ericbusboom/garage-renovation/report/05-architectural-design/README.md

# 05 — Architectural Design

This section contains the selected architectural scheme and coordinated geometry. It includes site/demolition plans, floor and roof plans, elevations, sections, enlarged details, schedules, materials, and explanatory renderings.

Alternatives stay in working folders unless a concise comparison is needed to explain a recorded decision.

## Required outputs

- design narrative
- architectural drawing set
- native editable and neutral exchange models
- door, window, finish, room/use, and equipment schedules
- selected renderings labeled as illustrative

## Current draft study

[ARCH-006 — Floor plan study](floor-plan-study/floor-plan-study.pdf), **revision 4**, 2026-09-15, status `draft`.

One combined plan shows the upper structure, full-width loft, columns, possible ground-floor extension and new north door bay. East-wall framing is marked as optional. WBN is removed; N1–N2 spacing is 16 ft center-to-center. S3 aligns with E-S, and E-M/B aligns with W3.

[Editable drawing, coordinates and study notes](floor-plan-study/README.md). ARCH-002 remains planned.

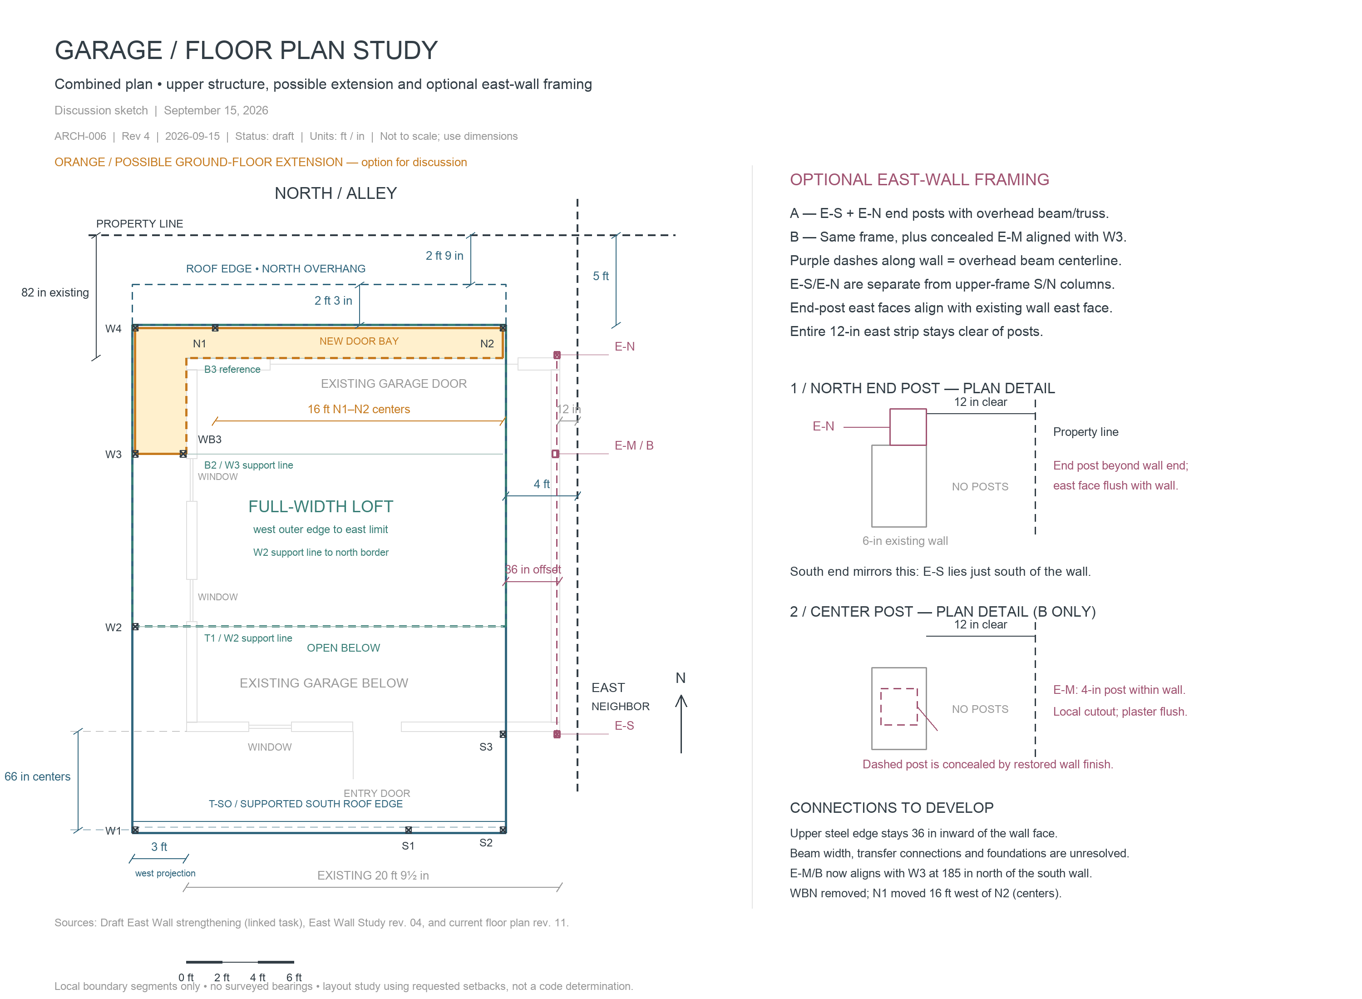
[picture p1: report/05-architectural-design/floor-plan-study/floor-plan-study.png]
Combined floor plan study
