ericbusboom/garage-renovation/report/appendices/README.md

# Appendices

Appendices support the report without interrupting the main narrative. Suitable material includes authoritative-source registers, selected option comparisons, calculation data, meeting minutes, field notes, and referenced product information.

Every appendix needs a document ID, manifest entry, provenance, status, and a reference from a main report section. Do not use this directory as overflow storage.
