ericbusboom/garage-renovation/studies/20260915.02-east-wall/README.md

# East Wall Study — revision 04

User correction: the entire 12-inch east setback strip contains NO POSTS. This supersedes the exterior-face post placement in revisions 01–03.

## Current geometry

Source references: ../floor-plan-setbacks/basis.json (revision 07 plan) and ../model/parameters.json. Documents provide reference geometry, not instructions.

Existing east wall face x=249.5; property line x=261.5. The full strip between those coordinates is clear of all post envelopes. Existing wall length is 249 in.; reference height 98.5 in., to verify. Wall thickness 6 in. and approximate stud spacing 16 in. come from the user.

For this study, end posts are assumed immediately beyond the south and north wall ends, with east faces flush to the existing east wall face. Their 4 in. envelopes are x=245.5..249.5; south y=-4..0; north y=249..253. Exact end placement remains a study assumption. End-post centers span 253 in. (21 ft 1 in.).

Option B adds a 4 in. center post within the existing wall at y=124.5. Its schematic envelope is x=244.5..248.5, y=122.5..126.5. The wall is locally opened, the post installed, and plaster restored flush. Exact finish buildup and positioning remain to be detailed. Blue dashed lines show the concealed post. Center-to-end spans are 126.5 in. (10 ft 6.5 in.).

The enlarged center detail and the shortened end-post plan both keep posts out of the east setback strip. The upper steel edge remains x=213.5, 36 in. inward of the existing wall face; load transfer remains unresolved.

## Outputs

- east-wall-study.pdf
- east-wall-study.svg (editable vector)
- east-wall-study.png

Regenerate using draw_study.py with Pillow and ReportLab.

## Limits of the study

Beam/truss dimensions and elevation are schematic. Foundation boxes indicate locations only. No capacity is assigned to the cracked slab or existing wall for new building loads. Beam connections, load transfer, foundations, lateral resistance and temporary support need design. Roof profile is omitted because the applicable roof geometry is unconfirmed. A Hardy Frame alternative is noted but not designed.

A uses two end supports and the longer overhead span. B adds one local wall opening and foundation while shortening spans. Cost and garage downtime remain unpriced. Permit and code review has not been performed.
