ericbusboom/garage-renovation/studies/20260927.01-patio-awning/setback-research.md

# Patio awning near the property line — San Diego code research

2026-09-29. Working research note, not a permit determination. Parcel facts from LAND-006 (report/03-land-use-and-permitting/setback-extension-research.md): 1370 Wilbur Ave, RS-1-7, Coastal Overlay N-APP-2 (non-appealable), lot ≈ 49 × 122 ft.

## Answer in brief

With posts on the west fence line the awning is inside the required side yard, and the City's rule for this kind of structure is **5 ft from any property line**. The distances that matter:

| Distance from the property line | What the code says |
|---|---|
| 0 to under 2 ft | CRC Table R302.1(1): roof projections **not allowed**. SDMC: no residential projection or patio rule allows it. |
| 2 ft to under 2 ft 6 in | CRC allows a projection with 1-hr underside, heavy timber or FRT wood; SDMC still bars it (every projection rule stops at 2′-6″). |
| 2 ft 6 in to under 5 ft | SDMC allows only building-attached projections: eaves (a)(1), and openly supported projections/trellises (a)(2) that are ≥ 50 % open in plan, up to 6 ft or half the yard deep. A solid fabric sheet on posts is neither. CRC: 1-hr underside or heavy timber/FRT for projections under 5 ft. |
| 5 ft and more | SDMC §131.0461(a)(8): patio structures may sit in the side or rear yard. |
| Outside the required yard (side 4 ft, or 8 % of width ≈ 3.9 ft; rear 13 ft, alley credit may leave 5 ft) | No encroachment rule needed. Permit-exempt if ≤ 300 sf, ≤ 12 ft high and not in any yard (§129.0203(a)(12)). |

So a fabric roof on the P2–P3–P4 fence posts does not fit any by-right rule. The posts stop being "fence" once they carry the awning: SDMC defines a fence as a barrier that "supports no load other than its own weight."

## Sources read

- **SDMC §131.0461(a)** (Ch 13 Art 1 Div 4, 9-2026 edition), permitted projections and encroachments in RS zones:
  - (1) eaves: ≤ 6 ft or 50 % of yard into it, **not closer than 2′-6″** to the line, 6′-8″ clearance.
  - (2) openly supported projections incl. trellises: ≤ eave height, **≥ 50 % open in plan**, ≤ 6 ft or 50 % of yard, **not closer than 2′-6″**, 6′-8″ clear. (Diagram 131-04T shows them projecting from a building wall.)
  - (8) **patio structures** in side or rear yard: **not closer than 5 ft to any property line**, open on at least three sides except columns ≤ 18 × 18 in, columns ≥ 8 ft on centre, roof no higher than the house eave or second-floor sill.
  - (12) non-habitable accessory buildings (the garage route in LAND-006): no stated minimum, ≤ 15 ft high, ≤ 30 ft long in a setback, ≤ 525 sf GFA.
- **SDMC §113.0103 definitions:** "Awning" is supported entirely from a building's exterior wall, so a post-supported sheet is not an awning under the Code. "Fence" supports no load but its own weight. "Structure" includes a post or shelter.
- **SDMC §129.0203(a)(12):** patio covers are exempt from a building permit if ≤ 300 sf projected roof, not in any yard, ≤ 12 ft high, and not in the appealable Coastal area or a Planned Development. (a)(2): fences ≤ 7 ft need no permit. (a)(10): wall-hung window awnings ≤ 54 in projection.
- **IB 206 Patio Covers** (rev. 3-2026): one-story, ≤ 12 ft, open on two or more sides; fire separation per CRC "based on the distance … from a real or assumed lot line"; Class A roof covering assembly; lists the Coastal Zone as needing a permit, which is stricter than the SDMC text.
- **SDMC §142.0310(d):** fences in side and rear yards up to 9 ft; anything above 6 ft must be open fence.
- **SDMC §126.0704(a):** improvements to existing structures are exempt from a Coastal Development Permit unless on a beach or bluff, adding ≥ 10 % floor area, intensifying use, etc. A patio cover here should be exempt; confirm at intake.
- **CRC 2025 Table R302.1(1):** projections under 2 ft fire separation distance are not allowed; 2 to under 5 ft need 1-hr underside, heavy timber or fire-retardant-treated wood.

## What it means for this design

- Fabric plan area is about 162 sf (under the 300 sf exemption size), but the exemption is lost because the awning is in a yard.
- **Posts P2, P3 and P4 are on the line.** To comply by right, the awning's edge and any posts carrying it would have to stay 5 ft off the west line, and 5 ft off the rear line if P1–P2 is near it. About 64 sf of the current 162 sf lies within 5 ft of the west line.
- The pillar end (T1, T2) is part of the garage, which already sits in the east setback under (a)(12). Whether the City would treat a fabric roof attached to it as part of that accessory building is an open question. It would have to count toward the 30 ft and 525 sf limits and stay one story; an open-sided cover is not obviously a "building."
- Water: about 40 % of the roof sheds off the P2–P3 edge on the fence. Nothing found in the zoning code on this, but dumping roof water onto a neighbour is a civil-nuisance risk; a gutter along that edge is advisable in any scheme.
- Fabric: IB 206 asks for a Class A roof covering; fabric may need a listed flame-resistant (e.g. NFPA 701) material, which plan check would decide.

## Open questions for DSD (a free 15-min counter or phone consult)

1. Is a fabric shade sail on permanent posts a "patio structure" under §131.0461(a)(8)?
2. Can it attach to the garage (in the east setback under (a)(12)) and be treated as part of that accessory structure?
3. Where is the rear lot line relative to P1–P2, and does alley credit set the rear yard at 5 ft?
4. Is a Class A covering required for fabric, or will a flame-resistant listed fabric do?

## Fabric-specific search (2026-09-29, second pass)

Question: does a fabric awning or shade sail fall under different rules than a built patio cover?

**Short answer: no fabric exemption was found. The fabric gets no closer to the line, and it adds two material requirements: a Class A roof rating and flame-resistant fabric.**

### San Diego Municipal Code

- Every division of SDMC Chapters 11–14 was downloaded and searched for fabric, canvas, shade sail, shade cloth, membrane, tent and canopy. The only hits are campground tents (§141.06xx) and the adoption of CBC Appendix Q tents for emergency housing. The Land Development Code has **no rule for shade sails or fabric structures**, so the City classifies one under its existing terms.
- "Structure" includes any "post … or shelter" composed of parts joined together (§113.0103). A sail on posts is a structure. "Awning" requires support entirely from a building wall, so a post-supported sail is not an awning under the SDMC.
- §149.0107 adopts **CRC Appendix BF, Patio Covers**. BF102.1 defines a patio cover as "a structure with open or glazed walls that is used for recreational, outdoor living purposes associated with a dwelling unit." It sets no roof material, so a fabric roof fits the definition. BF101.2 says patio covers may not be used as "carports, garages, storage rooms or habitable rooms." A work patio sheltering storage cabinets could be classed instead as an accessory structure under the main CRC; the yard rules apply either way.

### Building and fire codes on fabric

- **CBC §3102 membrane structures** (tensile membrane, membrane-covered cable, etc.) erected **180 days or longer**: designed to ASCE 55. The membrane must be noncombustible or flame resistant per CCR Title 19 Div 1 Ch 8, i.e. State Fire Marshal-listed fabric. A sail tensioned between posts and a mast by cables is a tensile membrane structure. The CRC has no membrane chapter, so a plan checker would likely apply this through engineered design.
- **CFC §3101.1 Exception 4:** "Tensioned membrane roof materials supported by rigid frames or installed on a mast and cable system" that conform to a building-code type of construction are not tents. They are regulated as buildings/structures, not by the fire code's tent chapter.
- **CBC §3105 awnings and canopies:** fabric coverings must pass NFPA 701 or equivalent. Exception: the fire-propagation and flame-spread tests do not apply to awnings on detached one- and two-family dwellings. The sentence requiring fabrics to be flame resistant per Title 19 is not excepted.
- **Roof rating:** San Diego amendment **CRC R902.1.4: "All newly constructed roofs shall be covered with a fire-retardant roof covering that is at least Class 'A'."** IB 206 repeats this for patio covers ("Roofing materials must be a Class A-listed roof covering assembly"). Base CRC R902.1 also requires a rated covering where the roof edge is less than 3 ft from a lot line. Class A is by ASTM E108 / UL 790. PTFE-coated fiberglass architectural membrane is sold as Class A; most shade-sail fabrics (HDPE knit, many PVC-coated polyesters) carry flame-resistance (NFPA 701 / SFM) listings, not a roof class. Check the maker's E108 listing before choosing fabric.

### Temporary use

- Under the CFC, fabric up **less than 180 days in 12 months** is a temporary tent/membrane structure. Open-sided tents up to 700 sf need no fire permit, but they need 12 ft of clearance to structures, and §3103.7.2 keeps tents 20 ft from lot lines. Attached to the garage pillar and posted on the fence, it fails both, so the temporary route gives no relief near the line. Permanent posts remain structures for zoning in any case.

### Effect on the distance answer

Unchanged. Zoning does not care what the roof is made of: the 5 ft patio-structure rule (§131.0461(a)(8)) and the CRC projection limits (nothing under 2 ft, protected under 5 ft) apply to a fabric roof as to a solid one. Fabric adds material requirements: a Class A-rated covering (unless DSD accepts that permeable shade cloth is not a "roof") and SFM-listed flame-resistant fabric.

### Added questions for DSD

5. Is a permeable shade-cloth sail a "roof" subject to R902.1.4 Class A, or a shade screen that is not?
6. Would they review a cable-tensioned sail under CRC Appendix BF (patio cover) or as a CBC §3102 tensile membrane structure (ASCE 55, SFM-listed fabric)?

Sources: SDMC Ch 11–14 (docs.sandiego.gov/municode); CRC 2025 Appendix BF (up.codes); CBC 2025 Ch 31 §3102, §3105 (up.codes); CFC 2025 Ch 31 §3101.1, §3103 (up.codes); San Diego CRC amendments R902.1.4 (up.codes San Diego Residential Code); IB 206.
