ericbusboom/garage-renovation/render/20260908.03-garage-site/SITE-NOTES.md

# Photo-informed site render

The proposed garage is retained from the supplied design package. This pass reconstructs its surroundings using IMG_4198–IMG_4201, with clear reference frames extracted from the supplied Live Photo MOV files. The HEIC-to-JPEG conversion yielded black frames on this machine, so those conversions were not used.

Observed details incorporated: blue-gray house with white trim and dark roof, rear French doors and sash windows, charcoal irregular flagstone paths with light joints, gravel garden beds, mature overhead trees, dense shrubs, burgundy strap-leaf plants, cobalt pots, and a timber-slat bench with dark supports.

Site spacing is an estimate. The house rear facade is placed approximately 15.3 m south of the garage's south wall. House dimensions, fence locations, plant positions, path alignment and grade are illustrative reconstructions, not a survey or photogrammetric result. The front-house stone foundation and parked car are not visible from these garden views and have not been modeled.

Two existing solid garage wall meshes were incorrectly tagged as glass in the source package; this scene assigns those wall meshes opaque warm stucco. The north wall mesh surrounding the garage door is also assigned stucco. The glazing panes remain glass. This changes materials, not opening geometry.

Files:
- garage-site.blend — editable scene containing the proposed garage and photo-informed site.
- site-garden.png — garden approach toward the garage.
- site-garage-angle.png — closer southwest garden view focused on the garage.

The house is existing context only; no house renovation is proposed. The earlier house-facing render was withdrawn from the wiki at the user’s request.
- build_site.py — repeatable Blender 5 scene-building script; loads garage.blend.

Rendering host: ros@buzzkill, /home/ros/garage-render. Cycles CPU rendering; all plants, paths, and materials are procedural meshes/shaders with no external asset dependencies.
