ericbusboom/garage-renovation/studies/20260919.01-cabinet-frame/support-basis-update.md

# Updated support basis

User clarification: all specified structural columns bear on concrete pilings, reportedly about 18 inches diameter and 36 inches deep. All specified beams are intended to be structural. Include all those columns as support nodes; do not omit a support merely because it is outside the garage footprint. West extensions are structural members and shown solid.

The weak garage slab does not serve as the assumed foundation for these specified piled columns. Cabinet frame uprights are a separate question: the clarification does not unambiguously establish pilings beneath those interior uprights.

Piling dimensions remain approximate. Soil, reinforcement, embedment, column connections, member properties and loads are still needed to verify capacity. Support does not imply moment fixity: base/beam rotational restraint is not established.

The previous single-span calculation was an illustrative demand relation, not the complete frame analysis. Analyze the whole specified frame using every support, continuity as supported by actual connections, and compatible load paths. Do not silently classify any specified beam as nonstructural. Discuss any proposed removal or reduced structural role with the user.

This update supersedes any prior implication that specified exterior columns rely on the weak garage slab. Cabinet-location and cabinet-construction assumptions remain pending clarification.
