ericbusboom/garage-renovation/studies/20260908.01-structural-design/all-truss-elevations.pdf

3 5 | 3 5 | 3 5 | 3 5 | 3 5 | 3 5

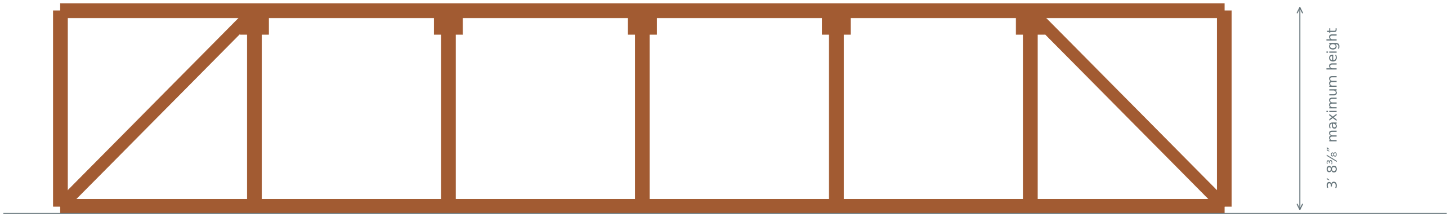
[picture p30: figure]
3 8 maximum height

20 6½ overall framing-line length

# T-S · TRUSS ELEVATION

West east · dimensions along the framing line · member layout projected directly from the current 3D model

## COMMON BOTTOM = 8 2½ ABOVE GROUND · COLUMN-SUPPORTED

Six equal panel bays; dimensions are centerline spacing, not clear openings.
Model layout: verticals throughout; diagonals in the two end bays; central storage bays open.
At station 0 (south wall).
End-braced rectangles require engineered moment joints / Vierendeel action; web layout is illustrative.

Concept geometry, not fabrication drawings. Member sizes, joints, bracing and bearing details require design. The shallow hip roof cap sits above the rear ceiling datum; its internal framing has not been laid out.

3 1 | 3 1 | 3 1 | 3 1 | 3 1 | 3 1

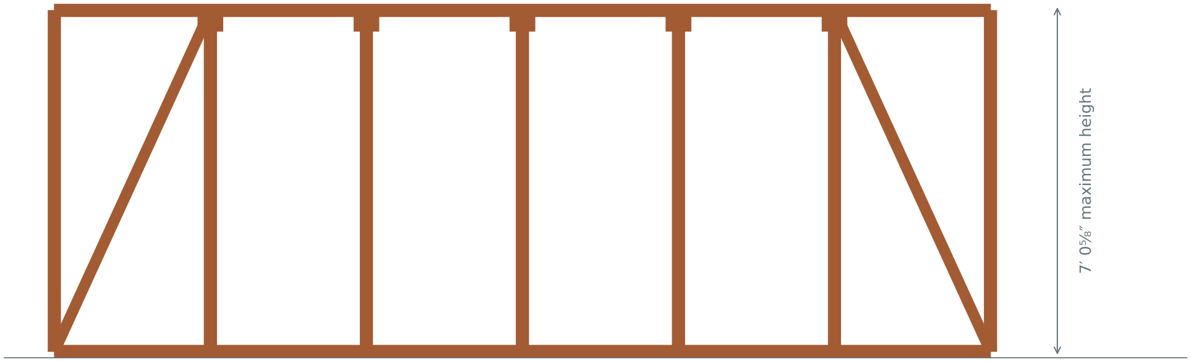
[picture p31: figure]
7 0 maximum height

18 8¼ overall framing-line length

# T1 · TRUSS ELEVATION

West east · dimensions along the framing line · member layout projected directly from the current 3D model

## COMMON BOTTOM = 8 2½ ABOVE GROUND · COLUMN-SUPPORTED

Six equal panel bays; dimensions are centerline spacing, not clear openings.
Model layout: verticals throughout; diagonals in the two end bays; central storage bays open.
At station 69¾ north of south wall.
End-braced rectangles require engineered moment joints / Vierendeel action; web layout is illustrative.

Concept geometry, not fabrication drawings. Member sizes, joints, bracing and bearing details require design.

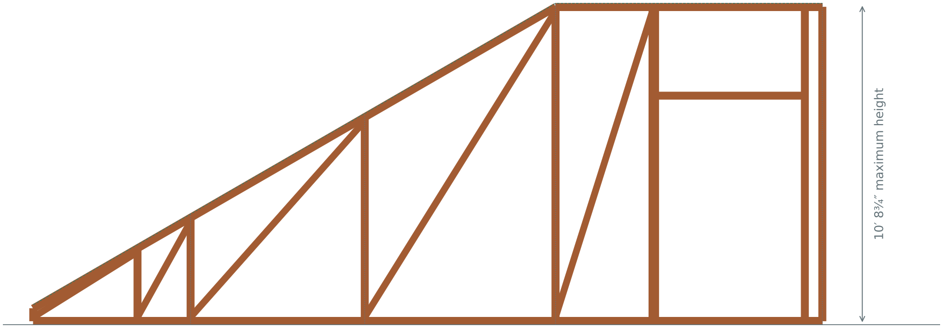
[picture p32: figure]
10 8¾ maximum height

26 4 overall framing-line length

# T-W · TRUSS ELEVATION

South north · station zero = south exterior garage wall · member layout projected directly from the current 3D model

## COMMON BOTTOM = 8 2½ ABOVE GROUND · COLUMN-SUPPORTED

UPRIGHT STATIONS FROM SOUTH WALL (in): -63, -21.25, 0, 69.75, 146.15, 185, 186, 246, 253
PANEL SPACINGS (in): 41.75, 21.25, 69.75, 76.4, 38.85, 1, 60, 7
DEPTHS: south tip 8 ; south wall 3 8 | ; at T1 7 0 | ; plateau 10 8¾ .
West door header is included. Closely spaced uprights at 185 / 186 in are retained from the model; opening framing needs coordination.

Concept geometry, not fabrication drawings. Member sizes, joints, bracing and bearing details require design.

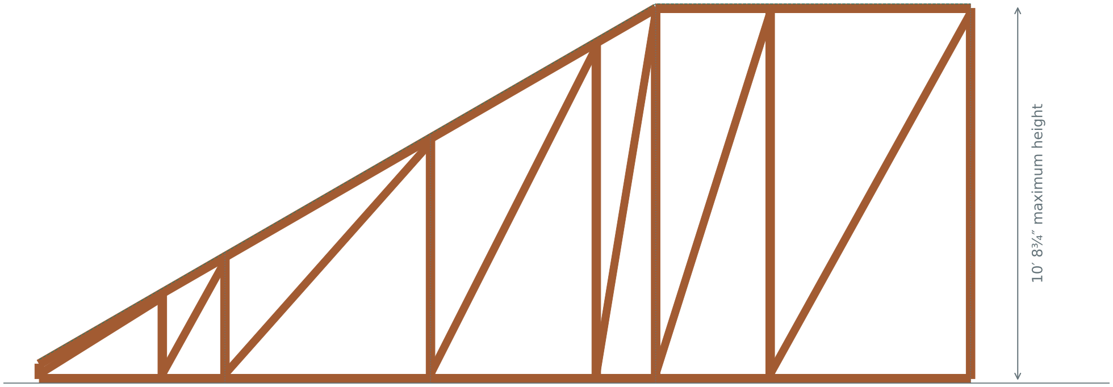
[picture p33: figure]
10 8¾ maximum height

26 4 overall framing-line length

# T-E · TRUSS ELEVATION

South north · station zero = south exterior garage wall · member layout projected directly from the current 3D model

## COMMON BOTTOM = 8 2½ ABOVE GROUND · COLUMN-SUPPORTED

UPRIGHT STATIONS FROM SOUTH WALL (in): -63, -21.25, 0, 69.75, 126, 146.15, 185, 253 PANEL SPACINGS (in): 41.75, 21.25, 69.75, 56.25, 20.15, 38.85, 68
DEPTHS: south tip 8 ; south wall 3 8 | ; at T1 7 0 | ; plateau 10 8¾ .
Support axis: N2 / S2 / optional S3.

Concept geometry, not fabrication drawings. Member sizes, joints, bracing and bearing details require design.

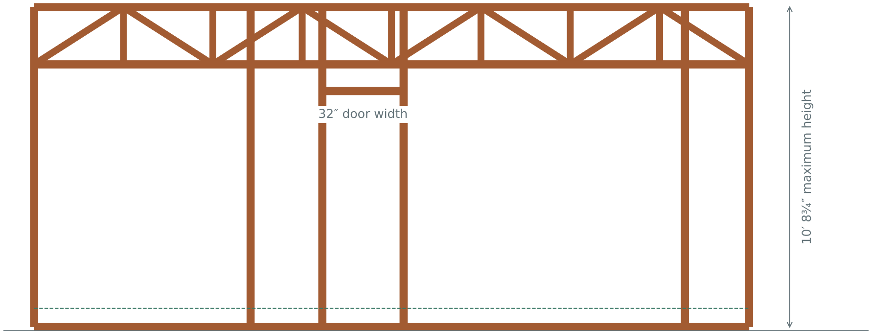
[picture p34: figure]
32 door width; 10 8¾ maximum height

23 5½ overall framing-line length

# T-N · TRUSS ELEVATION

West east · dimensions along the framing line · member layout projected directly from the current 3D model

## COMMON BOTTOM = 8 2½ ABOVE GROUND · COLUMN-SUPPORTED

UPRIGHT STATIONS X (in): -32, 53.25, 81.5, 113.5, 224.25, 249.5.
HEADER: nominal 24 deep; eight equal bays of 35 3/16 in. Door: 32 wide × 84 high above loft floor.
DOOR center X = 97½ ; opening edges X = 81½ / 113½ . Floor is 8¾ above common truss bottom.
North wall windows and side webs require coordination. Overall truss includes west walkway width; it is not loft-floor width.

Concept geometry, not fabrication drawings. Member sizes, joints, bracing and bearing details require design.
