ericbusboom/garage-renovation/studies/20260908.01-structural-design/dimensioned-trusses-and-west-section.pdf

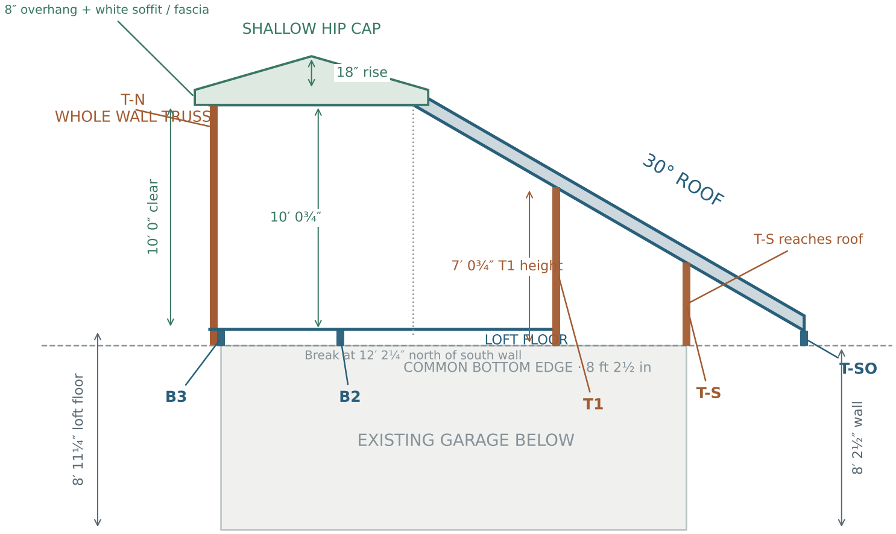
[picture p35: figure]
EXISTING GARAGE BELOW; LOFT FLOOR; 30° ROOF; SHALLOW HIP CAP; 18 rise; 8 overhang + white soffit / fascia; T-N WHOLE WALL TRUSS; COMMON BOTTOM EDGE · 8 ft 2½ in; T-S reaches roof; 7 0¾ T1 height; 10 0 clear; 8 2½ wall; 8 11¼ loft floor; Break at 12 2¼ north of south wall

68 | 115¼ | 69¾ | 63
9 0¾ cap base run | 17 5¼ sloping run

# WEST SECTION · ROOF AND FRAMING CLEARANCES

Looking east · north at left · vertical dimensions to ROOF UNDERSIDE · conceptual member elevations

Datum: loft floor = 8 11¼ above ground. Roof underside starts at T-SO top = 8 10½ ; it rises to 10 0 above loft floor.
ALL beam and truss bottoms = wall top, 8 2½ . Columns carry the loads; existing walls are not assigned new gravity load.
Trial beam depths: T-SO / B2 / B3 = 8 in. T-S and T1 extend from wall-top datum to roof underside. Loft floor is ¾ in above the 8-in beams. Roof band = 8 in, provisional.

Longitudinal T-W / T-E and B-WO are outside this interior cut; their BOTTOM edges share the same wall-top datum. Depths remain to be designed.
Hip cap: 18-in rise above eaves, 8-in overhang and fascia; rear ceiling datum unchanged. North wall edge = 255 in; cap eave = 263 in.

Column-supported bearing | Column-supported bearing

18 8¼ · bearing-center span

7 0¾
wall top to roof
37 | 37 | 37 | 37 | 37 | 37

# T1 · DIMENSIONED TRUSS CONCEPT

View from south looking north · west at left · T1 terminates at T-E · bottom edge at common wall-top datum · column-supported framing

Height is set by the roof underside. Six equal panel bays are a drawing assumption. Panel dimensions are centerline spacing, not clear cabinet openings. Rectangular central bays require designed moment connections / Vierendeel action; end diagonals alone are not a complete truss design.

T1 bottom edge = 8 ft 2½ in; top edge = 15 3¼ above ground, at the roof underside. No gap above T1. Loads go to column-supported framing. Member widths, welds, bearing seats, lateral bracing and cabinet loads remain to be designed.

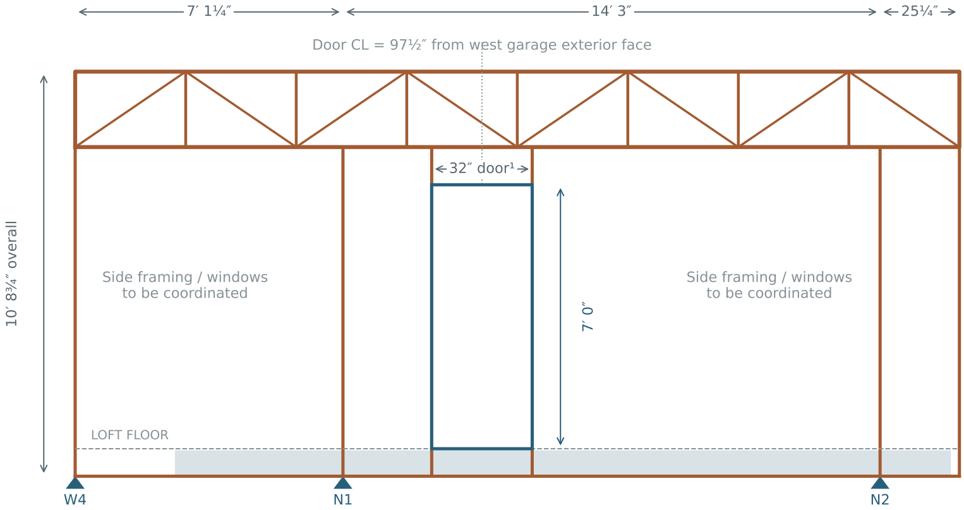
[picture p36: figure]
LOFT DOOR; 32 door¹; 10 8¾ overall

Side framing / windows to be coordinated LOFT FLOOR | Side framing / windows to be coordinated

B3 · 8-in trial beam · same bottom datum as T-N

23 5½ · overall T-N framing line

10 0 floor to roof underside

24
header

Door CL = 97½ from west garage exterior face

# T-N · NORTH WALL / DOOR TRUSS CONCEPT

### View from inside looking north · west at left · loft floor is the zero datum

Seven-foot door retained under a trial 24-in trussed header. Header underside is 8 ft above floor: 12 in above nominal door top. ¹32-in door width retained from earlier drawing; actual rough opening and connection allowances are not yet specified.

T-N overall height = 10 ft 8¾ in, from common wall-top datum to roof underside; loft floor is 8¾ in above that datum.
Column-supported structure. Door threshold is at loft floor. Side-frame webs, windows, connections and beam depths remain conceptual.
