ericbusboom/garage-renovation/studies/20260908.01-structural-design/section-and-plan.pdf

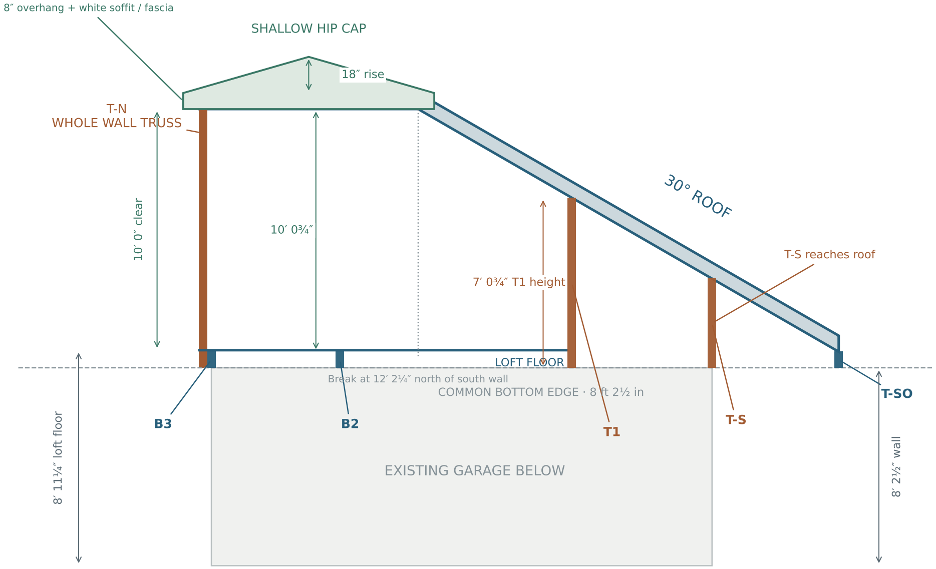
[picture p37: figure]
EXISTING GARAGE BELOW; LOFT FLOOR; 30° ROOF; SHALLOW HIP CAP; 18 rise; 8 overhang + white soffit / fascia; T-N WHOLE WALL TRUSS; COMMON BOTTOM EDGE · 8 ft 2½ in; T-S reaches roof; 7 0¾ T1 height; 10 0 clear; 8 2½ wall; 8 11¼ loft floor; Break at 12 2¼ north of south wall

68 | 115¼ | 69¾ | 63
9 0¾ cap base run | 17 5¼ sloping run

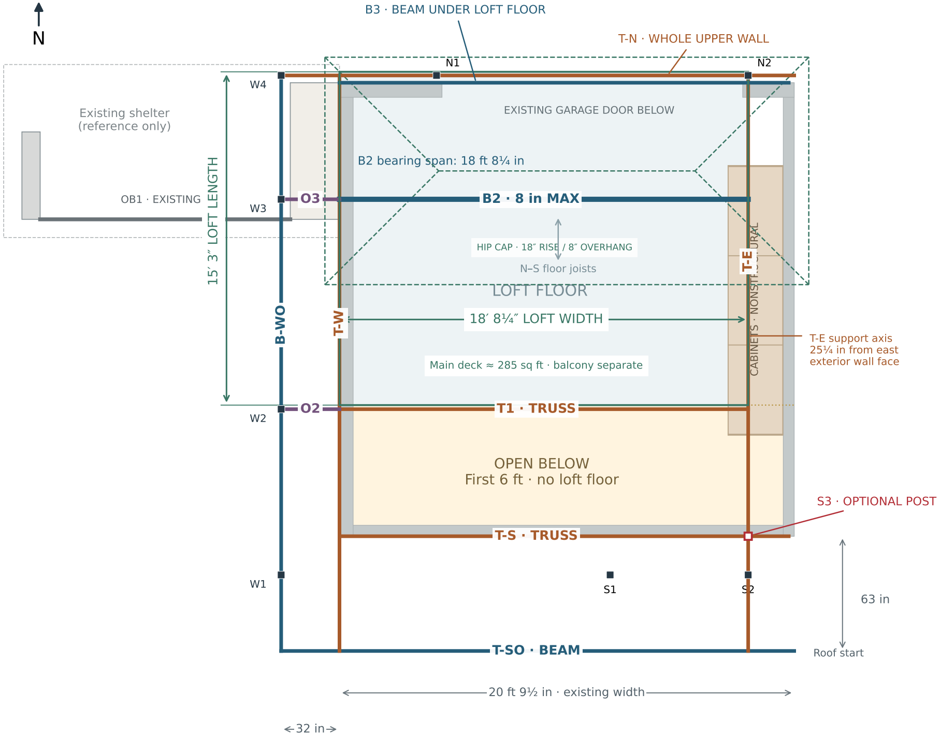
[picture p38: figure]
EXISTING GARAGE DOOR BELOW; CABINETS · NONSTRUCTURAL; OB1 · EXISTING; Existing shelter (reference only); S3 · OPTIONAL POST; OPEN BELOW First 6 ft · no loft floor; LOFT FLOOR; 18 8¼ LOFT WIDTH; 15 3 LOFT LENGTH; Main deck; 285 sq ft · balcony separate; 20 ft 9½ in · existing width; Roof start; T-E support axis 25¼ in from east exterior wall face; B2 bearing span: 18 ft 8¼ in; T-SO · BEAM; T-S · TRUSS; T1 · TRUSS; B2 · 8 in MAX; B3 · BEAM UNDER LOFT FLOOR; T-N · WHOLE UPPER WALL

| HIP CAP · 18 RISE / 8 OVERHANG N S floor joists

## MEMBER REGISTER

T-S | Wall-top datum truss · reaches roof
T-E | East truss · aligned S2 / S3 / N2
T-W | West wall truss
B3 | North wall BEAM · under loft floor
T-SO | Southernmost BEAM · common datum
T1 | Truss · wall-top datum to roof
B2 | Main loft beam · 8 in max depth
T-N | North wall truss · includes loft door
B-WO | West outer longitudinal beam
O2 / O3 | Transfers from west wall to outer posts
OB1 | Existing shelter front beam

## DRAWING BASIS

S2 moved east 12¾ in to align with N2. Gray = existing walls; brown fill = cabinets. Hollow red S3 = optional 4-inch post. Solid orange = truss; B-S removed.
Truss depth is vertical, not plan width.
All bottoms = wall top; columns carry loads.

# GARAGE · SECTION + FRAMING PLAN

## Matching member names · all beam and truss bottoms at 8 2½ · columns carry the loads

01 WEST SECTION | LOOKING EAST
02 TOP-DOWN FRAMING PLAN | NORTH UP
Orange = truss | Blue = beam | Green dashed = hip cap outline / hips. T-SO is a BEAM.

T1 replaces B1 and reaches the roof. T-N is the whole north upper-wall truss. B3 is the north beam below the loft floor. B-S is removed.

Roof: 30° from T-SO, then 18-in hip cap with 8-in overhang / fascia. Rear ceiling remains 10 ft above trial loft floor.
T-W / T-E / B-WO are outside the interior section cut and appear in plan. South support-row / T-SO connections remain unresolved; sizes are conceptual.

3 5 | 3 5 | 3 5 | 3 5 | 3 5 | 3 5

3 8 maximum height

20 6½ overall framing-line length

# T-S · TRUSS ELEVATION

West east · dimensions along the framing line · member layout projected directly from the current 3D model

## COMMON BOTTOM = 8 2½ ABOVE GROUND · COLUMN-SUPPORTED

Six equal panel bays; dimensions are centerline spacing, not clear openings.
Model layout: verticals throughout; diagonals in the two end bays; central storage bays open.
At station 0 (south wall).
End-braced rectangles require engineered moment joints / Vierendeel action; web layout is illustrative.

Concept geometry, not fabrication drawings. Member sizes, joints, bracing and bearing details require design. The shallow hip roof cap sits above the rear ceiling datum; its internal framing has not been laid out.

3 1 | 3 1 | 3 1 | 3 1 | 3 1 | 3 1

7 0 maximum height

18 8¼ overall framing-line length

# T1 · TRUSS ELEVATION

West east · dimensions along the framing line · member layout projected directly from the current 3D model

## COMMON BOTTOM = 8 2½ ABOVE GROUND · COLUMN-SUPPORTED

Six equal panel bays; dimensions are centerline spacing, not clear openings.
Model layout: verticals throughout; diagonals in the two end bays; central storage bays open.
At station 69¾ north of south wall.
End-braced rectangles require engineered moment joints / Vierendeel action; web layout is illustrative.

Concept geometry, not fabrication drawings. Member sizes, joints, bracing and bearing details require design.

10 8¾ maximum height

26 4 overall framing-line length

# T-W · TRUSS ELEVATION

South north · station zero = south exterior garage wall · member layout projected directly from the current 3D model

## COMMON BOTTOM = 8 2½ ABOVE GROUND · COLUMN-SUPPORTED

UPRIGHT STATIONS FROM SOUTH WALL (in): -63, -21.25, 0, 69.75, 146.15, 185, 186, 246, 253
PANEL SPACINGS (in): 41.75, 21.25, 69.75, 76.4, 38.85, 1, 60, 7
DEPTHS: south tip 8 ; south wall 3 8 | ; at T1 7 0 | ; plateau 10 8¾ .
West door header is included. Closely spaced uprights at 185 / 186 in are retained from the model; opening framing needs coordination.

Concept geometry, not fabrication drawings. Member sizes, joints, bracing and bearing details require design.

10 8¾ maximum height

26 4 overall framing-line length

# T-E · TRUSS ELEVATION

South north · station zero = south exterior garage wall · member layout projected directly from the current 3D model

## COMMON BOTTOM = 8 2½ ABOVE GROUND · COLUMN-SUPPORTED

UPRIGHT STATIONS FROM SOUTH WALL (in): -63, -21.25, 0, 69.75, 126, 146.15, 185, 253 PANEL SPACINGS (in): 41.75, 21.25, 69.75, 56.25, 20.15, 38.85, 68
DEPTHS: south tip 8 ; south wall 3 8 | ; at T1 7 0 | ; plateau 10 8¾ .
Support axis: N2 / S2 / optional S3.

Concept geometry, not fabrication drawings. Member sizes, joints, bracing and bearing details require design.

32 door width; 10 8¾ maximum height

23 5½ overall framing-line length

# T-N · TRUSS ELEVATION

West east · dimensions along the framing line · member layout projected directly from the current 3D model

## COMMON BOTTOM = 8 2½ ABOVE GROUND · COLUMN-SUPPORTED

UPRIGHT STATIONS X (in): -32, 53.25, 81.5, 113.5, 224.25, 249.5.
HEADER: nominal 24 deep; eight equal bays of 35 3/16 in. Door: 32 wide × 84 high above loft floor.
DOOR center X = 97½ ; opening edges X = 81½ / 113½ . Floor is 8¾ above common truss bottom.
North wall windows and side webs require coordination. Overall truss includes west walkway width; it is not loft-floor width.

Concept geometry, not fabrication drawings. Member sizes, joints, bracing and bearing details require design.
