ericbusboom/garage-renovation/studies/20260915.02-east-wall/east-wall-study.pdf

# EAST WALL STUDY

04 / Posts clear of the entire 12 in. setback | East elevation: looking west; south at left, north at right

September 15, 2026 • Concept comparison only • No structural capacity or permit compliance established

## A / POSTS AT SOUTH AND NORTH ENDS

Existing wall retained; beam or truss spans between new end supports.

E-S | E-N

### EXISTING EAST WALL RETAINED

6 in. wall; studs approx. 16 in. o.c.
Studs diagrammatic; no east openings in source plan.

20 ft 9 in. existing wall

21 ft 1 in. post c/c - assumed end placement

8 ft
2 1/2 in.
ref.

### NEW FRAME / blue

4 in. post envelope requested; section not selected. End posts beyond south / north ends; east faces flush. Beam/truss depth and elevation are schematic.
No new building load assigned to existing wall.

### FOUNDATION / dashed boxes

New supports require a verified foundation solution. Boxes locate support points only; dimensions unresolved. Existing slab is cracked; footing condition is unknown.

### DISRUPTION / concept tradeoff

Two support locations and no central wall opening.
Longer beam span; cost and lifting access remain unpriced.

## B / END POSTS + INSERTED MID-WALL POST

Center post concealed within the wall; local cutout plastered flush after installation.

E-S | E-M | E-N

EXISTING WALL
6 in.; approx. 16 in. o.c. Studs diagrammatic.

20 ft 9 in. existing wall

10 ft 6 1/2 in. c/c | 10 ft 6 1/2 in. c/c

8 ft
2 1/2 in.
ref.
SOUTH | NORTH

### INTERMEDIATE SUPPORT / E-M

4 in. post WITHIN the existing 6 in. wall; see detail below. Blue dashed = concealed post behind restored plaster. Orange zone = local cutout, then plastered back flush. Beam connection and foundation remain unresolved.

### LOAD PATH / to be engineered

Shorter spans, plus a third foundation and connection. No existing-wall bearing credit is assumed in this sketch. Gravity posts alone do not establish lateral resistance.

### HARDY FRAME / alternate to develop

A proprietary panel needs its own width, anchorage and foundation layout; it is not represented by the 4 in. post.

## END POSTS — SETBACK KEPT CLEAR

Upper steel edge | Property line

36 in.

12 in.

VIEW FROM ABOVE / both wall ends
6 in. wall; length shortened in this detail
Full 12 in. strip to property line: NO POSTS

End posts shown beyond wall ends, east faces flush.

End placement assumed for study; center post shown below.

### COORDINATION BEFORE CODE REVIEW

The plan places the upper steel edge 36 in. inward of this wall. Load transfer to this new support line has not been designed. Confirm wall height, roof geometry, loads and soil / footings. Entire one-foot setback strip remains clear of all posts.
Setback, fire separation and construction access remain to check. Staging and temporary support must be planned before opening.

## CENTER POST — INSIDE WALL

VIEW FROM ABOVE / E-M only; post concealed within existing wall.

GARAGE INTERIOR / WEST

EXTERIOR / EAST — 1 ft setback strip begins beyond this wall face

6 in.

### CONCEALED CENTER SUPPORT

Cut out a local section of the existing wall.
Set the 4 in. post inside the wall thickness.
Reinstate the wall finish and plaster flush.
Post centering and cutout width shown schematically. Finish buildup, beam connection and footing to be detailed.

Basis: floor-plan-setbacks revision 07 + model/parameters.json. Height from model; wall thickness / spacing from user. Roof profile omitted: unconfirmed.
