ericbusboom/garage-renovation/studies/20260915.04-floor-plan-setbacks/east-wall-floor-plan.pdf

# EAST WALL STUDY / FLOOR PLAN

### EW-P6 Wall strengthening over the revision 11 plan • north up

Discussion sketch | September 15, 2026
ARCH-006 / P2 | Rev 3 | 2026-09-15 | Status: draft | Units: ft / in | Not to scale; use dimensions

ORANGE / POSSIBLE GROUND-FLOOR EXTENSION — option for discussion

## EAST WALL FRAME / TWO OPTIONS

A — E-S + E-N end posts with overhead beam/truss. B — Same frame, plus concealed E-M aligned with W3. Purple dashes along wall = overhead beam centerline. E-S/E-N are separate from upper-frame S/N columns. End-post east faces align with existing wall east face. Entire 12-in east strip stays clear of posts.

### 1 / NORTH END POST — PLAN DETAIL

12 in clear

NO POSTS

12 in clear

NO POSTS

E-N | Property line
| End post beyond wall end; east face flush with wall.

6-in existing wall

South end mirrors this: E-S lies just south of the wall.

### 2 / CENTER POST — PLAN DETAIL (B ONLY)

E-M: 4-in post within wall. Local cutout; plaster flush.

Dashed post is concealed by restored wall finish.

### CONNECTIONS TO DEVELOP

Upper steel edge stays 36 in inward of the wall face.
Beam width, transfer connections and foundations are unresolved. E-M/B now aligns with W3 at 185 in north of the south wall.
WBN removed; N1 moved 16 ft west of N2 (centers).

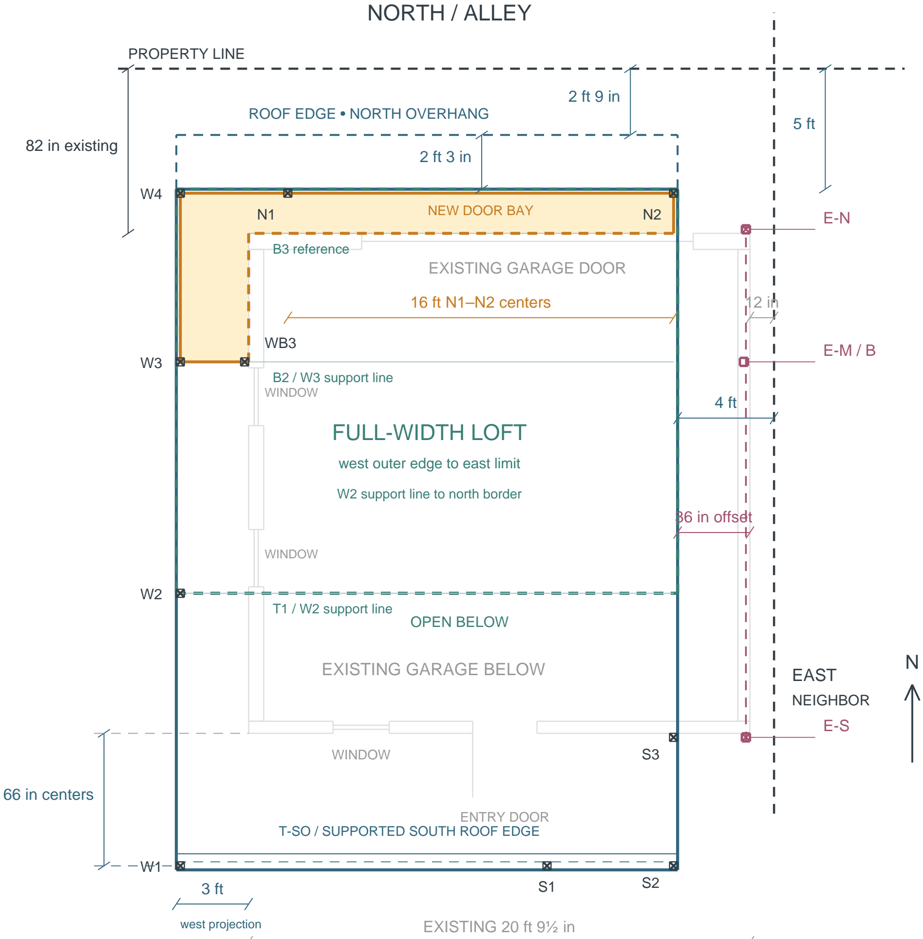
[picture p46: figure]
WINDOW; ENTRY DOOR; EXISTING GARAGE DOOR; EXISTING GARAGE BELOW; NORTH / ALLEY; PROPERTY LINE; EAST; NEIGHBOR; T-SO / SUPPORTED SOUTH ROOF EDGE; ROOF EDGE • NORTH OVERHANG; T1 / W2 support line; B2 / W3 support line; B3 reference; FULL-WIDTH LOFT; west outer edge to east limit; W2 support line to north border; OPEN BELOW; 16 ft N1–N2 centers; NEW DOOR BAY; 82 in existing; 66 in centers; west projection; EXISTING 20 ft 9½ in; 36 in offset

Sources: Draft East Wall strengthening (linked task), East Wall Study rev. 04, and current floor plan rev. 11.

0 ft | 2 ft | 4 ft | 6 ft
Local boundary segments only • no surveyed bearings • layout study using requested setbacks, not a code determination.
