ericbusboom/garage-renovation/studies/20260915.05-stairs/west-elevation-stairs-8ft10.pdf

# STORAGE LOFT / LIFTING STAIR

### West-side elevation · looking east · NORTH ← → SOUTH

ST-02 · Lower loft study · 15 Sep 2026 · Dimensioned study, not a construction drawing

## 01 / STAIR RAISED

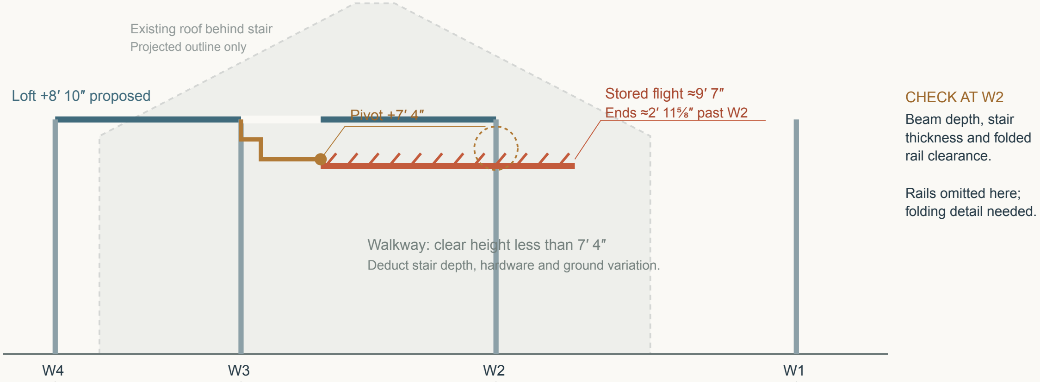
[picture p47: figure]
Existing roof behind stair Projected outline only; Loft +8′ 10″ proposed; Pivot +7′ 4″; Stored flight ≈9′ 7″ Ends ≈2′ 11⅝″ past W2; CHECK AT W2 Beam depth, stair thickness and folded rail clearance.; Rails omitted here; folding detail needed.; Walkway: clear height less than 7′ 4″

W3–W2 9′ 7¼″

Deduct stair depth, hardware and ground variation.

## 02 / STAIR LOWERED

Existing roof behind stair Projected outline only

Loft +8′ 10″ proposed

W4 | W3 | W2 | W1

W3–W2 9′ 7¼″

Pivot +7′ 4″

### 50° study angle

Foot ≈5⅜″ north of W2

FIXED TOP ASSEMBLY
Two 9″ drops;
two 9″ goings +
18″ pivot platform.

Pivot is 36″ south
of the W3 line.

Landing extent to design

ASSUMPTIONS & LIMITS

Loft +106″; pivot +88″; level outside landing at 0″. Heights and 50° pitch are illustrative, not adopted or code-approved. Plan posts retained. Treads and rails schematic, not a stair schedule. Fixed steps, platform and mechanism require design. Loft is only 7½″ above existing wall top. Retained roof / beam / deck fit needs a transverse section; upper roof omitted. Sources: ARCH-006 rev 4 basis.json (plan); model/parameters.json (existing roof). No controlled report drawings changed.
