ericbusboom/garage-renovation/studies/20260915.05-stairs/west-elevation-stairs.pdf

# STORAGE LOFT / LIFTING STAIR

### West-side elevation · looking east · NORTH ← → SOUTH

ST-01 · Draft concept · 15 Sep 2026 · Dimensioned study, not a construction drawing

## 01 / STAIR RAISED

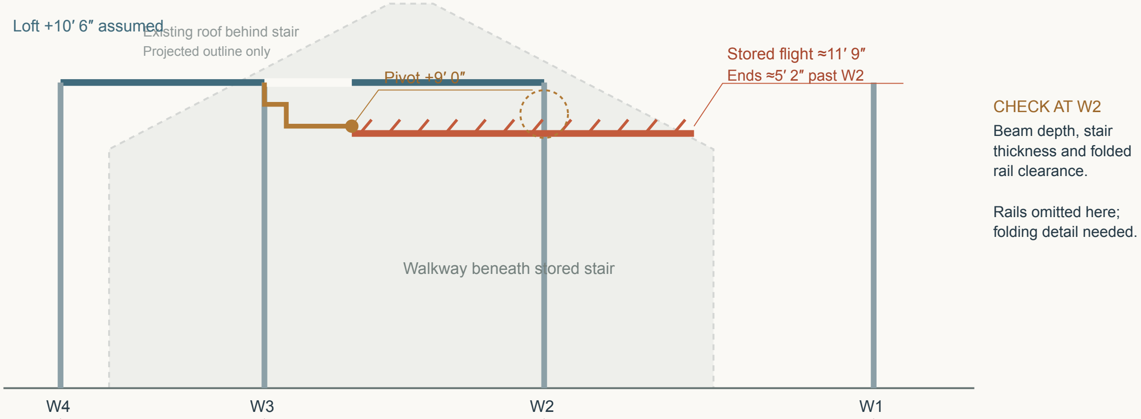
[picture p48: figure]
Existing roof behind stair Projected outline only; Loft +10′ 6″ assumed; Pivot +9′ 0″; Stored flight ≈11′ 9″ Ends ≈5′ 2″ past W2; CHECK AT W2 Beam depth, stair thickness and folded rail clearance.; Rails omitted here; folding detail needed.; Walkway beneath stored stair

W3–W2 9′ 7¼″

## 02 / STAIR LOWERED

Existing roof behind stair Projected outline only

Loft +10′ 6″ assumed

W4 | W3 | W2 | W1

W3–W2 9′ 7¼″

Pivot +9′ 0″

### 50° study angle

Foot ≈11⅜″ past W2

FIXED TOP ASSEMBLY
Two 9″ drops;
two 9″ goings +
18″ pivot platform.

Pivot is 36″ south
of the W3 line.

Landing extent to design

ASSUMPTIONS & LIMITS

Loft +126″; pivot +108″; level outside landing at 0″. Heights and 50° pitch are illustrative, not adopted or code-approved. Plan post locations retained. Fixed assembly, rails, pivot support, beam depths and counterbalance require design. Retained roof is shown behind the stair in projection; this does not establish beam-to-roof clearance. Upper roof omitted. Sources: ARCH-006 rev 4 basis.json (plan); model/parameters.json (existing roof). No controlled report drawings changed.
