ericbusboom/garage-renovation/studies/20260919.01-cabinet-frame/revised-support-review.pdf

### NORTH / GARAGE DOOR

# Structural scheme · cabinet frames + garage-door jamb posts

All specified beams structural · no added gravity load assigned to existing walls · 10 overall beam depth is a target

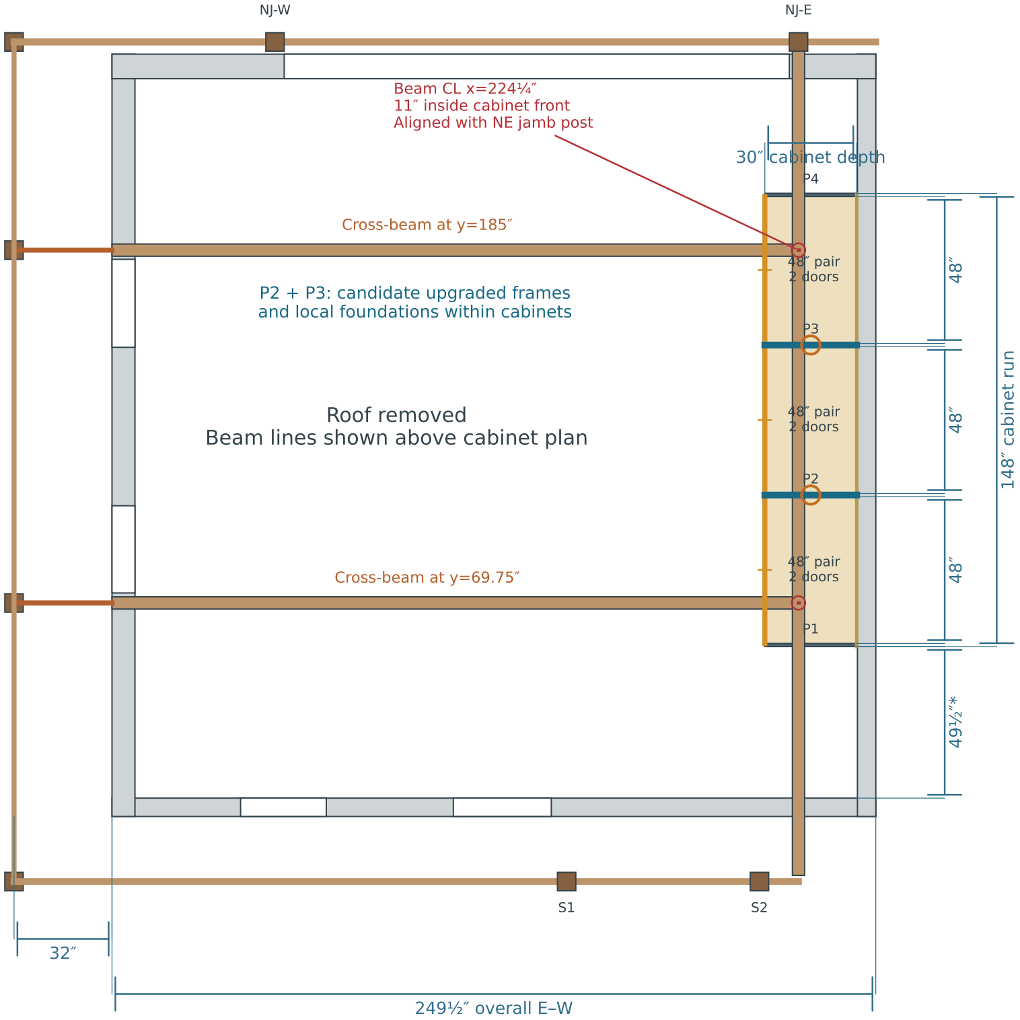
[picture p49: figure]
48 pair 2 doors; Cross-beam at y=69.75; Cross-beam at y=185; 148 cabinet run; cabinet depth; 249½ overall E W; Roof removed Beam lines shown above cabinet plan; Beam CL x=224¼ 11 inside cabinet front Aligned with NE jamb post; P2 + P3: candidate upgraded frames and local foundations within cabinets

Blue: candidate P2/P3 frame upgrades. Orange rings: local foundation work to investigate, not footing size. P1/P4 remain in the support model.

NJ-W and NJ-E sit just outside the existing garage-door opening; they are jamb posts, not the building corners. North header reaches east garage edge.

Cabinet location and south offset retain earlier assumptions. Exterior piling dimensions approximate; cabinet footing locations/capacities need design.

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

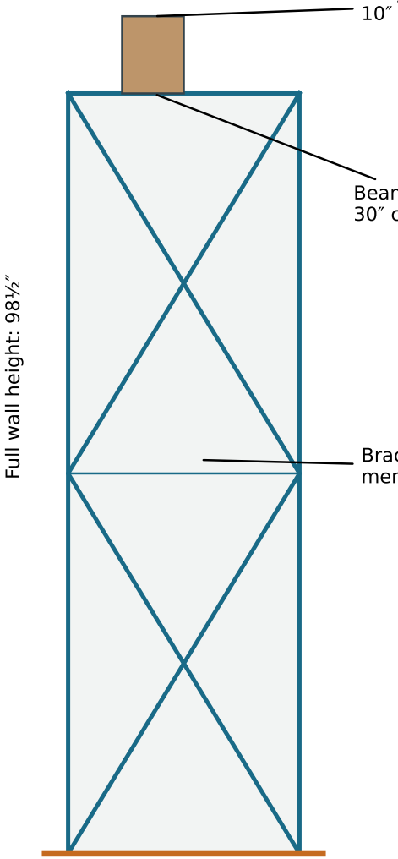
[picture p50: figure]
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
