ericbusboom/garage-renovation/studies/20260921.01-joist-hangers/closed-ceiling-electrical-option.pdf

## CLOSED JOIST CEILING · NO RAISED SERVICE FLOOR

### ordinary hangers + hidden wiring in the 2×8 cavities + east lean-to distribution spine

JH-002
21 SEPTEMBER 2026
BEST VALUE | direct ceiling under joists; keep the W-beams exposed; feed every bay separately from the hidden east chase | NOT FOR CONSTRUCTION

A DIRECT CEILING BELOW THE 2×8s
No raised floor. The joist cavity becomes the service space; the W-beam remains expressed below it.

12″ W-beam

7¼″ joist

≈ 4¾″ beam reveal
5⁄8″ drywall | wood panel / T&G

bored hole near joist centerline

A thin furring layer clears hanger seats, gives the finish a continuous fastening plane, and reduces drywall cracking at hardware.

B EAST LEAN-TO AS THE ELECTRICAL SPINE

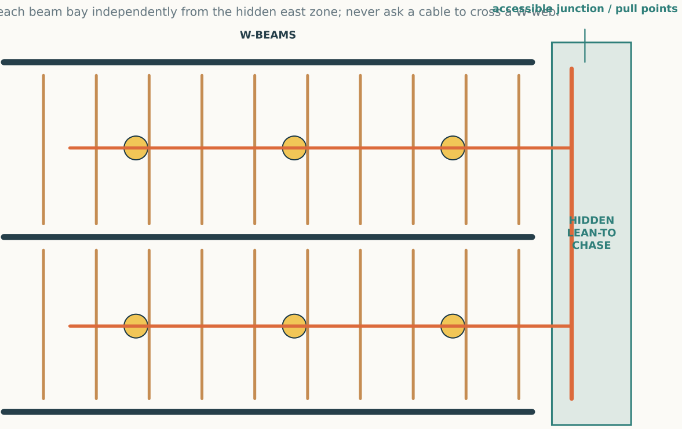
[picture p51: figure]
HIDDEN LEAN-TO CHASE; W-BEAMS; accessible junction / pull points

Feed each beam bay independently from the hidden east zone; never ask a cable to cross a W-web.

lights and cable remain inside one bay

C 2×8 BORING ZONE — SIMPLE, BUT DISCIPLINED

≤ 2⅜″

2″ no-hole zone

2″ no-hole zone

For a 7¼″ sawn joist: hole diameter ≤ one-third depth (2.42″), ≥ 2″ from top, bottom, other holes and any notch.

D WHAT THE ROOM WILL FEEL LIKE

DRYWALL
quietest + brightest

best fire/acoustic finish

VENEER PLYWOOD
warm modern grid

expressed ⅛″ reveals

T&G WOOD
richest / most crafted

more joints and movement

Final hanger/nailer, hole locations, ceiling fire rating, fixture listings, conductor support and junction-box access require project-specific design and inspection.
