ericbusboom/garage-renovation/studies/20260921.01-joist-hangers/joist-hanger-options.pdf

# EXPOSED LOFT FLOOR · JOIST / W-BEAM CONNECTION STUDY

Garage study · W12×16 concept · 2×8 joists at 16″ o.c. · preliminary architectural details

JH-001

21 SEPTEMBER 2026

DESIGN INTENT | quiet painted wood cells, dark steel lines, flush top plane, wiring and low-profile lights hidden above | NOT FOR CONSTRUCTION

## A FLUSH TUCKED JOIST — CLEANEST CUSTOM DETAIL

Joists stop at the web; paired joists align on opposite sides. The steel seat carries them. ≈ 5⁄16″ deep × 1⅞″ long

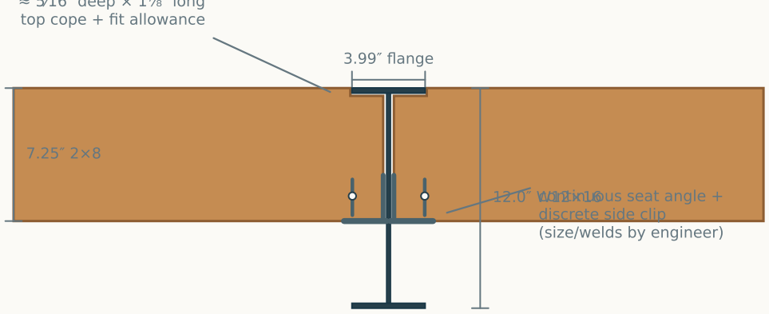
[picture p52: figure]
3.99″ flange; continuous seat angle + discrete side clip (size/welds by engineer); top cope + fit allowance

VISUAL RESULT: wood and steel share one crisp top plane; almost all hardware disappears in the W pocket.

Do not assume the cope provides bearing. Confirm end shear, seat, welds, web local strength, uplift and lateral restraint.

## B HIDDEN SERVICE FLOOR — LIGHTS + WIRING ABOVE THE CEILING

Your layered idea works best when the upper panel is the structural deck and the lower panel is the visible ceiling.

EMT | J

finish floor

23⁄32″ T&G structural deck

2×3 sleepers on edge
2½″ service cavity

½″ A-grade plywood
visible ceiling plane

low-profile light

Dedicated conduit lanes cross over the W-beam top flange in the same cavity. Keep junction boxes accessible through a removable light or perimeter access panel.

If floor height must stay minimal: flat 2×4 sleepers give only 1½″. Use EMT / engineered steel protection; ordinary cable cannot sit safely in the screw zone.

## C SHALLOW ARCH — MAKE THE SHAPE HONEST

The graceful version starts deeper; it does not carve capacity out of a 2×8 at midspan.

flat floor / ceiling panel above

GOOD CONCEPT

engineered 2×10 / LVL / glulam profile; smooth CNC curve; minimum depth preserved at center

DON'T: field-cut the tension edge of the already-sized 2×8. The maximum cut lands near maximum bending.

At the 125 psf storage reading the current 2×8 study is already at DCR 0.96—there is effectively no reserve for an arch cut.

## CONNECTION FAMILY — FROM QUIETEST TO MOST EXPRESSIVE

1

TUCKED + SEAT ANGLE
best fit for this frame

2

TOP-FLANGE HANGER
simplest listed hardware

3

CONCEALED KNIFE PLATE
premium; thicker timber

4

EXPOSED CLIP
celebrate the rhythm

Connection sizes, welds, fasteners, fire protection, diaphragm and electrical routing require project-specific engineering and permitting.
