ericbusboom/garage-renovation/report/03-land-use-and-permitting/README.md

# 03 — Land Use and Permitting

This section establishes the legal building envelope and approval path. Verify the parcel, base zone, community plan, overlays, coastal status, setbacks, height, structure separation, floor area, lot coverage, parking, legal use, fire separation, and permit history from current official records.

The standard alley calculation suggests five feet on-site, subject to surveyed boundaries, overlays and the applicable approval route. The preliminary upper interior-side setback is four feet; the proposed roof over the retained lower garage strip requires a written interpretation.

## Current chapter report

- [LAND-005 — Setbacks, retained garage, and proposed storage roof](setbacks-and-roof-findings.md), revision 0, 2026-09-15, status `draft`. Includes research sources, conditional pitch calculations and questions for City review.
- [LAND-006 — Extending the garage along the existing 1-ft side setback](setback-extension-research.md), revision 0, 2026-09-20, status `draft`. Two code routes (SDMC 131.0461(a)(12) by right; 127.0106(b) Neighborhood Development Permit), both single-story only within the setback; permit and plan lookup tools; precedent search.
- Owner intent: upstairs storage; existing walls remain exterior; new posts stand over open walkways. Legal occupancy and permit classification remain open.

## Required outputs

- parcel/zoning/overlay report
- setback, height, FAR, lot-coverage, and fire-separation analysis
- coastal-development-permit determination
- permit and agency matrix
- permit-history/legal-status record
- written agency interpretations and meeting notes
