ericbusboom/garage-renovation/render/20260908.02-backyard-existing/README.md

# Backyard — Blender rendering package

This package builds the **existing** backyard from corrected site revision 8, using six materials extracted from the owner's photographs. It is separate from `blender-render/garage-site.blend`, which used the proposed garage.

## Main outputs

- `backyard-existing.blend` — native Blender scene with packed textures, named collections and four cameras.
- `01-backyard-overview.png` — whole-yard view.
- `02-patio-toward-garage.png` — view toward the garage from the patio.
- `03-conversation-area.png` — fire pit and seating.
- `04-house-and-gardens.png` — house-facing context.
- `Backyard-Existing-Conditions.pdf` — formal illustrated record of the model basis and limitations.
- `BACKYARD-EXISTING-CONDITIONS.md` — editable written record.
- `textures/` — original surface crops, repeating color atlases, approximate bump/roughness maps, and crop manifest.
- `site-scene.json` — frozen geometry input from site revision 8.
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
