ericbusboom/garage-renovation/data/images/rivera-north-main-2554.jpg

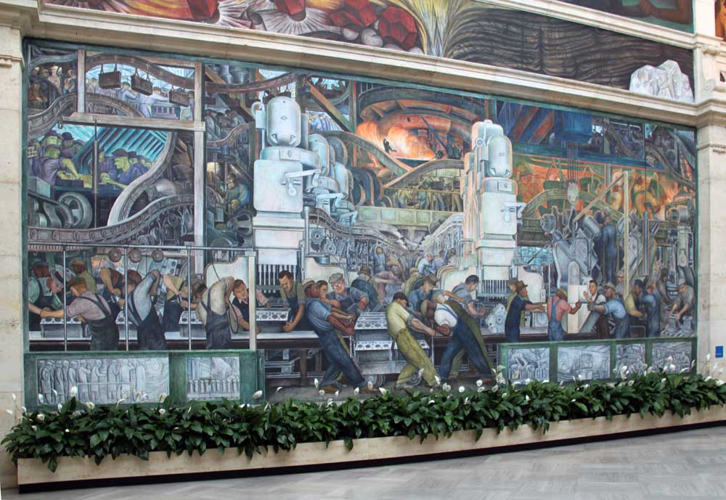
data/images/rivera-north-main-2554.jpg
