ericbusboom/garage-renovation/data/images/rivera-north-main-scene.jpg

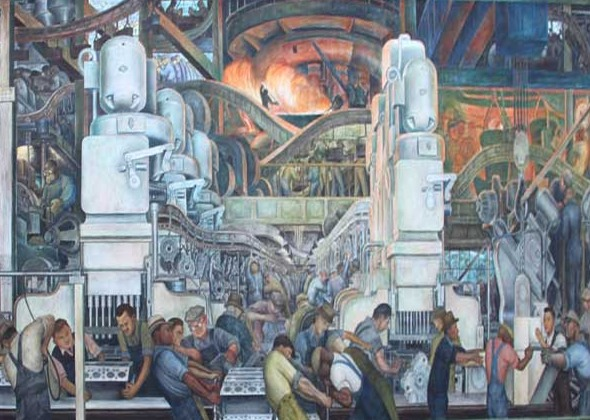
data/images/rivera-north-main-scene.jpg
