ericbusboom/garage-renovation/public/01-exposed-steel-southwest.png

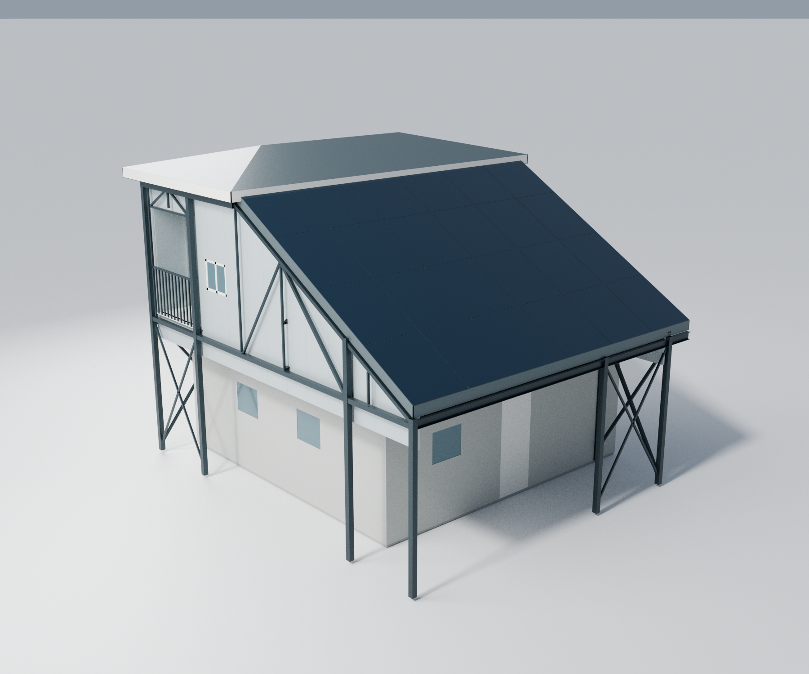
public/01-exposed-steel-southwest.png
