ericbusboom/garage-renovation/public/01-proposed-backyard-overview.png

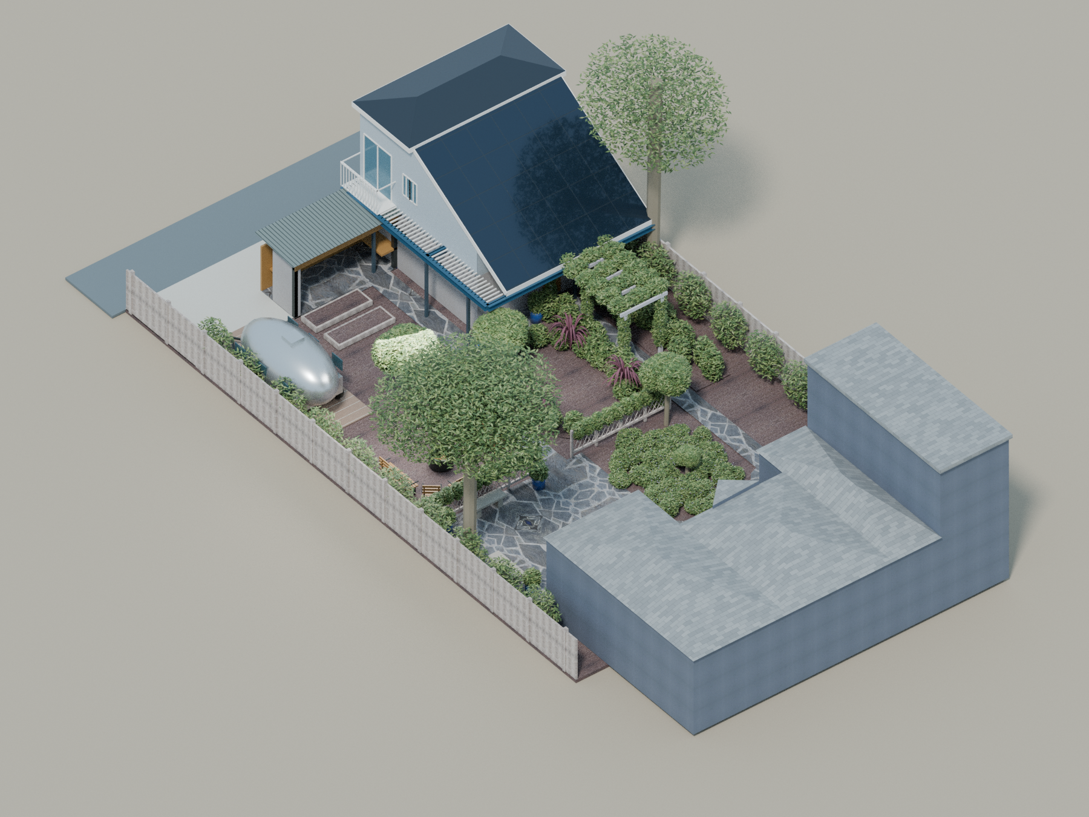
public/01-proposed-backyard-overview.png
