ericbusboom/garage-renovation/public/02-exposed-steel-northwest.png

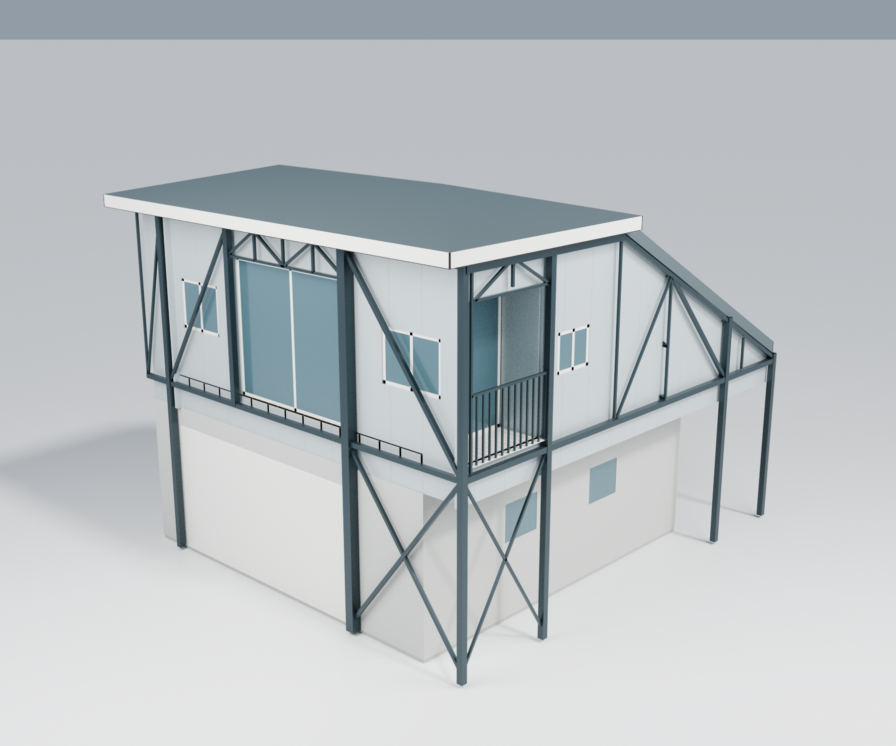
public/02-exposed-steel-northwest.png
