ericbusboom/garage-renovation/public/02-proposed-patio-to-garage.png

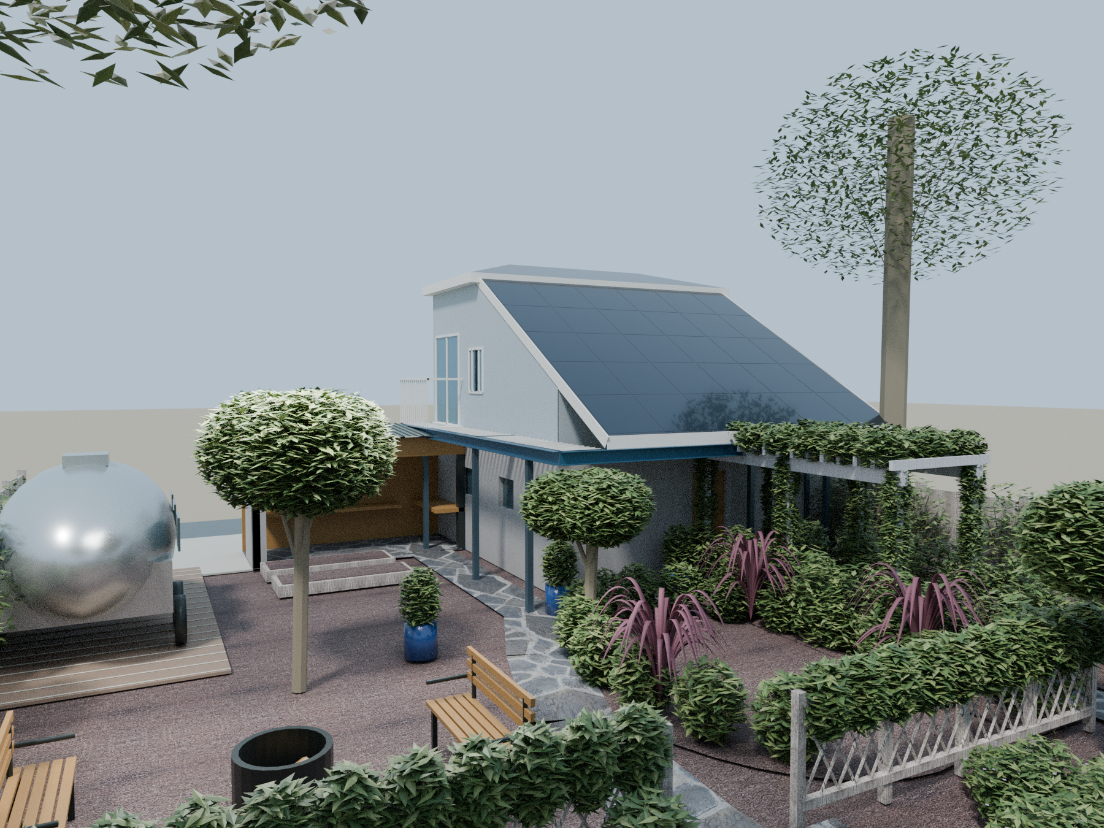
public/02-proposed-patio-to-garage.png
