ericbusboom/garage-renovation/public/03-proposed-garage-context.png

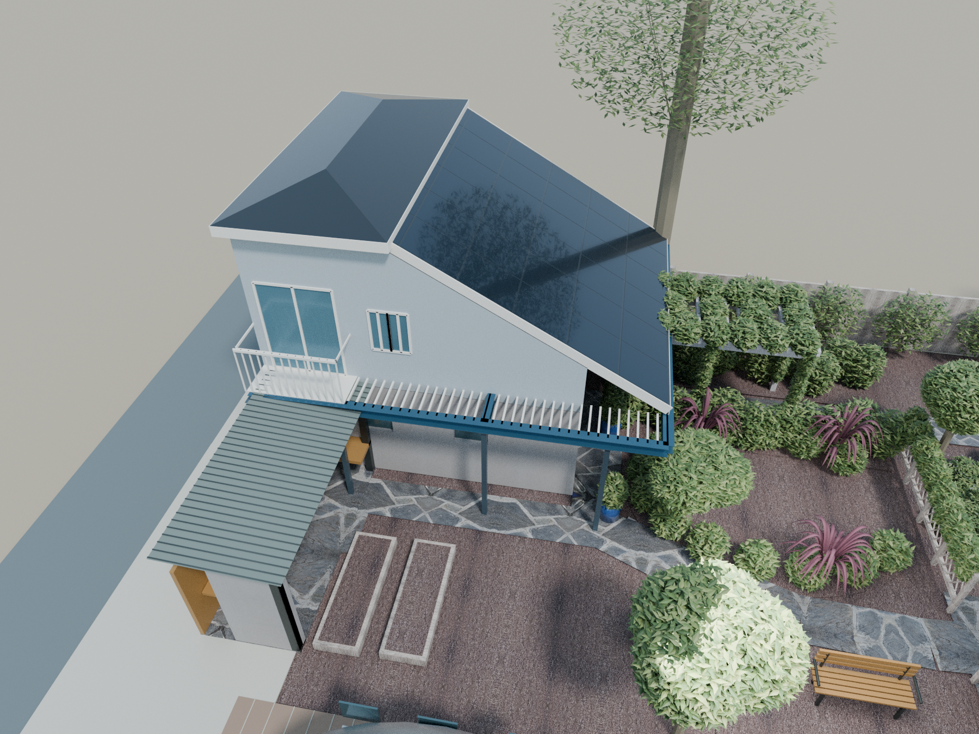
public/03-proposed-garage-context.png
