ericbusboom/garage-renovation/public/reaction-plan.png

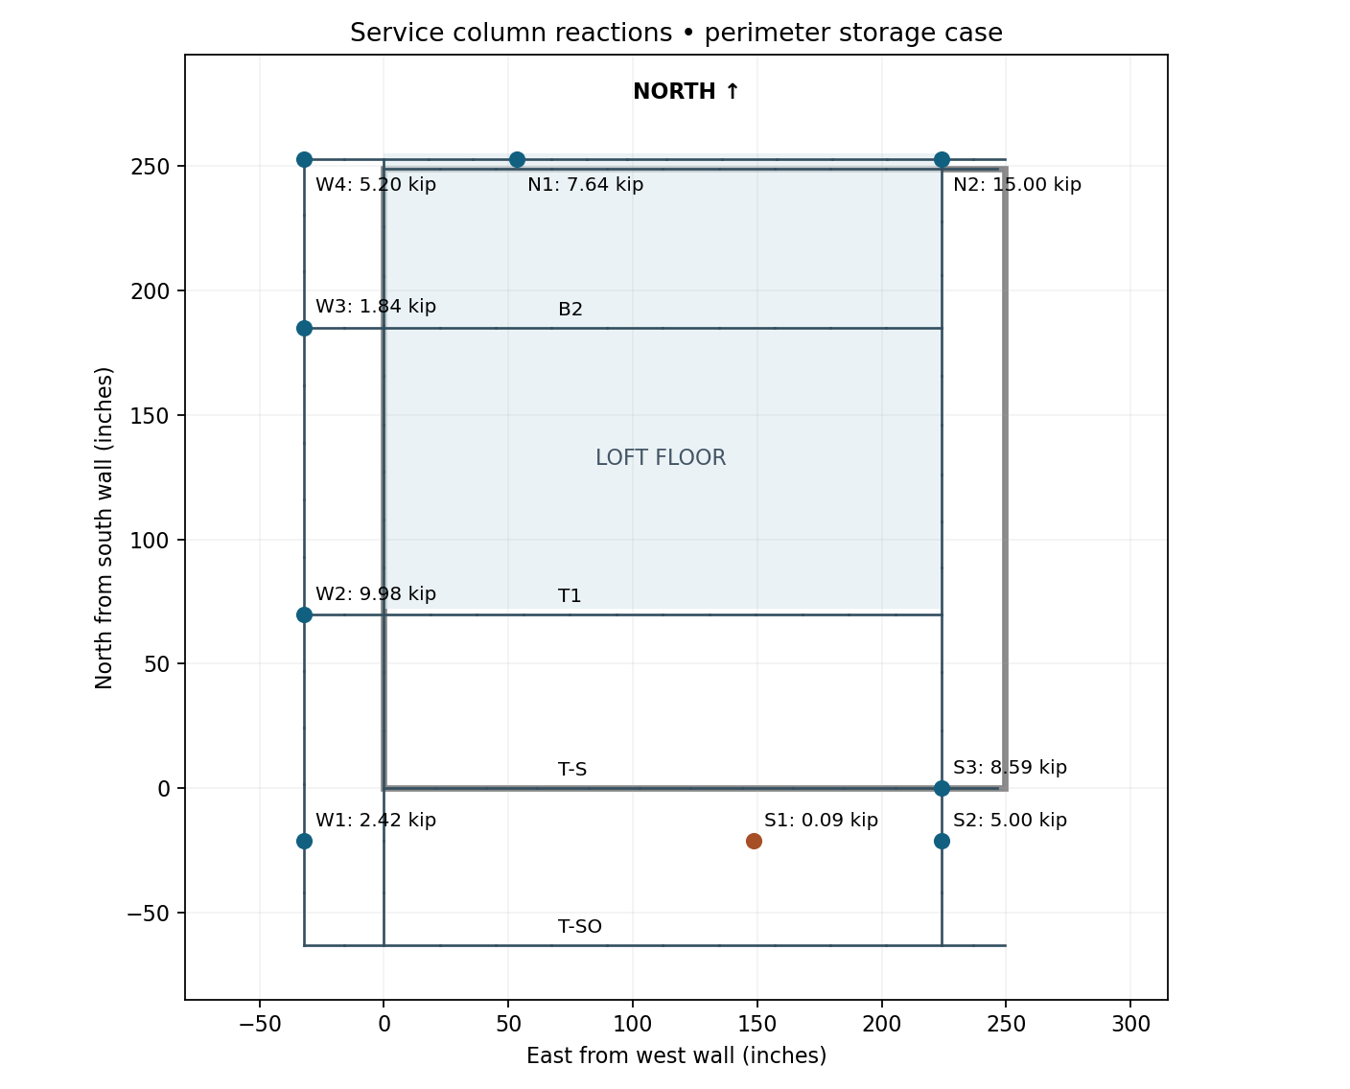
public/reaction-plan.png
