ericbusboom/garage-renovation/public/section-and-plan.png

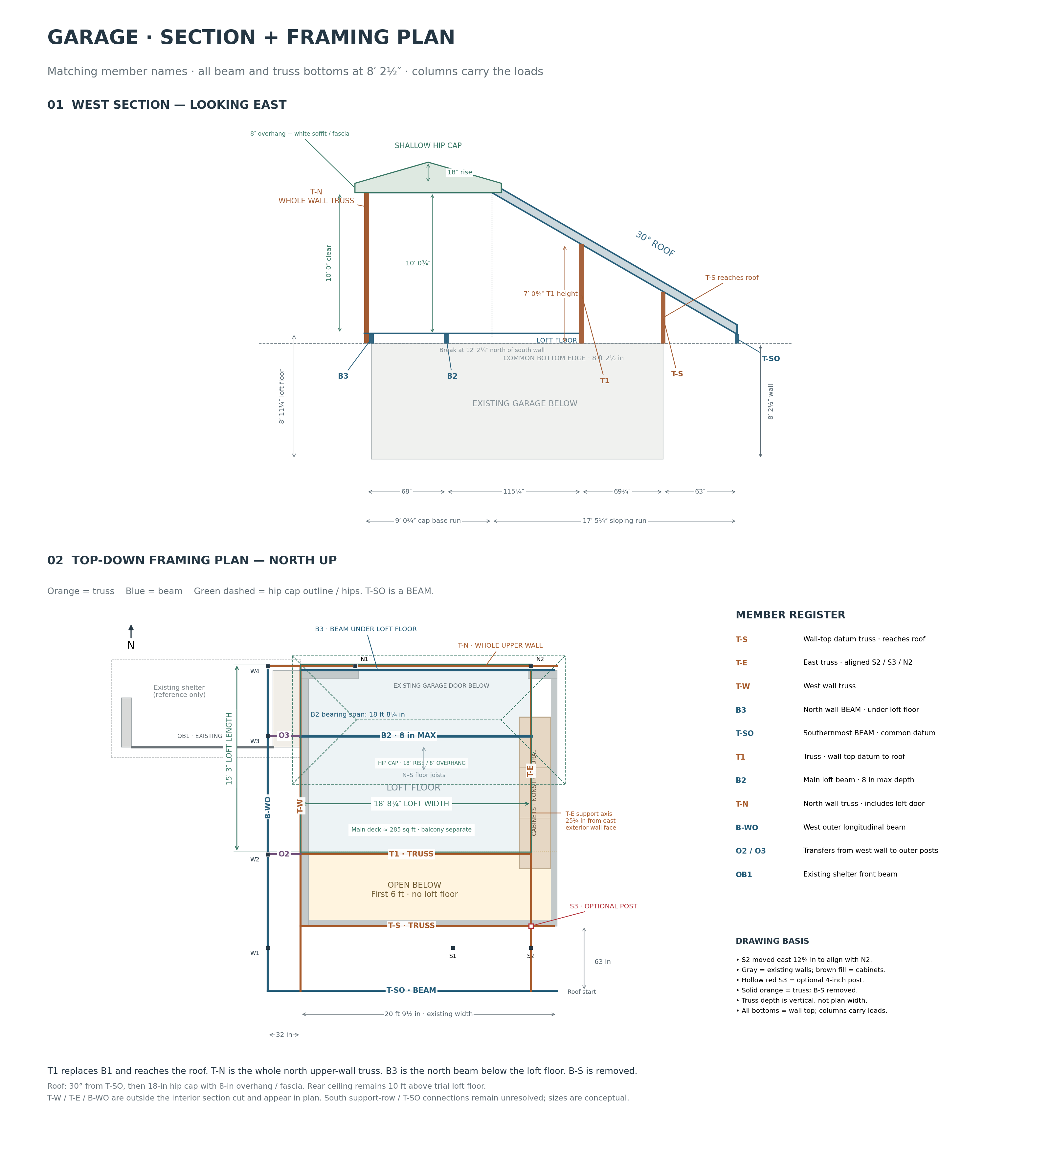
public/section-and-plan.png
