ericbusboom/garage-renovation/public/T1-truss-elevation.png

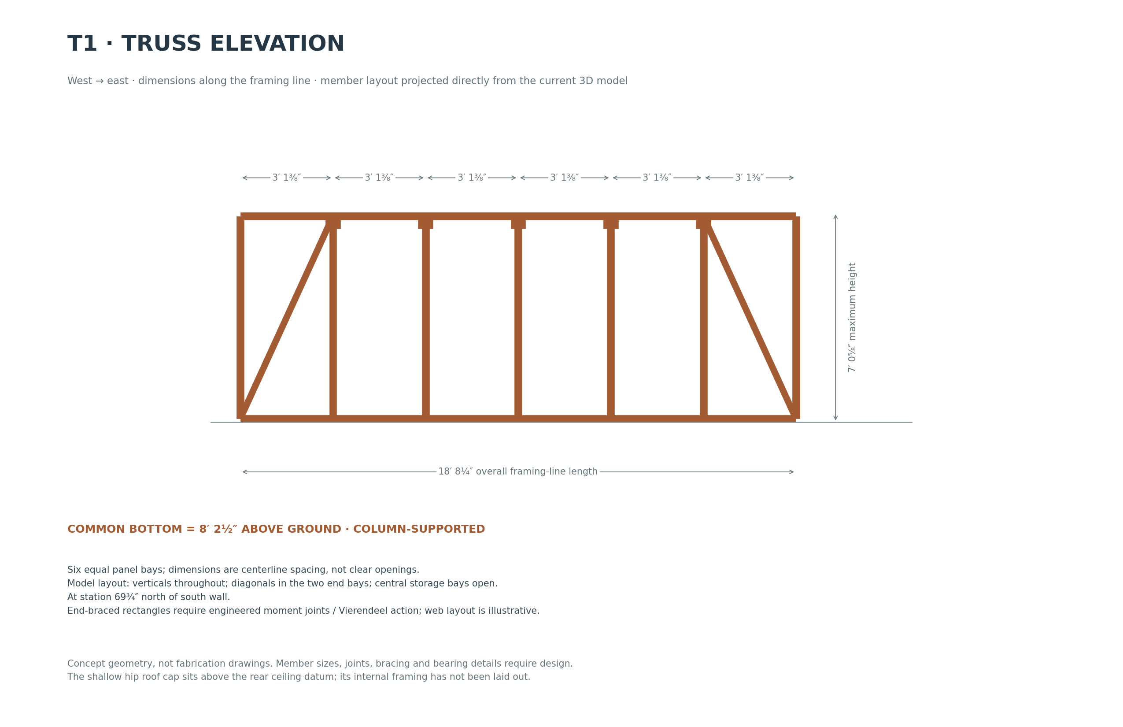
public/T1-truss-elevation.png
