ericbusboom/garage-renovation/public/T-E-truss-elevation.png

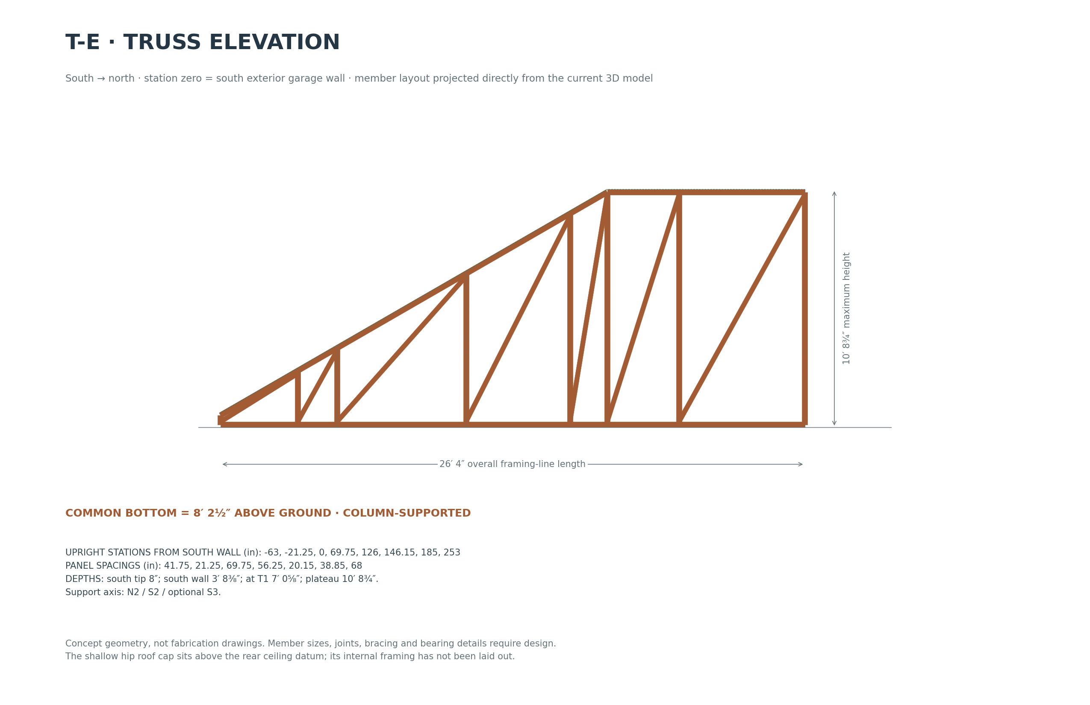
public/T-E-truss-elevation.png
