ericbusboom/garage-renovation/public/T-N-truss-elevation.png

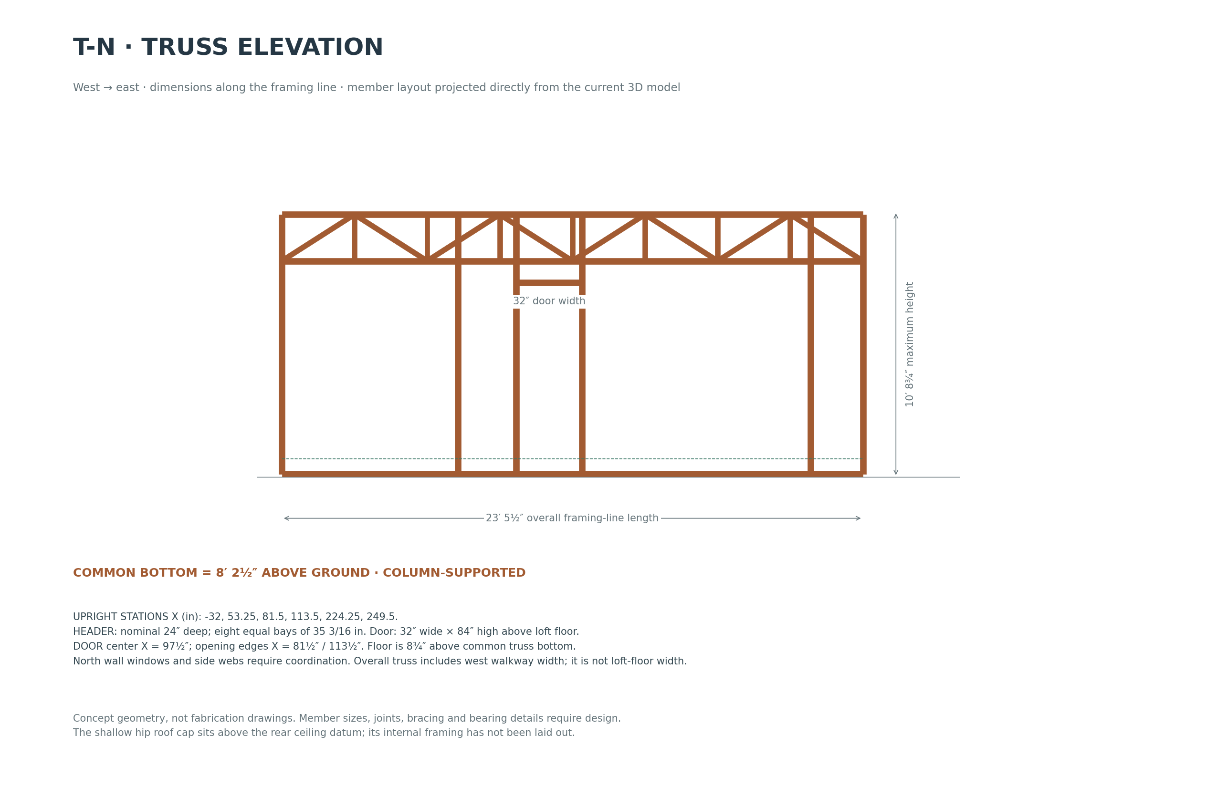
public/T-N-truss-elevation.png
