ericbusboom/garage-renovation/public/T-S-truss-elevation.png

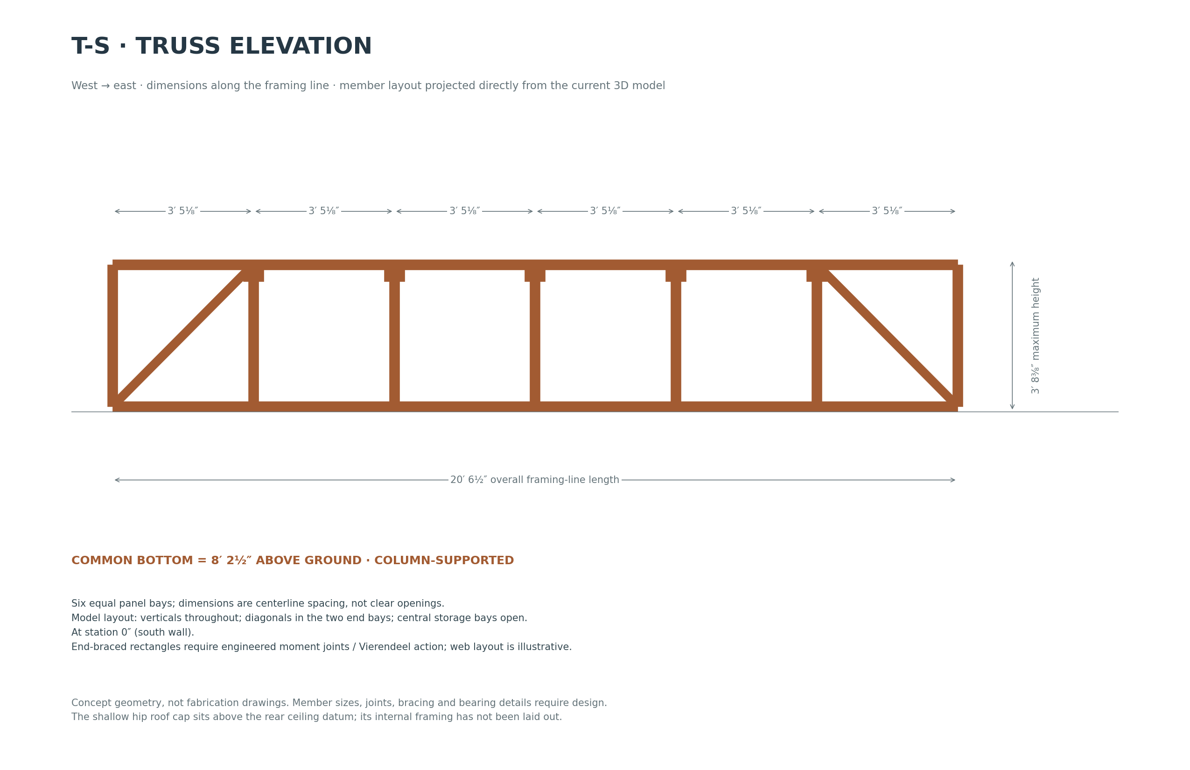
public/T-S-truss-elevation.png
