ericbusboom/garage-renovation/public/T-W-truss-elevation.png

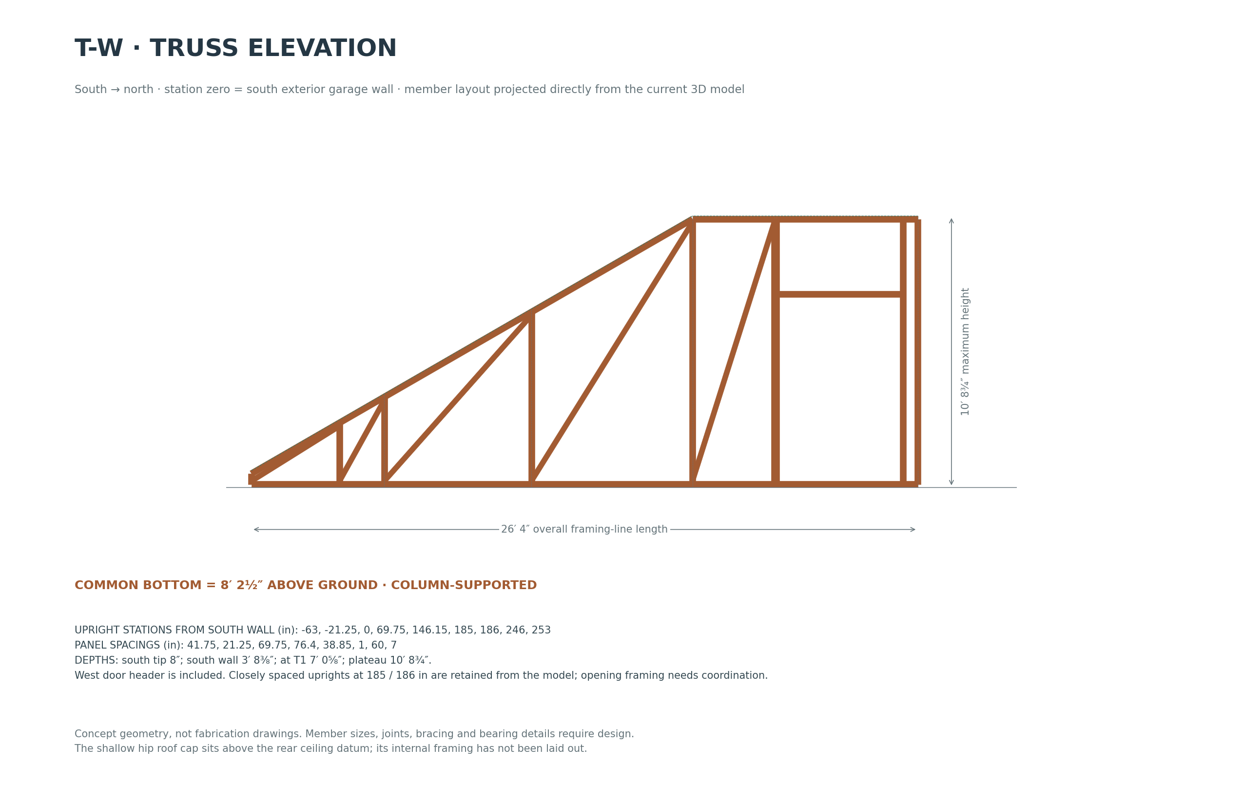
public/T-W-truss-elevation.png
