ericbusboom/garage-renovation/render/20260907.01-site-concepts/flat-cap-balcony-entry-v2.png

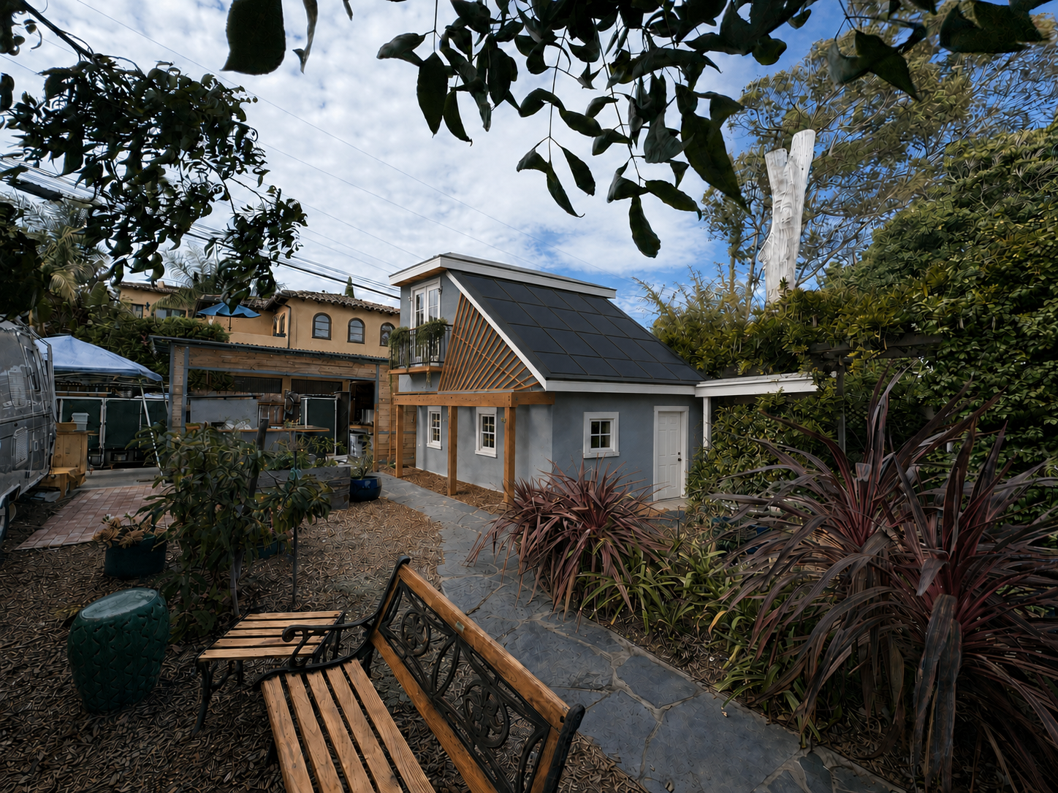
render/20260907.01-site-concepts/flat-cap-balcony-entry-v2.png
