ericbusboom/garage-renovation/render/20260907.01-site-concepts/option-b-garden.png

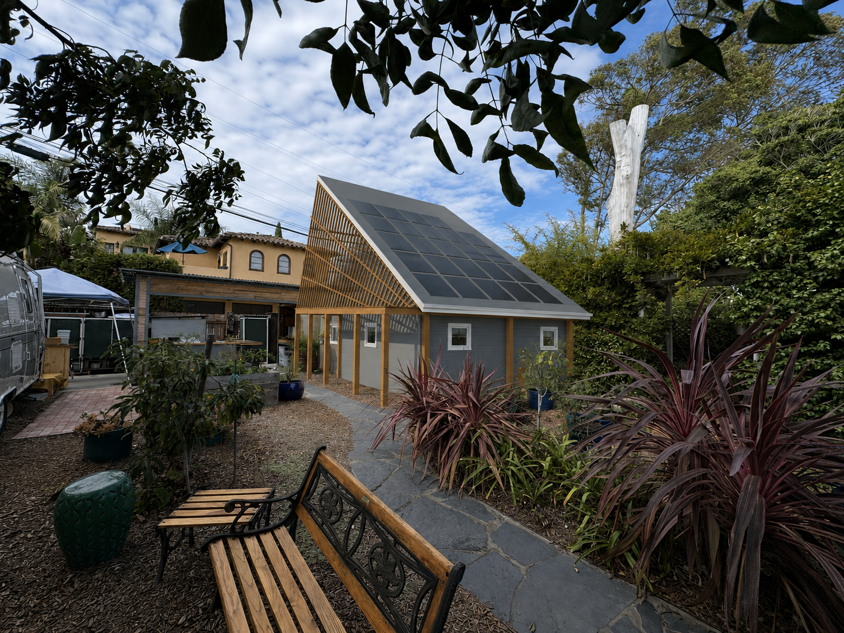
render/20260907.01-site-concepts/option-b-garden.png
