ericbusboom/garage-renovation/render/20260907.01-site-concepts/references/IMG_4202.jpg

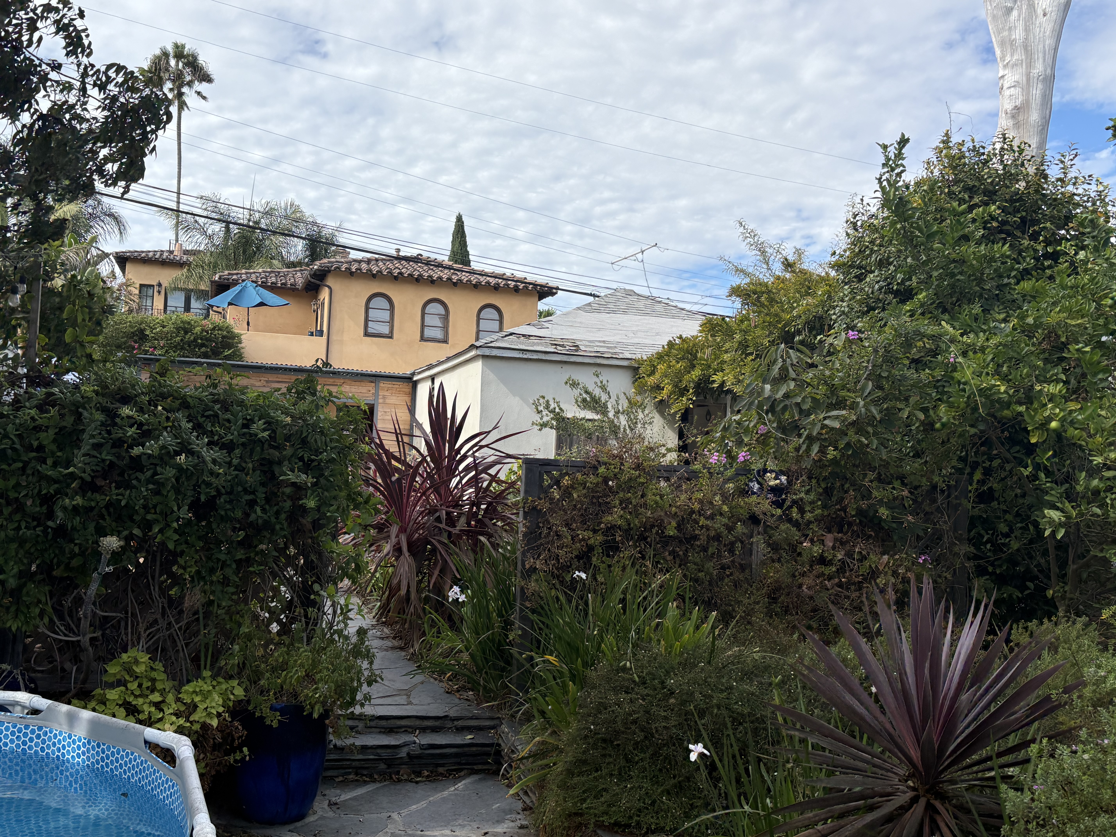
render/20260907.01-site-concepts/references/IMG_4202.jpg
