ericbusboom/garage-renovation/render/20260907.02-garage-model/01-southwest-exterior.png

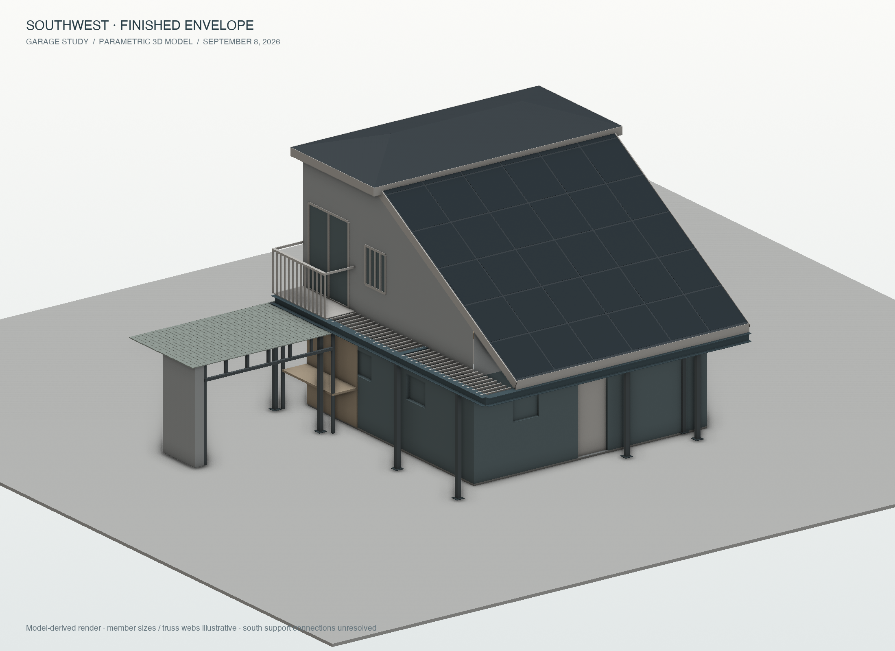
render/20260907.02-garage-model/01-southwest-exterior.png
