ericbusboom/garage-renovation/render/20260907.02-garage-model/02-southwest-structure.png

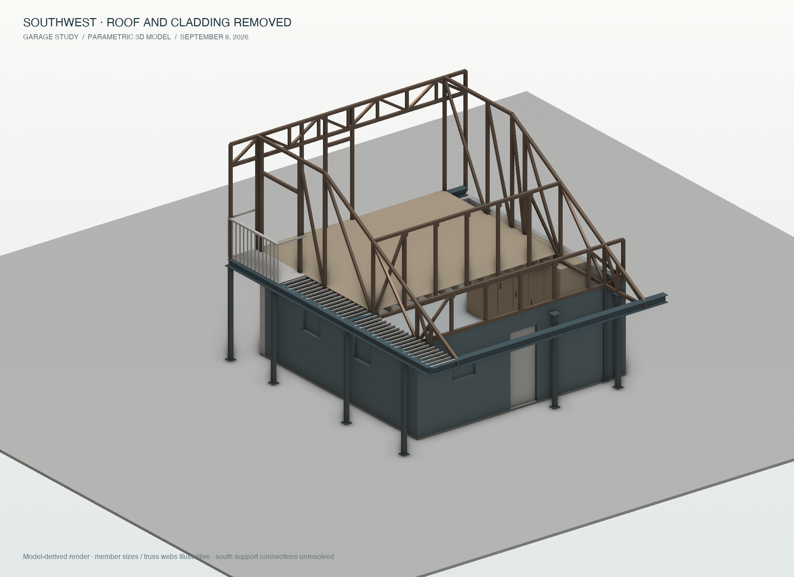
render/20260907.02-garage-model/02-southwest-structure.png
