ericbusboom/garage-renovation/render/20260907.02-garage-model/03-northwest-structure.png

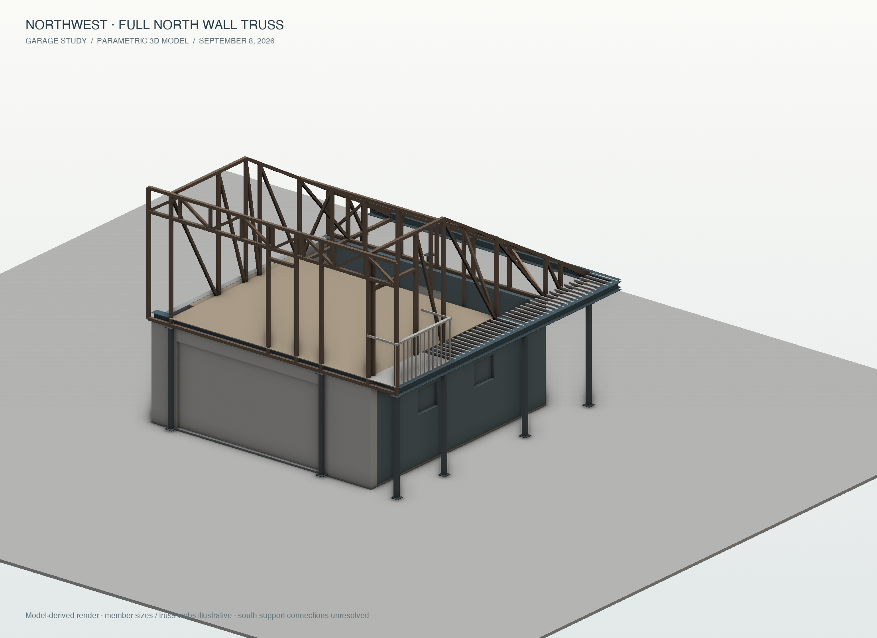
render/20260907.02-garage-model/03-northwest-structure.png
