ericbusboom/garage-renovation/render/20260907.02-garage-model/04-northwest-exterior.png

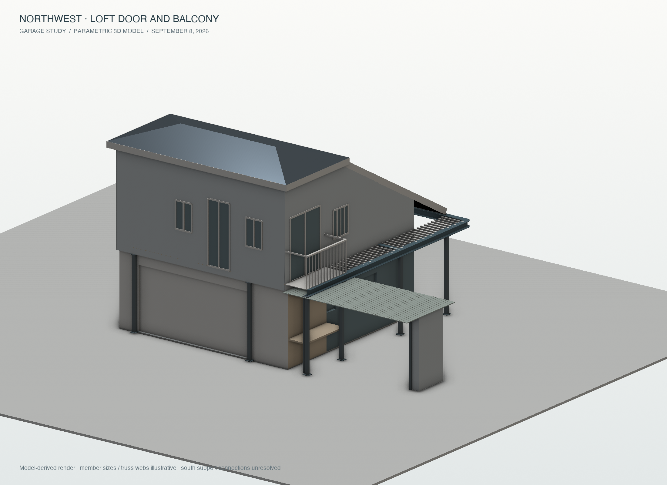
render/20260907.02-garage-model/04-northwest-exterior.png
