ericbusboom/garage-renovation/render/20260907.02-garage-model/garage-render-package/drawings/labeled-framing-plan.png

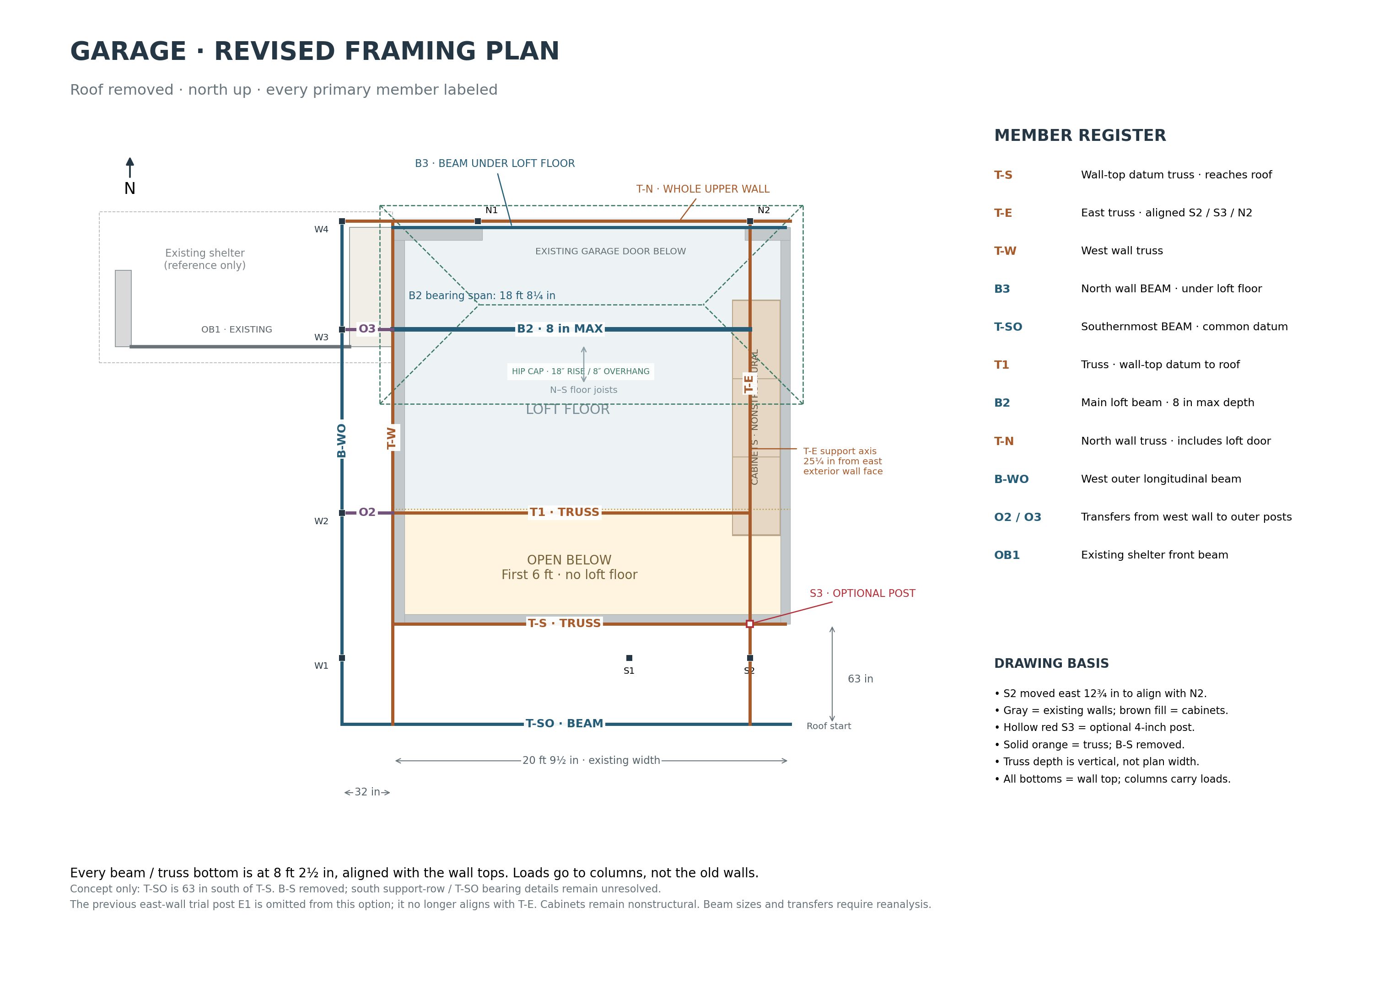
render/20260907.02-garage-model/garage-render-package/drawings/labeled-framing-plan.png
