ericbusboom/garage-renovation/render/20260907.02-garage-model/garage-render-package/drawings/T1-dimensioned.png

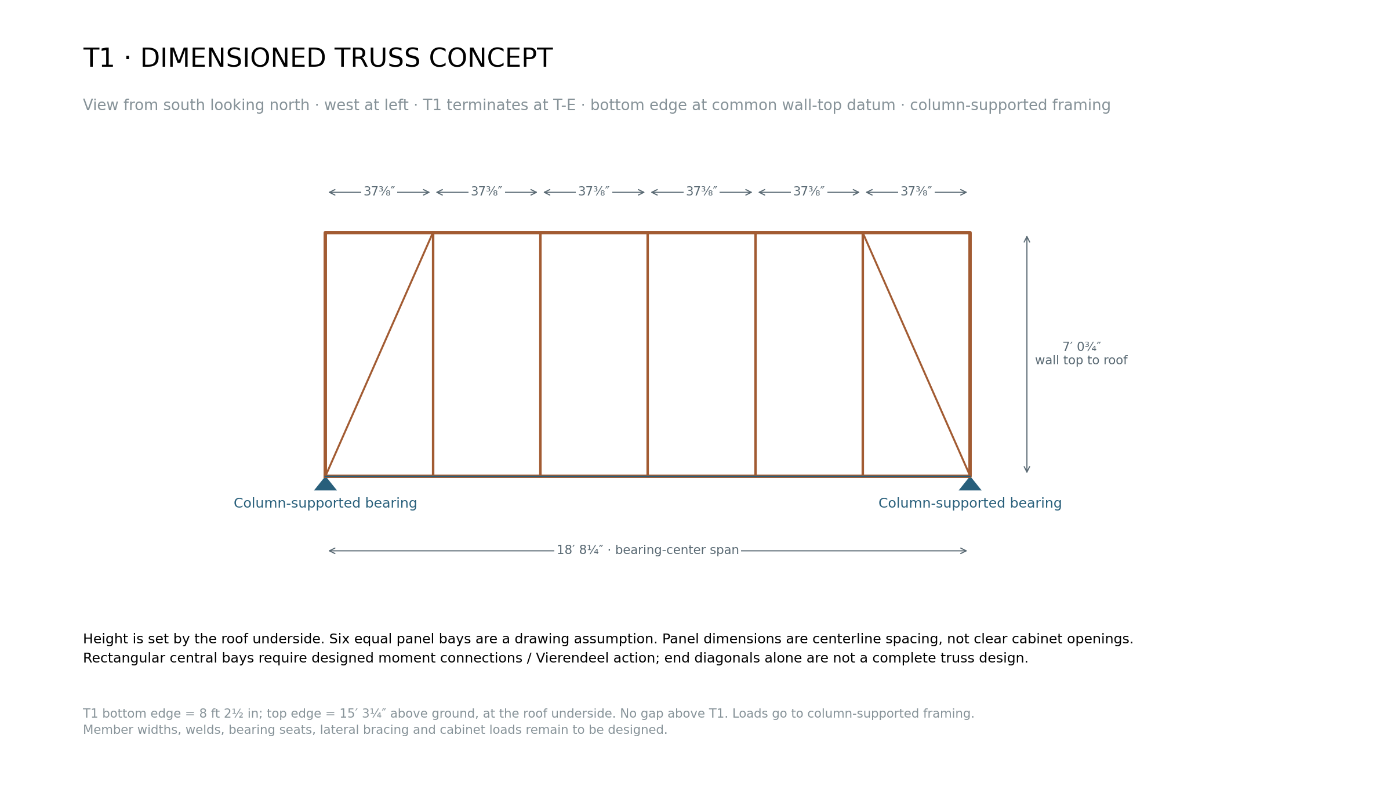
render/20260907.02-garage-model/garage-render-package/drawings/T1-dimensioned.png
