ericbusboom/garage-renovation/render/20260907.02-garage-model/garage-render-package/drawings/TN-dimensioned.png

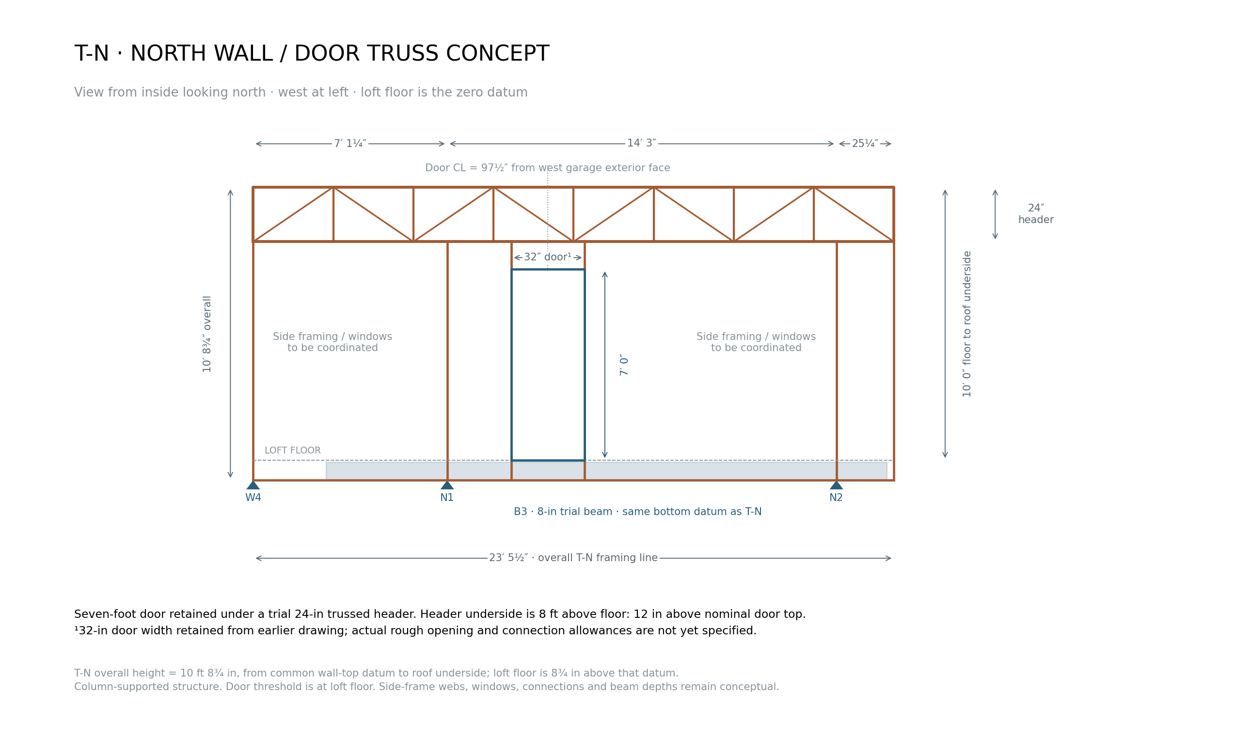
render/20260907.02-garage-model/garage-render-package/drawings/TN-dimensioned.png
