ericbusboom/garage-renovation/render/20260907.02-garage-model/garage-render-package/drawings/west-roof-section.png

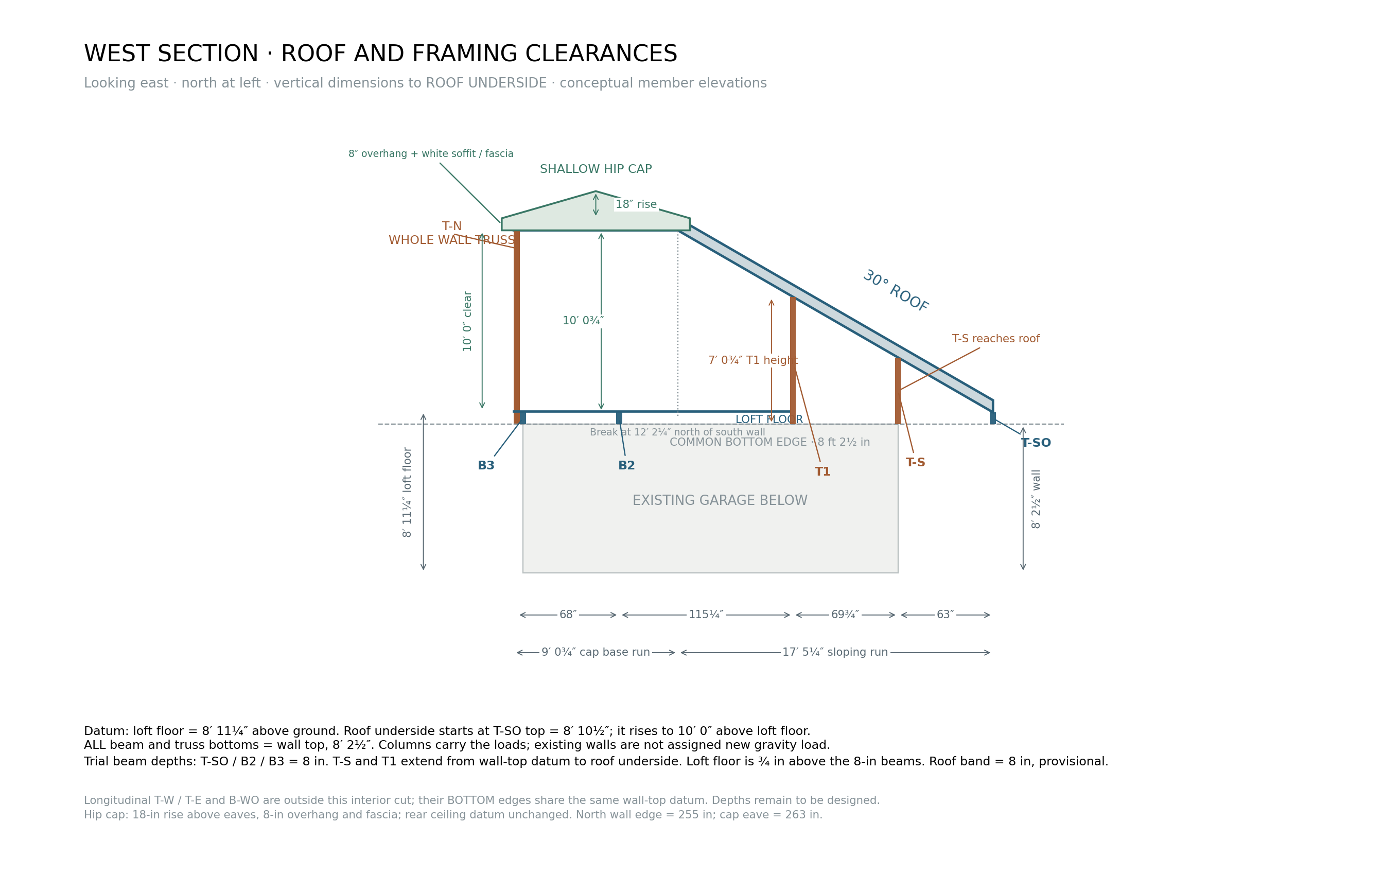
render/20260907.02-garage-model/garage-render-package/drawings/west-roof-section.png
