ericbusboom/garage-renovation/render/20260907.02-garage-model/garage-render-package/site-garden.png

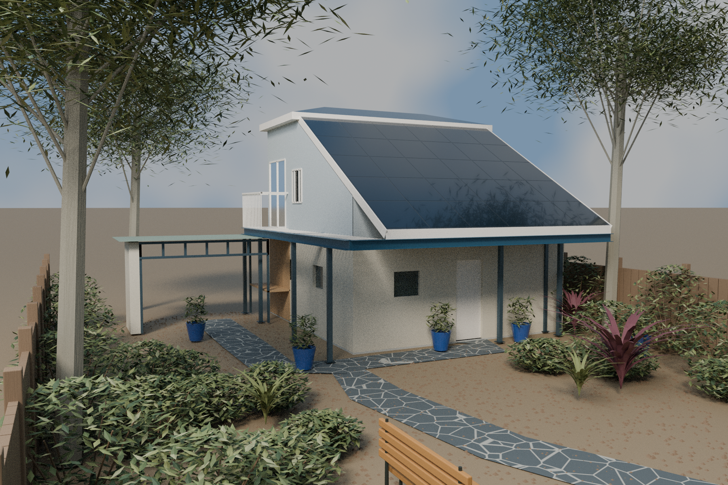
render/20260907.02-garage-model/garage-render-package/site-garden.png
