ericbusboom/garage-renovation/render/20260908.01-existing-site/house-and-pergola.png

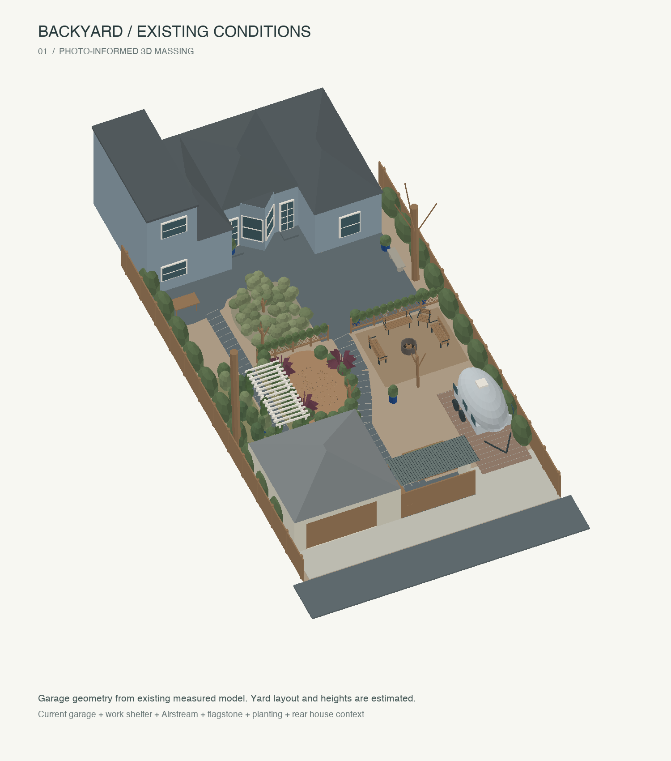
render/20260908.01-existing-site/house-and-pergola.png
