ericbusboom/garage-renovation/render/20260908.01-existing-site/references/areas/contact.jpg

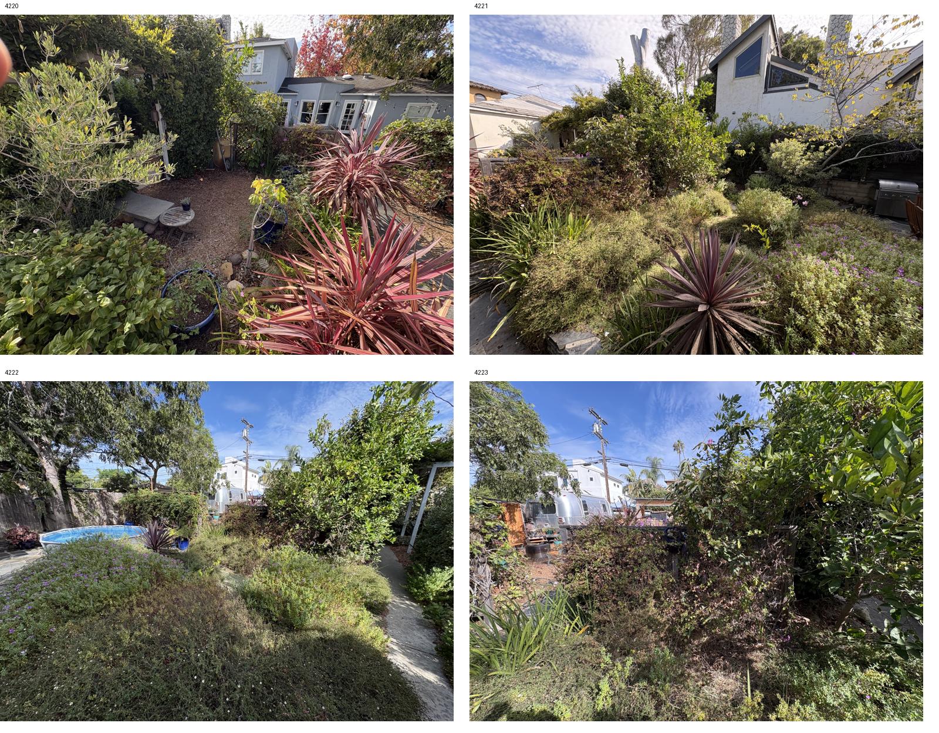
render/20260908.01-existing-site/references/areas/contact.jpg
