ericbusboom/garage-renovation/render/20260908.01-existing-site/references/IMG_4201-video.jpg

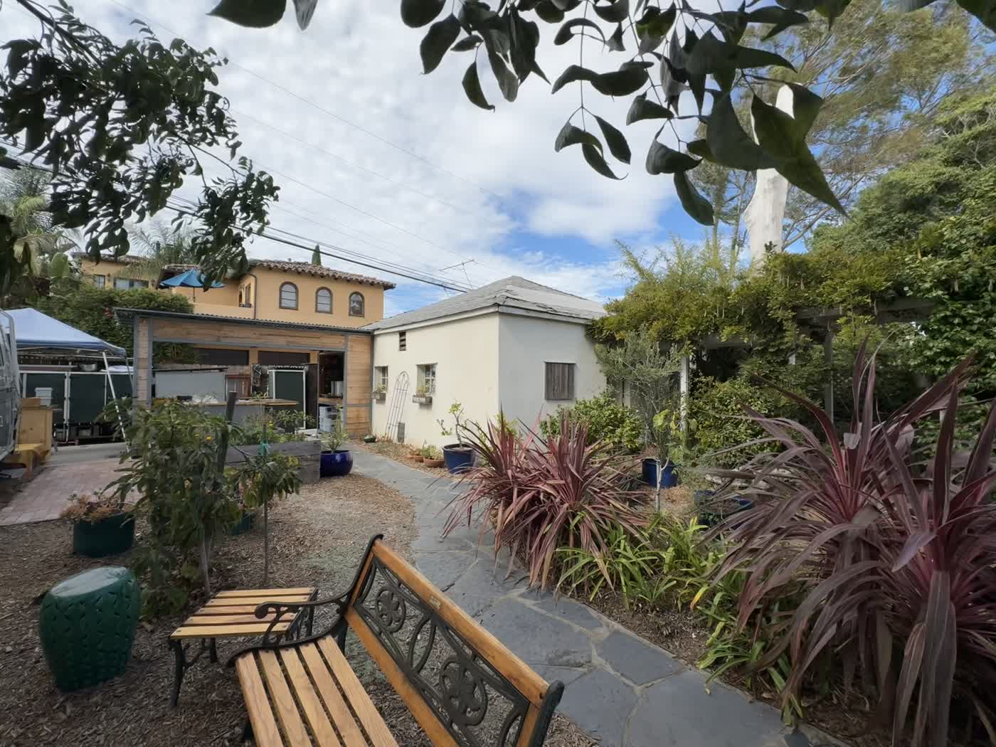
render/20260908.01-existing-site/references/IMG_4201-video.jpg
