ericbusboom/garage-renovation/render/20260908.01-existing-site/references/new/contact.jpg

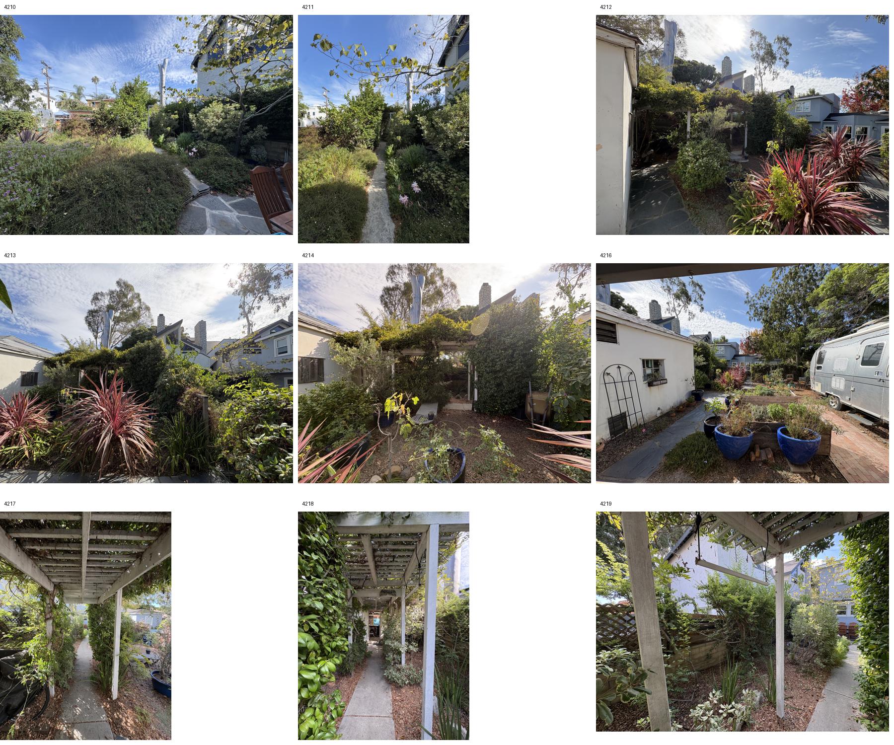
render/20260908.01-existing-site/references/new/contact.jpg
