ericbusboom/garage-renovation/render/20260908.01-existing-site/references/patio/contact.jpg

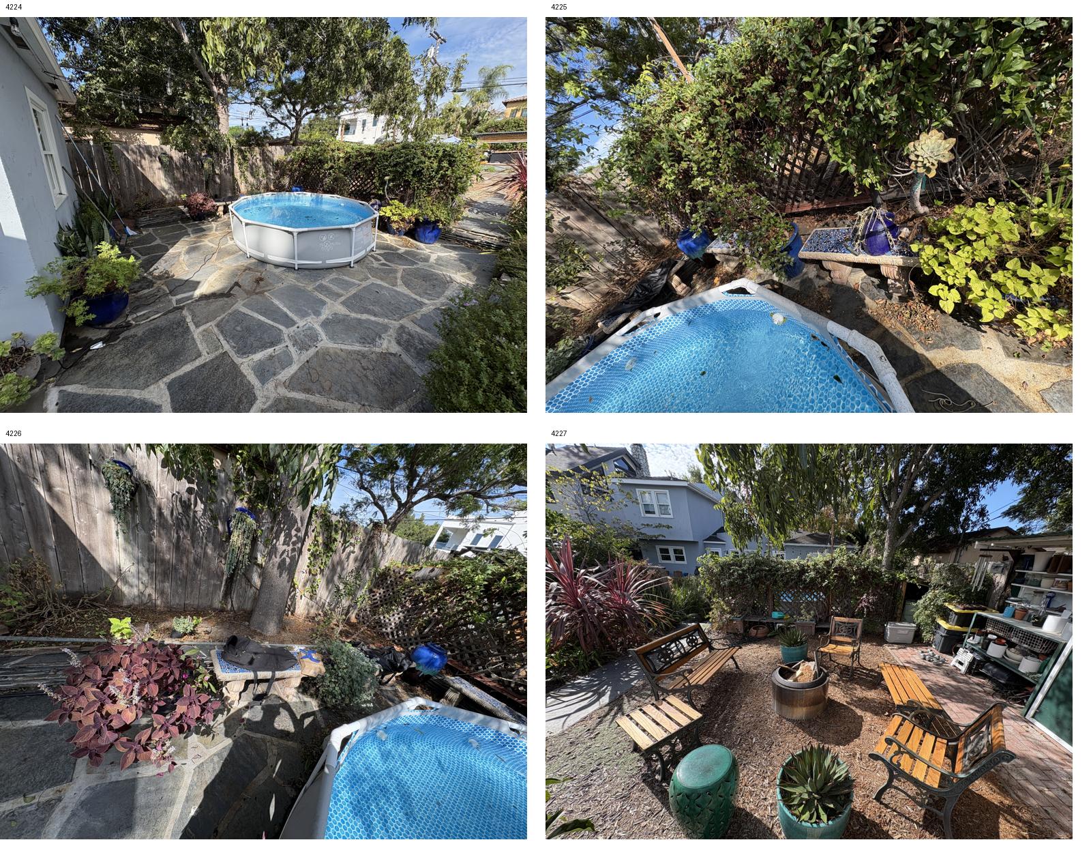
render/20260908.01-existing-site/references/patio/contact.jpg
