ericbusboom/garage-renovation/render/20260908.01-existing-site/site-overview.png

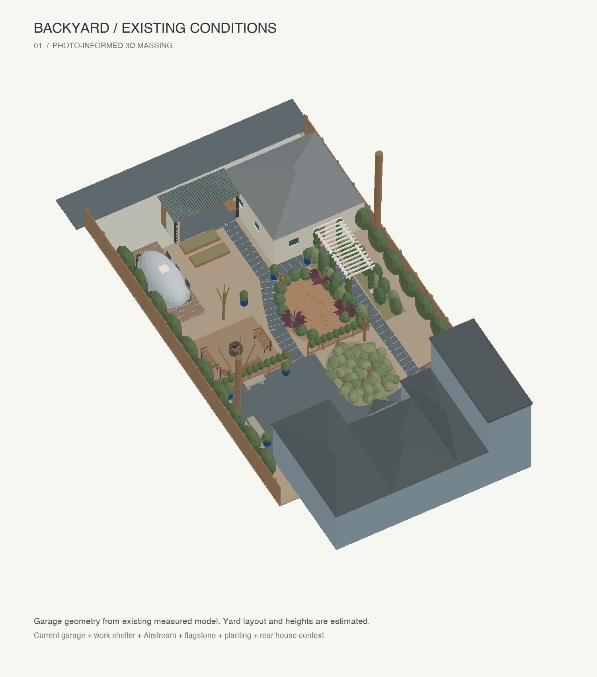
render/20260908.01-existing-site/site-overview.png
