ericbusboom/garage-renovation/render/20260908.01-existing-site/site-plan.png

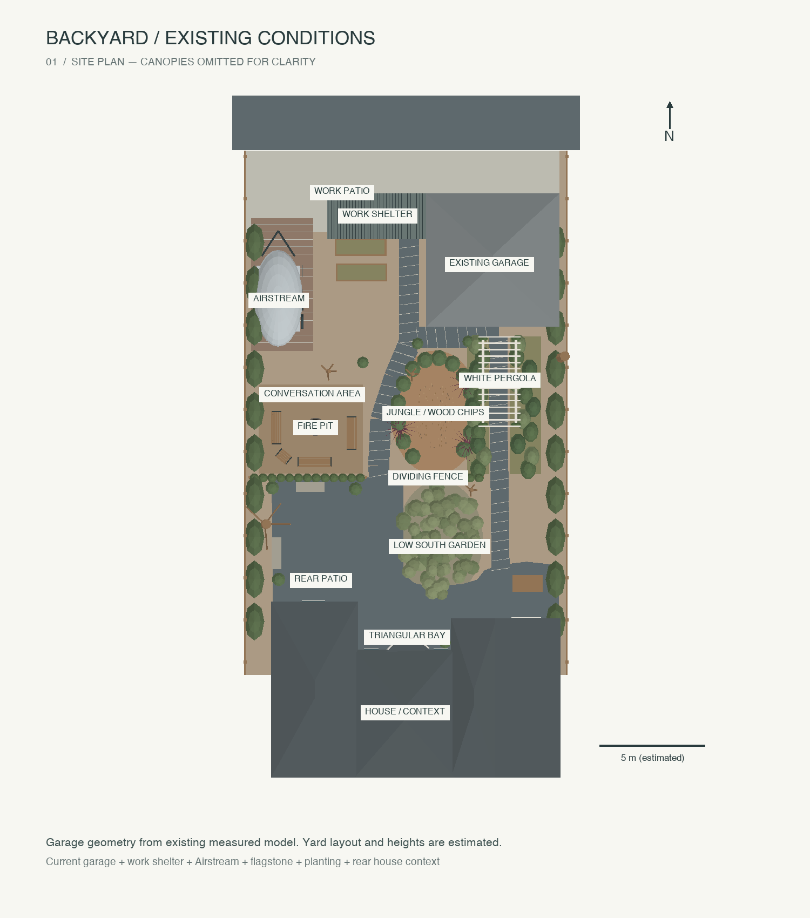
render/20260908.01-existing-site/site-plan.png
