ericbusboom/garage-renovation/render/20260908.01-existing-site/site-with-trees.png

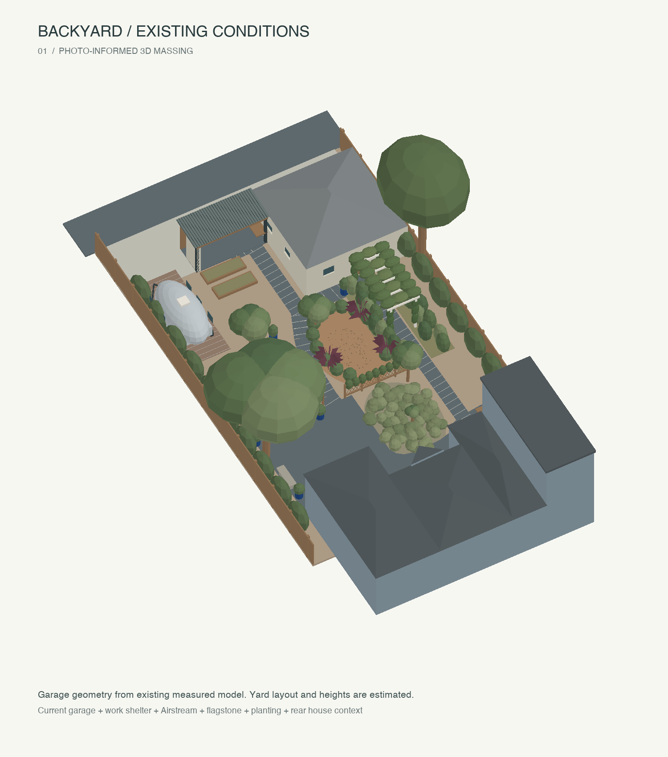
render/20260908.01-existing-site/site-with-trees.png
