ericbusboom/garage-renovation/render/20260908.02-backyard-existing/01-backyard-overview.png

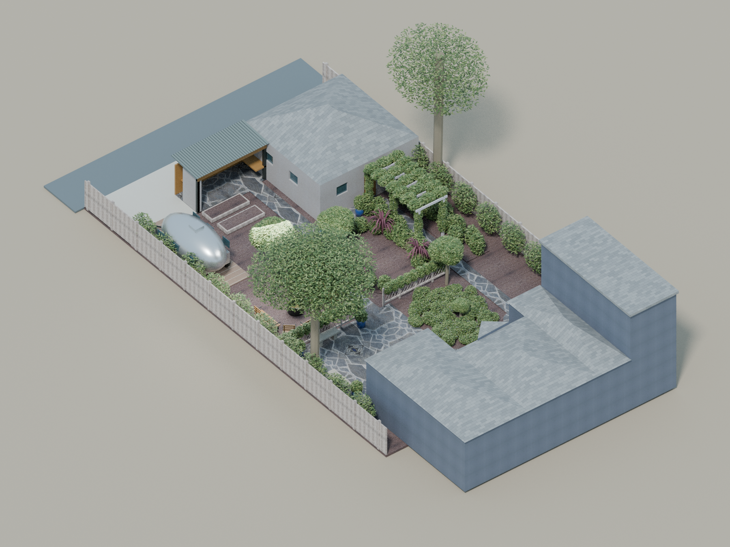
render/20260908.02-backyard-existing/01-backyard-overview.png
