ericbusboom/garage-renovation/render/20260908.02-backyard-existing/02-patio-toward-garage.png

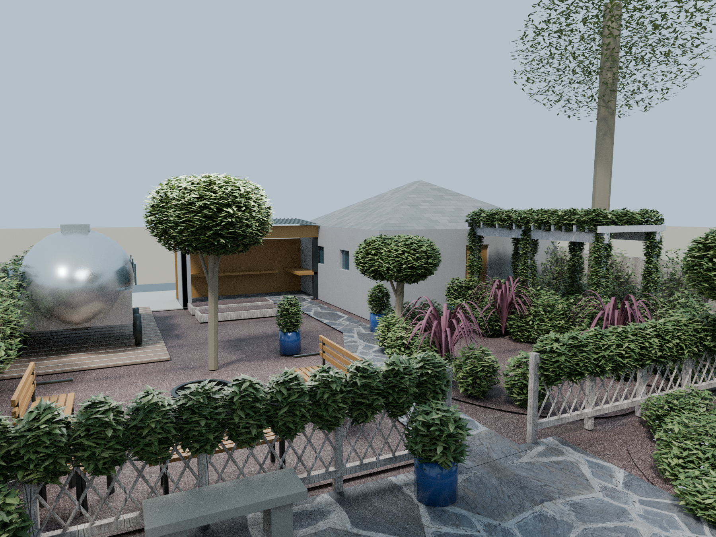
render/20260908.02-backyard-existing/02-patio-toward-garage.png
