ericbusboom/garage-renovation/render/20260908.02-backyard-existing/03-conversation-area.png

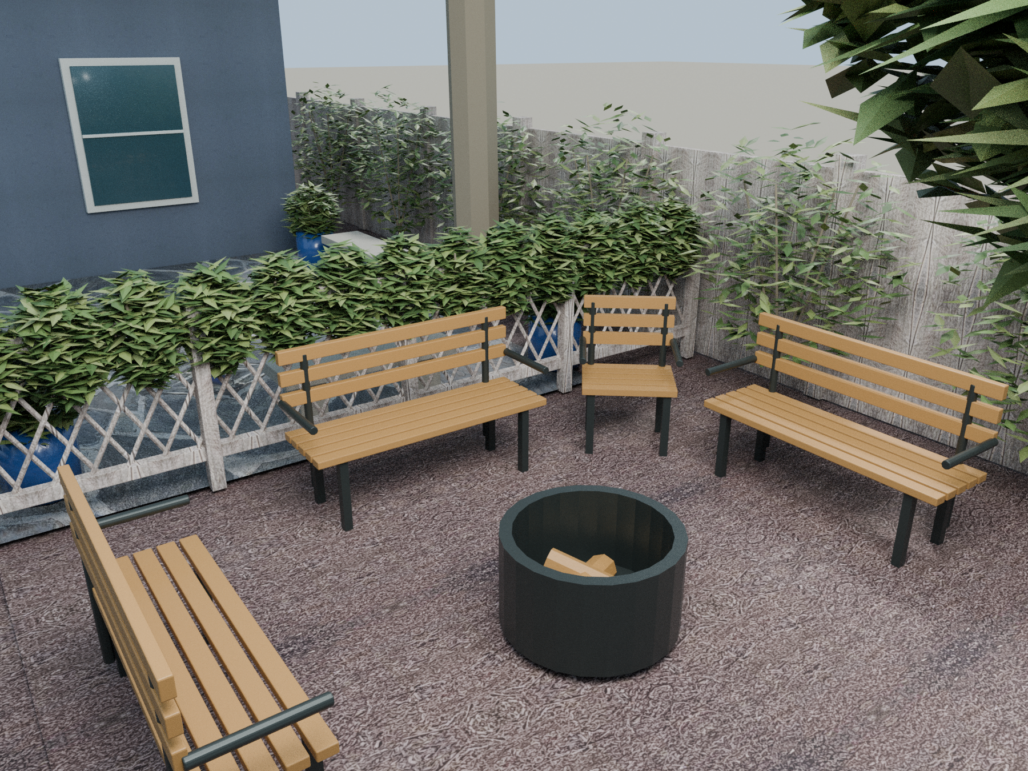
render/20260908.02-backyard-existing/03-conversation-area.png
