ericbusboom/garage-renovation/render/20260908.02-backyard-existing/04-house-and-gardens.png

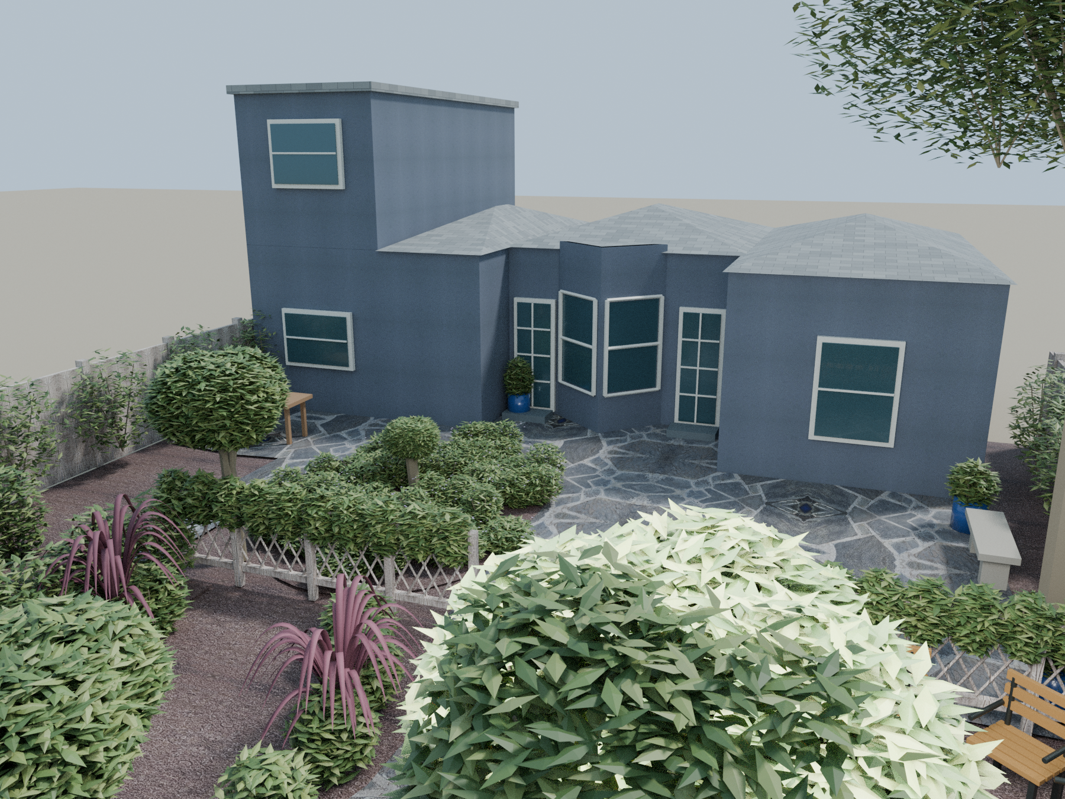
render/20260908.02-backyard-existing/04-house-and-gardens.png
