ericbusboom/garage-renovation/render/20260908.02-backyard-existing/texture-sources.jpg

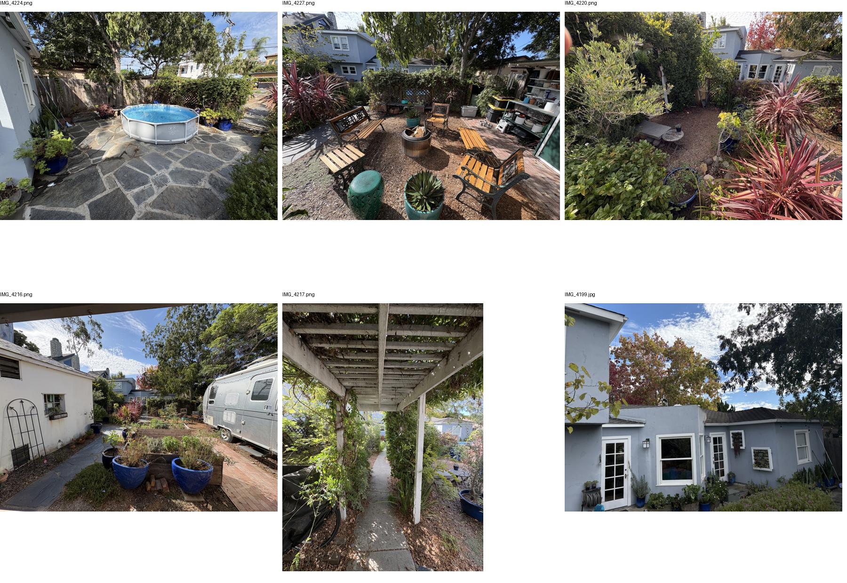
render/20260908.02-backyard-existing/texture-sources.jpg
