ericbusboom/garage-renovation/render/20260908.02-backyard-existing/textures/flagstone_bump.png

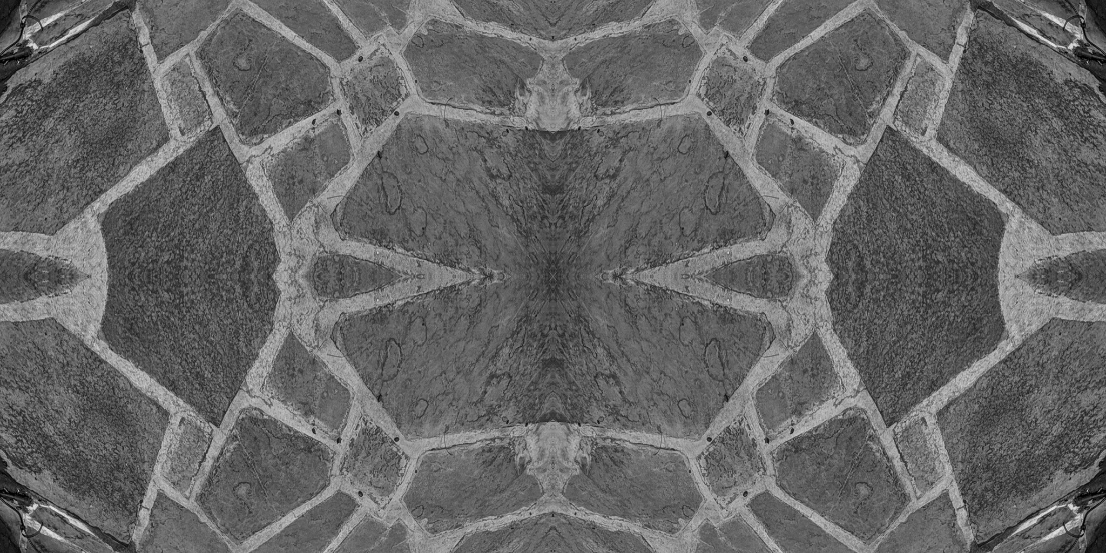
render/20260908.02-backyard-existing/textures/flagstone_bump.png
