ericbusboom/garage-renovation/render/20260908.02-backyard-existing/textures/house_stucco_source.png

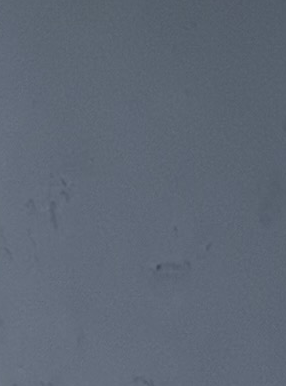
render/20260908.02-backyard-existing/textures/house_stucco_source.png
