ericbusboom/garage-renovation/render/20260908.02-backyard-existing/textures/painted_timber_bump.png

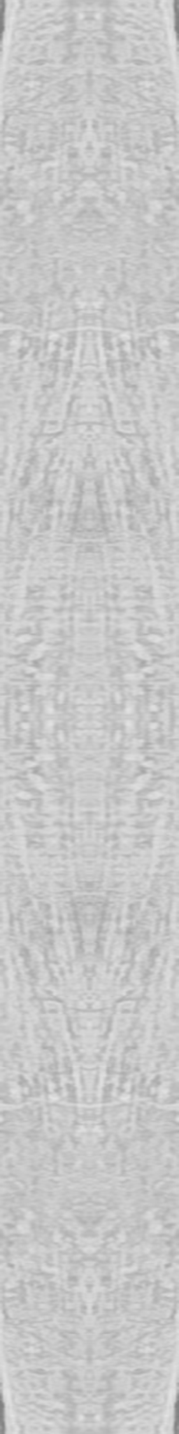
render/20260908.02-backyard-existing/textures/painted_timber_bump.png
