ericbusboom/garage-renovation/render/20260908.02-backyard-existing/textures/weathered_fence_bump.png

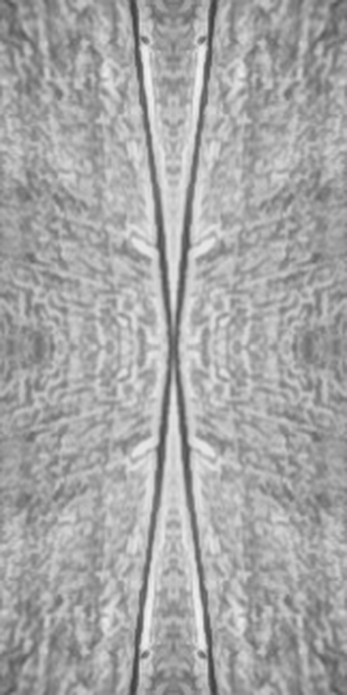
render/20260908.02-backyard-existing/textures/weathered_fence_bump.png
