ericbusboom/garage-renovation/render/20260908.02-backyard-existing/textures/woodchips_source.png

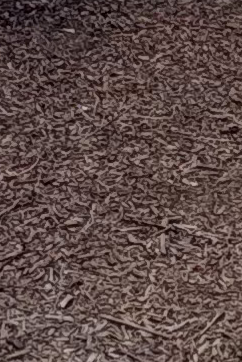
render/20260908.02-backyard-existing/textures/woodchips_source.png
