ericbusboom/garage-renovation/render/20260908.03-garage-site/northwest.png

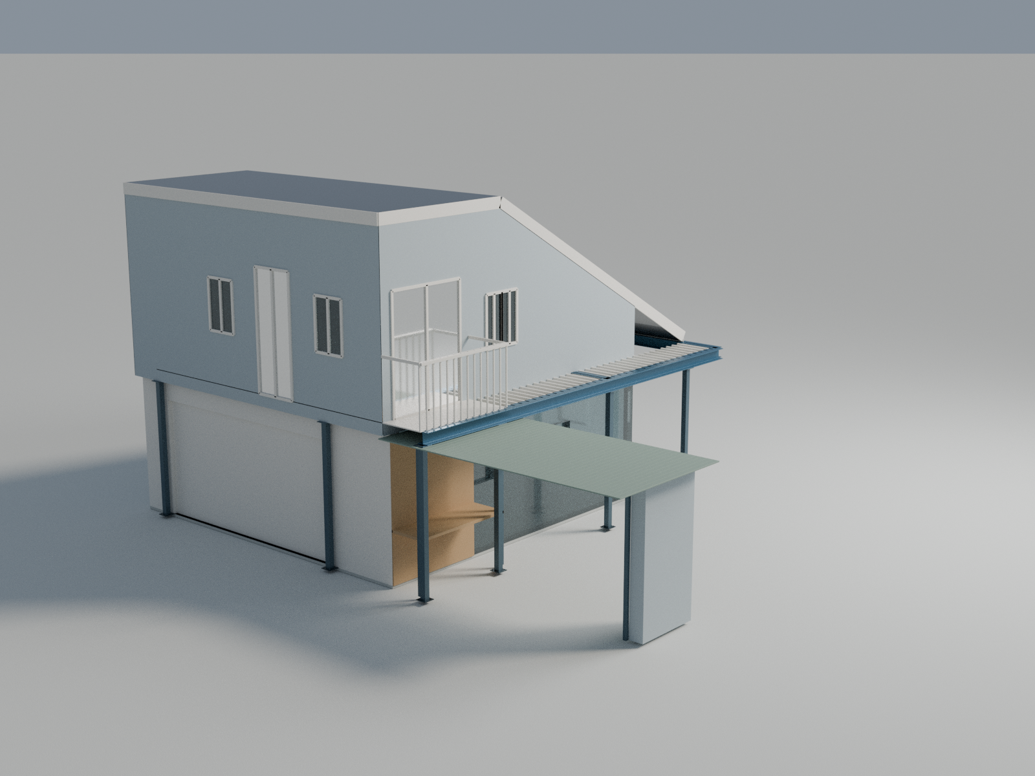
render/20260908.03-garage-site/northwest.png
