ericbusboom/garage-renovation/render/20260908.03-garage-site/site-house-context.png

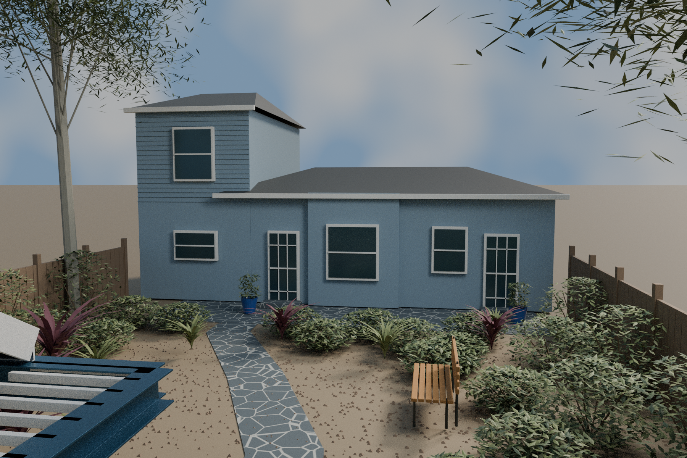
render/20260908.03-garage-site/site-house-context.png
