ericbusboom/garage-renovation/render/20260908.03-garage-site/site-references/video_4198.jpg

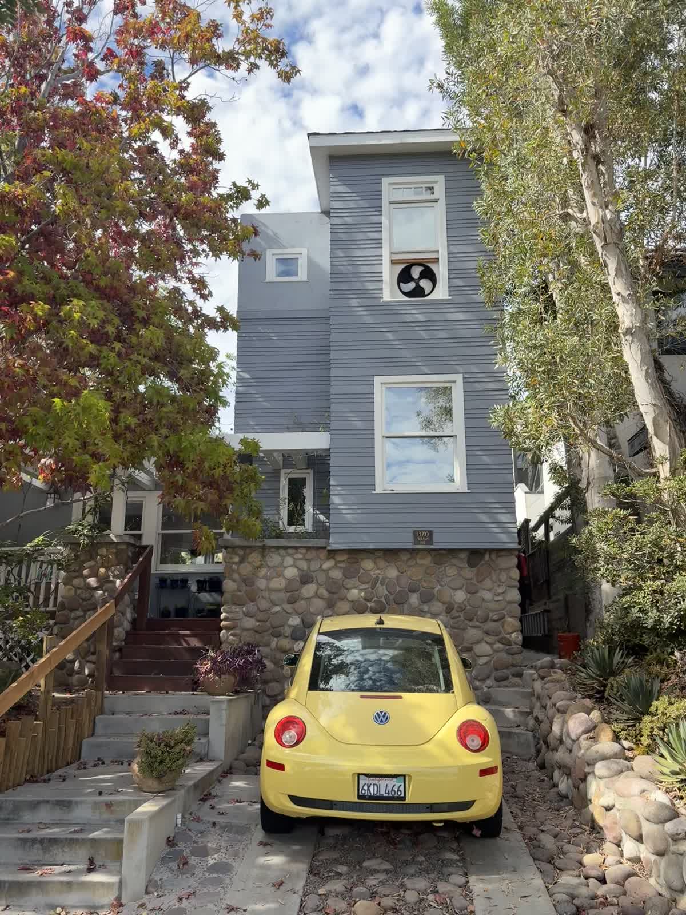
render/20260908.03-garage-site/site-references/video_4198.jpg
