ericbusboom/garage-renovation/render/20260908.03-garage-site/southwest.png

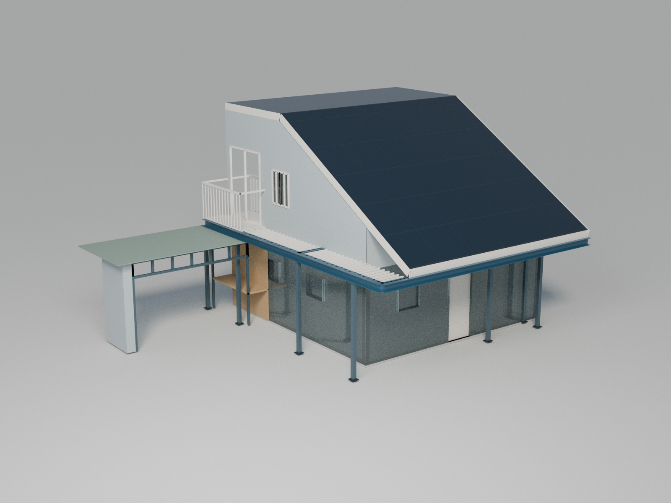
render/20260908.03-garage-site/southwest.png
