ericbusboom/garage-renovation/render/20260910.01-backyard-proposal/01-apocalypse-overview.png

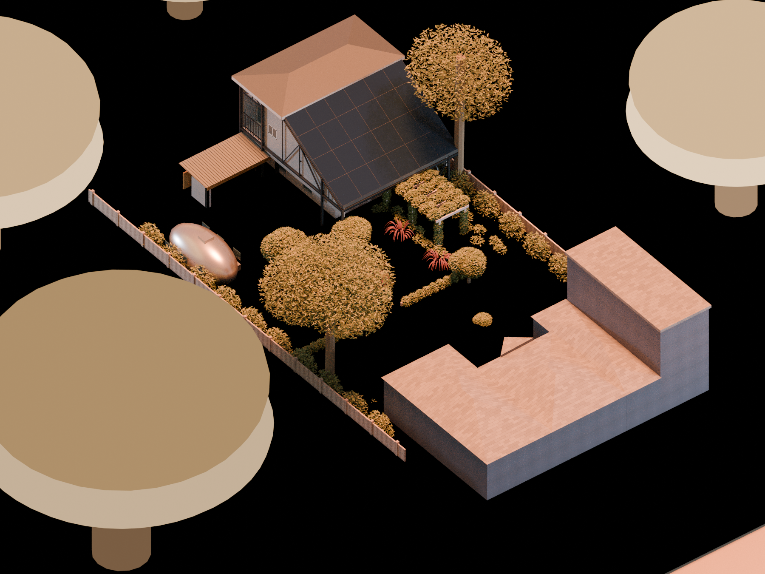
render/20260910.01-backyard-proposal/01-apocalypse-overview.png
