ericbusboom/garage-renovation/render/20260910.01-backyard-proposal/02-apocalypse-patio.png

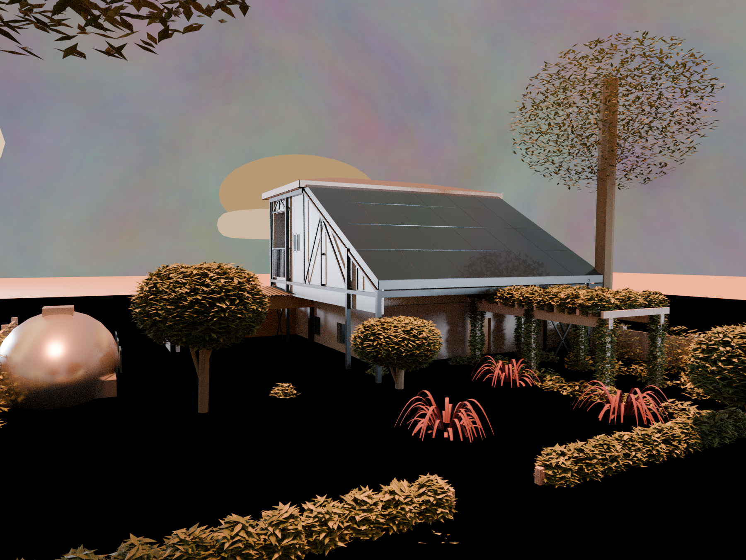
render/20260910.01-backyard-proposal/02-apocalypse-patio.png
