ericbusboom/garage-renovation/render/20260910.01-backyard-proposal/03-apocalypse-elevated.png

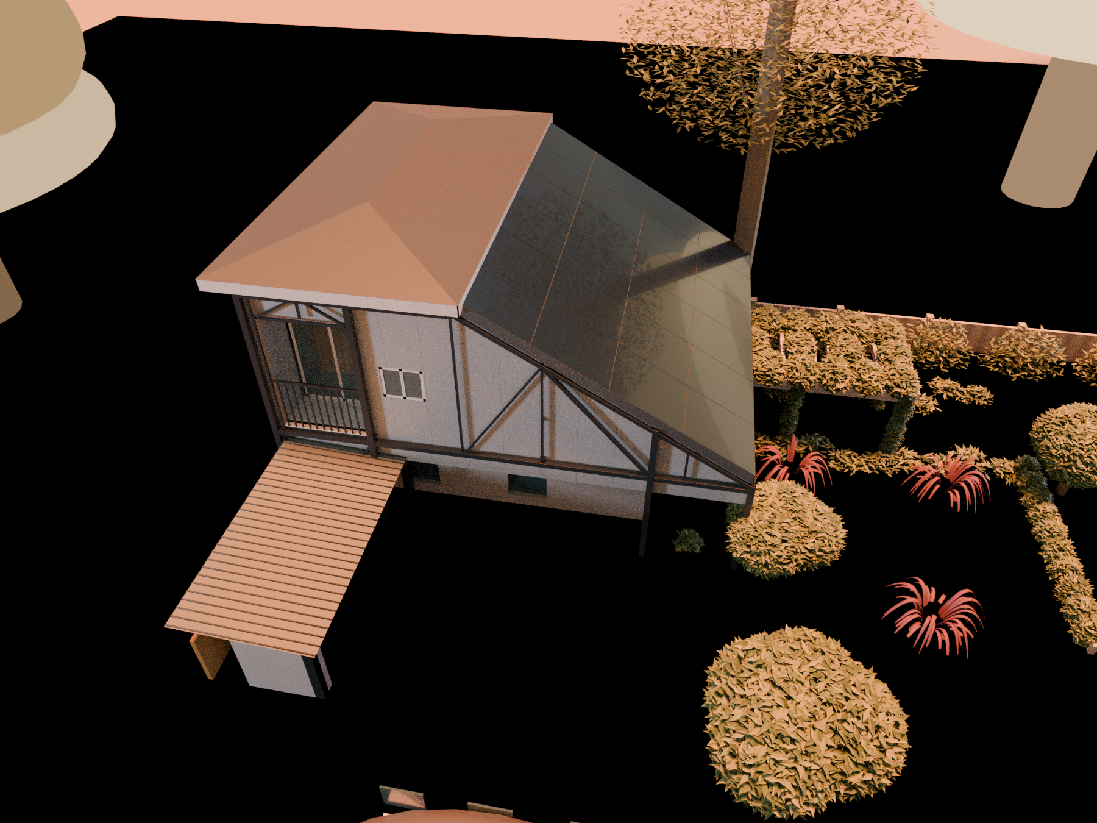
render/20260910.01-backyard-proposal/03-apocalypse-elevated.png
