ericbusboom/garage-renovation/render/20260910.01-backyard-proposal/04-apocalypse-southwest.png

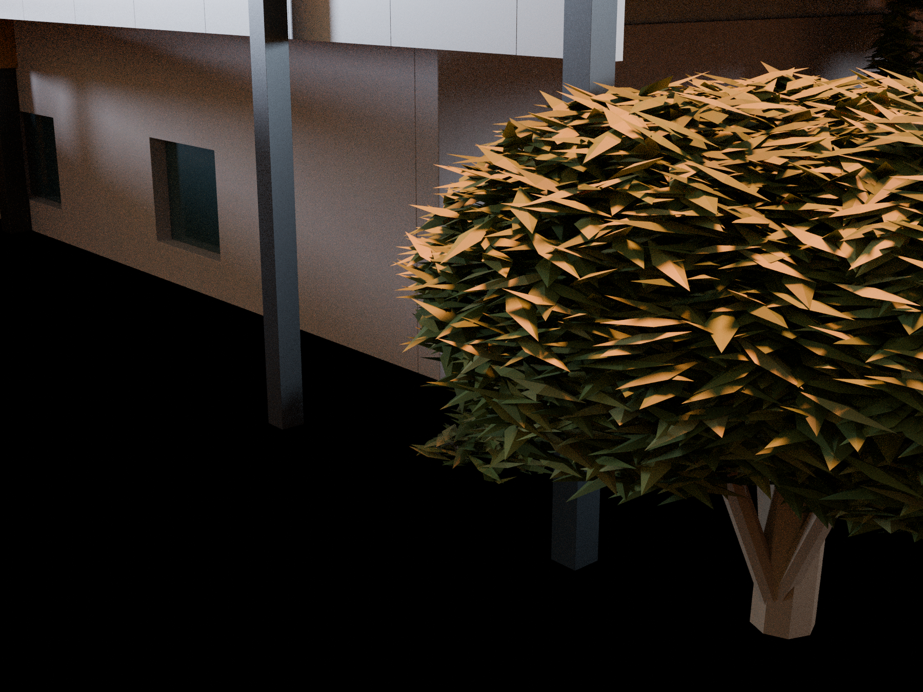
render/20260910.01-backyard-proposal/04-apocalypse-southwest.png
