ericbusboom/garage-renovation/render/20260910.01-backyard-proposal/05-apocalypse-northwest.png

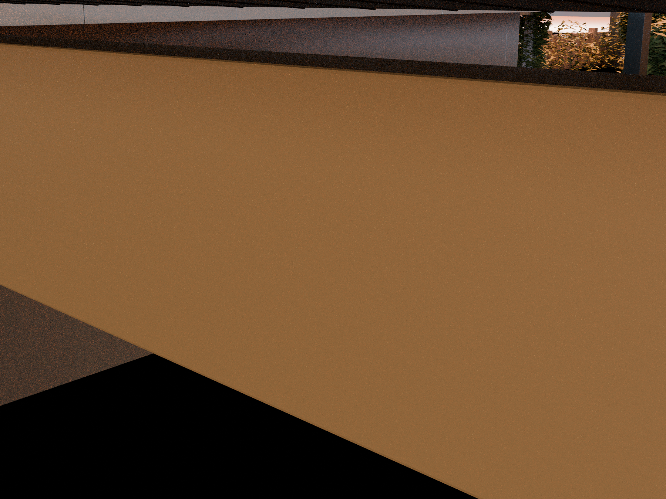
render/20260910.01-backyard-proposal/05-apocalypse-northwest.png
