ericbusboom/garage-renovation/render/20260910.01-backyard-proposal/05-exposed-northwest.png

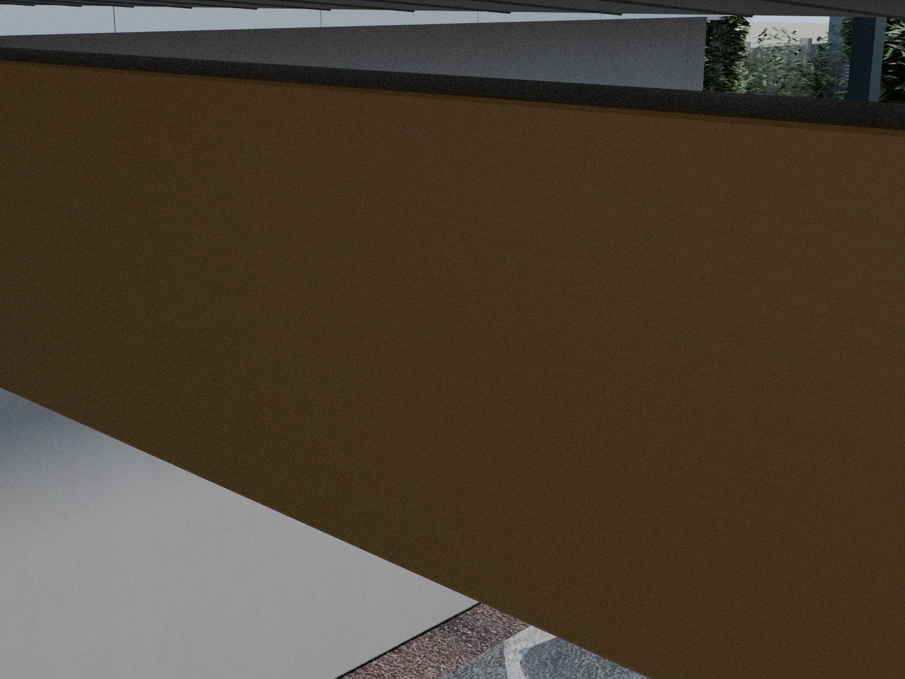
render/20260910.01-backyard-proposal/05-exposed-northwest.png
