ericbusboom/garage-renovation/report/06-structural-engineering/fea-study/figures/utilisation-adequate.png

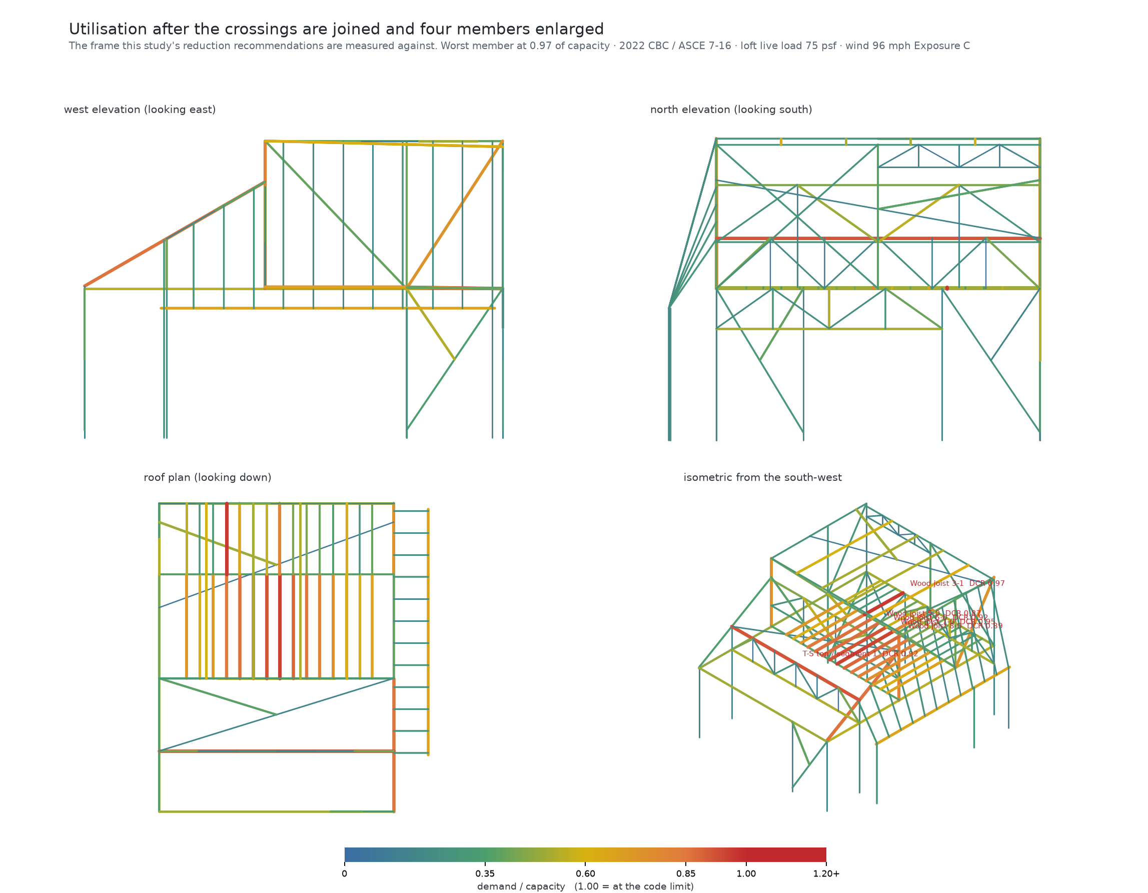
report/06-structural-engineering/fea-study/figures/utilisation-adequate.png
