ericbusboom/garage-renovation/report/06-structural-engineering/fea-study/figures/utilisation-as-drawn.png

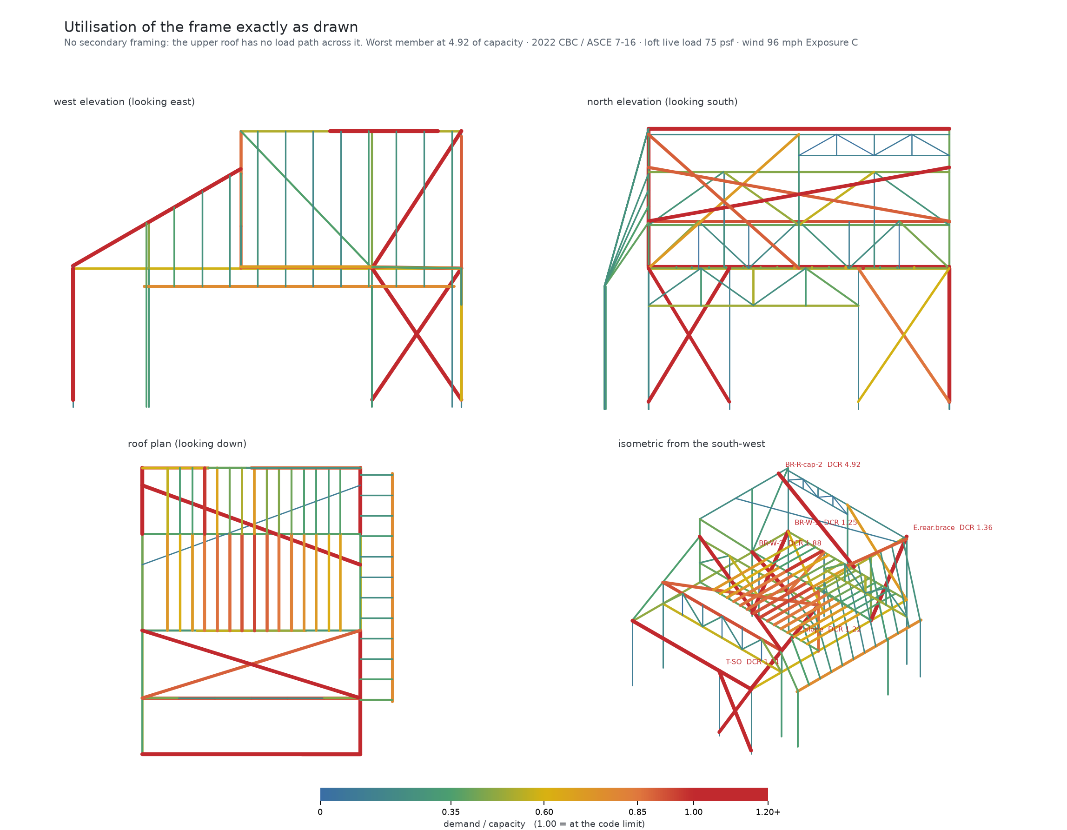
report/06-structural-engineering/fea-study/figures/utilisation-as-drawn.png
