ericbusboom/garage-renovation/report/06-structural-engineering/fea-study/figures/utilisation-histogram.png

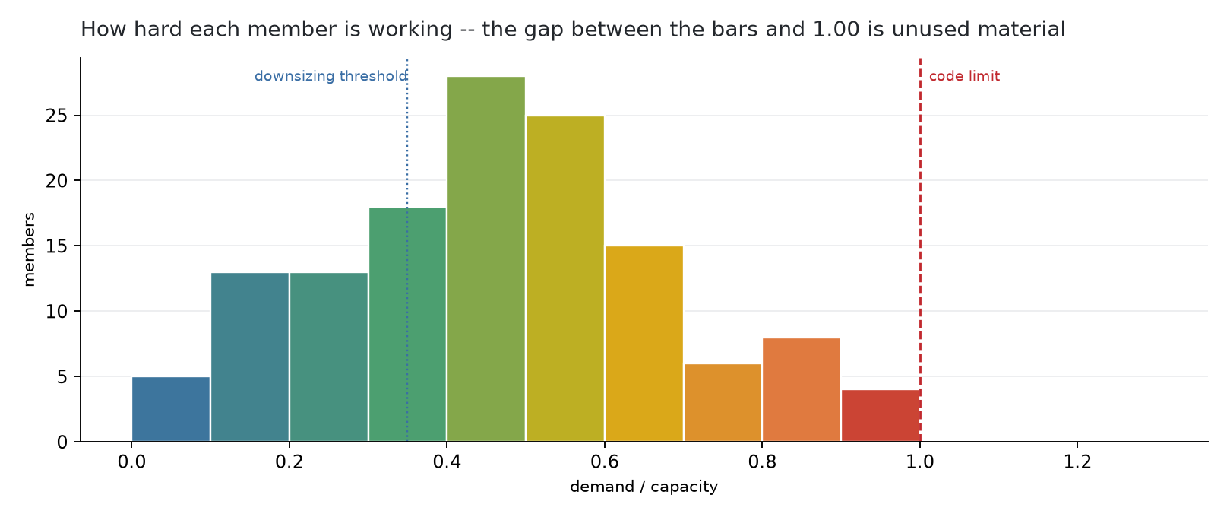
report/06-structural-engineering/fea-study/figures/utilisation-histogram.png
