ericbusboom/garage-renovation/report/06-structural-engineering/frame-geometry-study/floor-plan.png

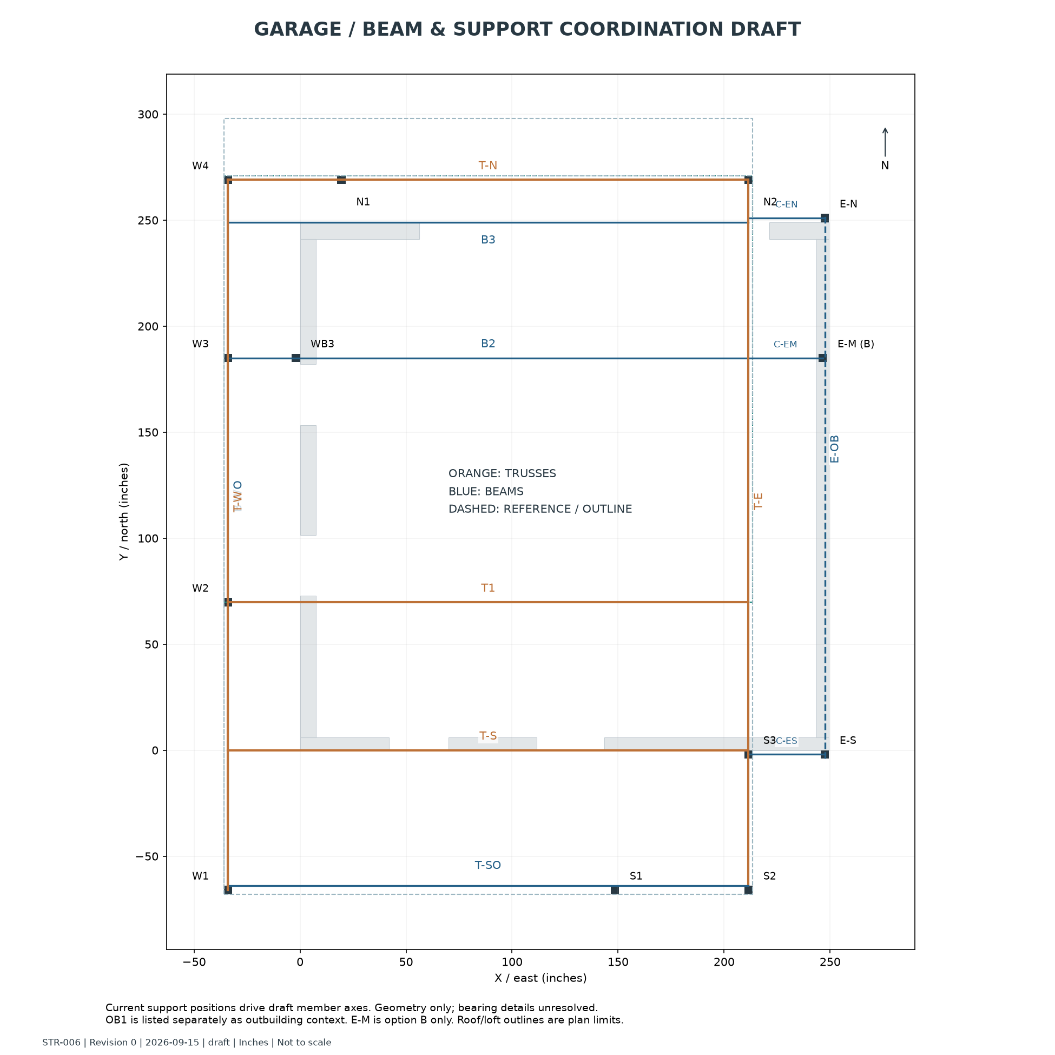
report/06-structural-engineering/frame-geometry-study/floor-plan.png
