ericbusboom/garage-renovation/report/06-structural-engineering/cost-reduction/existing-roof-clash.png

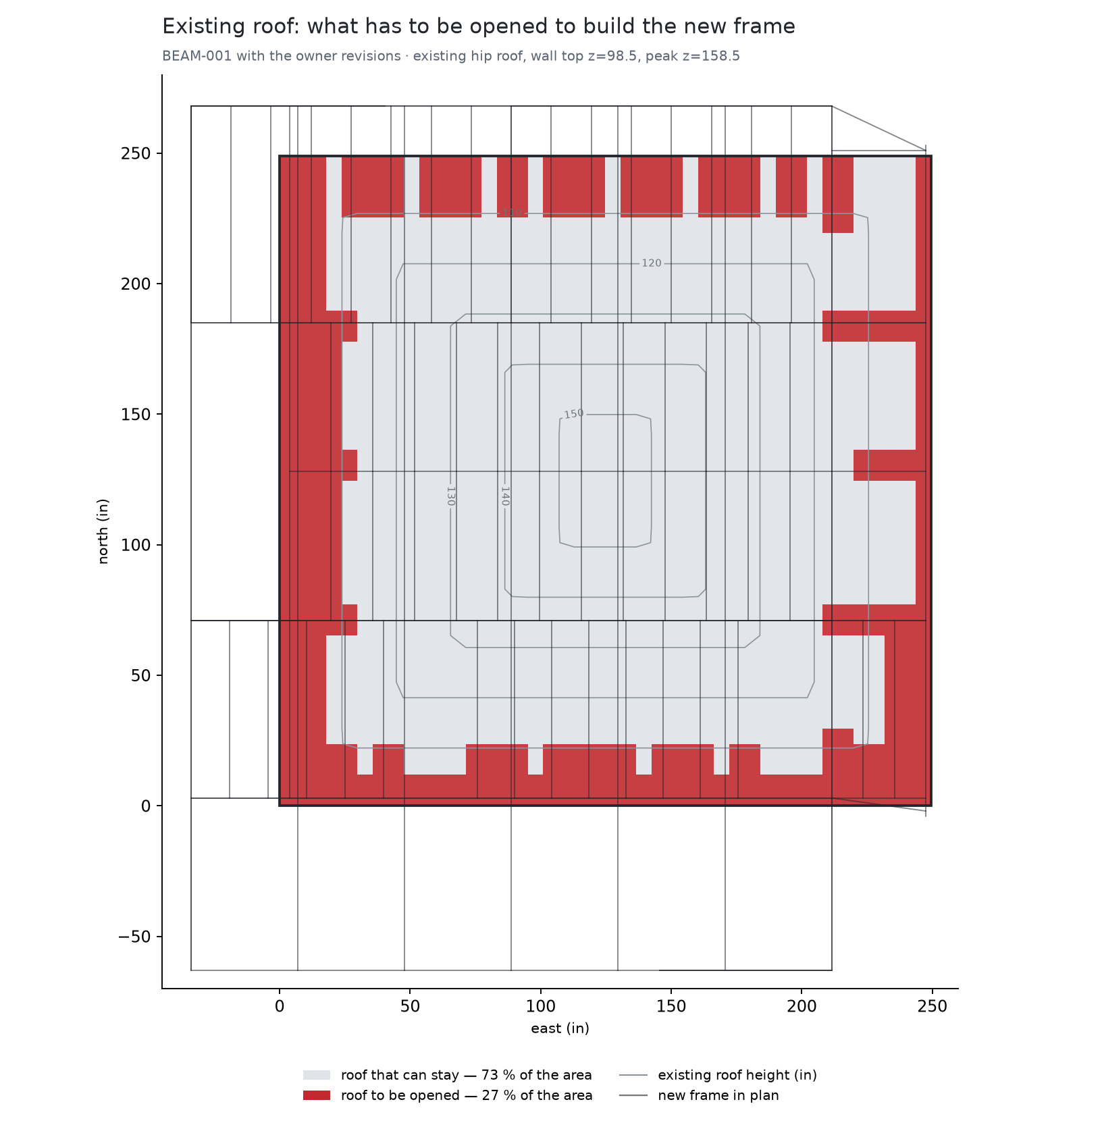
report/06-structural-engineering/cost-reduction/existing-roof-clash.png
