ericbusboom/garage-renovation/report/06-structural-engineering/cost-reduction/frame-plan-stair-middle.png

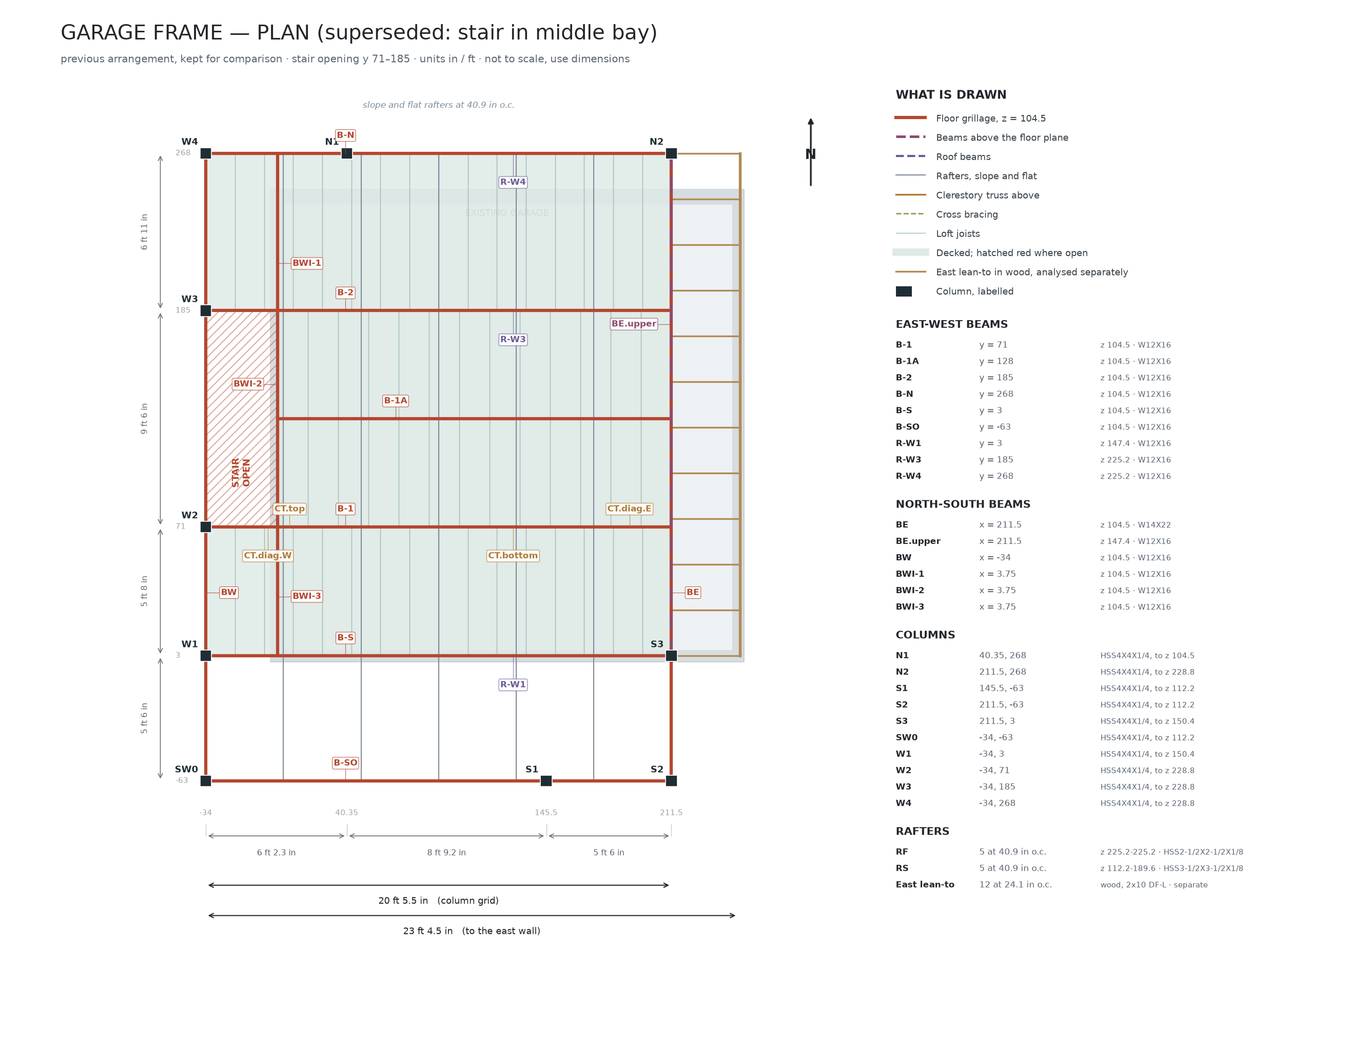
report/06-structural-engineering/cost-reduction/frame-plan-stair-middle.png
