ericbusboom/garage-renovation/report/07-building-envelope/README.md

# 07 — Building Envelope

This section turns the exposed-frame, inside-panel concept into a weatherproof and durable assembly. It covers the integrated solar roof, low hip cap, metal wall panels, insulation, thermal bridges, condensation, ventilation, waterproofing, flashing, drainage, soffit/fascia, openings, corrosion protection, and transitions to retained construction.

## Required outputs

- envelope basis and assembly schedule
- roof, wall, opening, base, edge, hip, balcony, and transition details
- drainage plan and overflow strategy
- condensation/ventilation analysis
- product data, compatibility record, warranties, and mockup/testing criteria

## Research record

[ENV-003 — Infill wall panel options](wall-panel-options/wall-panel-options.md), revision 1, 2026-09-17, status `draft`. Materials and market survey for the inside-frame panels: panel families and installed-cost ranges, the continuous-face versus bay-infill attachment decision, whether panels can supply lateral stiffness, candidate glazed bays, marine corrosion of the substrate, and the fire-code items the panel choice triggers. [Study notes](wall-panel-options/README.md).

Research only. No product is selected, no structural design is performed, no code determination is made, and every price is a published market range rather than a quotation. Revision 1 adds section 8A, carrying the coastal-corrosion finding through to the roof substrate, fasteners, gutters and PV attachment. Raises ENV-OI-01 through ENV-OI-12 in the [open items register](../00-project-controls/open-items.md).
