ericbusboom/garage-renovation/report/12-permit-and-construction-set/README.md

# 12 — Permit and Construction Set

This section holds frozen issue packages assembled from coordinated professional documents. Each issue must identify purpose, date, revision, contents, responsible professionals, and superseded issue.

## Expected packages

- permit application set
- plan-check comments and response set
- approved permit set
- bid issue set, if used
- construction issue set
- deferred submittals and approved revisions

Working CAD exports and automatic builds must not write directly here.
