ericbusboom/garage-renovation/studies/20260909.03-construction-sequence/roof-clearance.pdf

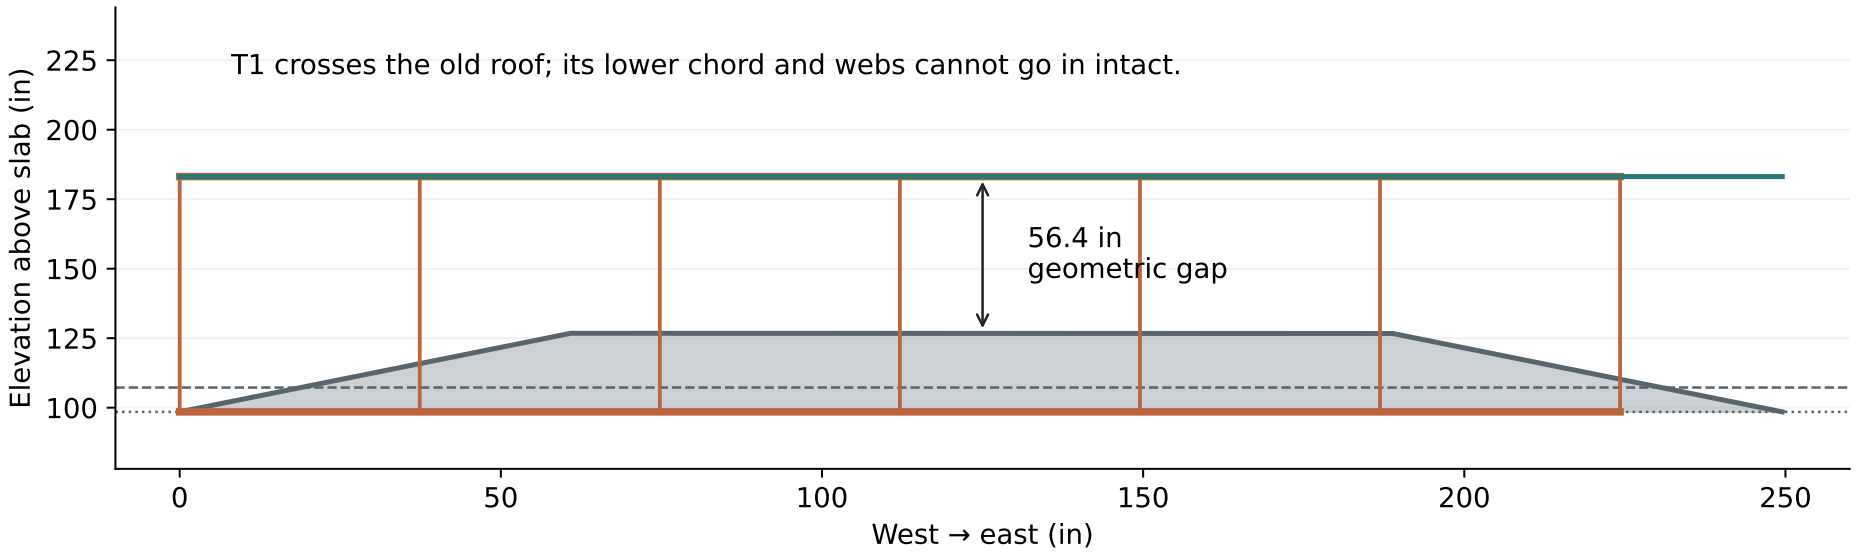
[picture p156: figure]
West east (in); Elevation above slab (in); 56.4 in geometric gap

T1 crosses the old roof; its lower chord and webs cannot go in intact.

T1 section · looking north · Y = 69.75 in

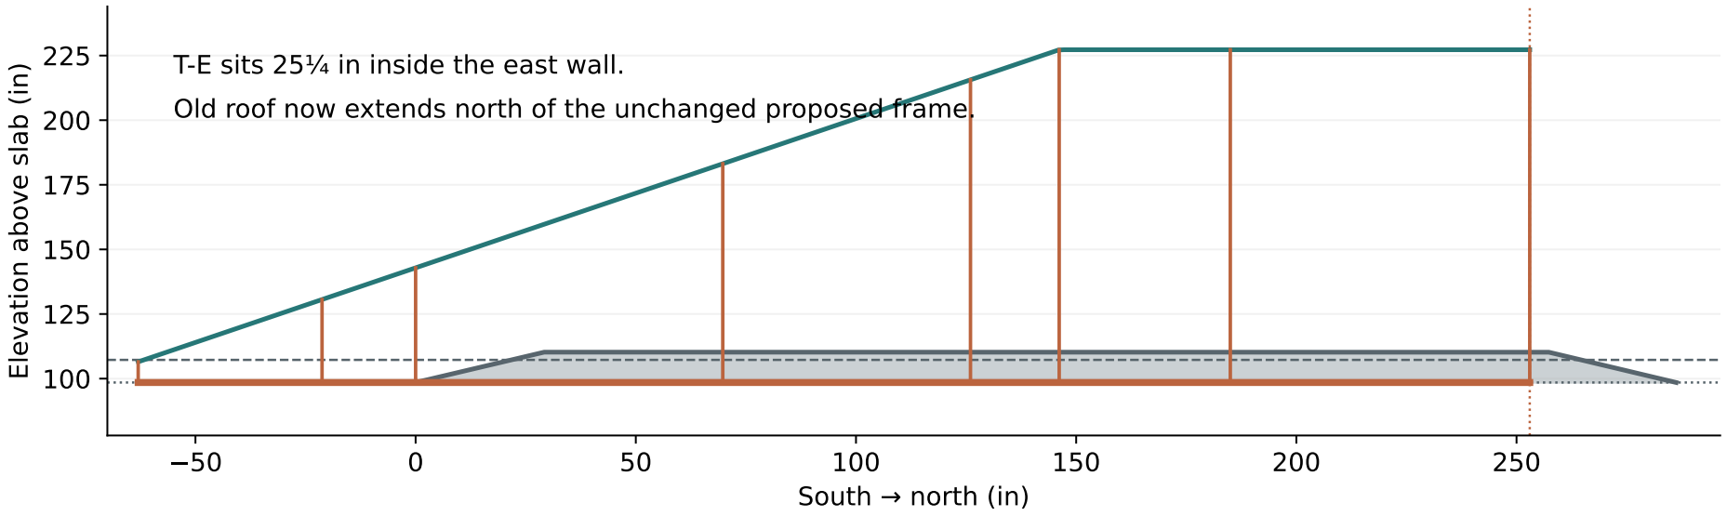
[picture p157: figure]
South north (in); Elevation above slab (in); T-E sits 25¼ in inside the east wall.

Old roof now extends north of the unchanged proposed frame.

T-E section · looking west · X = 224.25 in

## Roof-first construction: where the current framing conflicts

Corrected pyramid provisional 23 ft 10¼ in length eaves, connections and working clearances excluded.

Existing roof surface
New roof underside

Current full-depth truss
Future loft datum
