ericbusboom/garage-renovation/report/08-solar-electrical-and-energy/figures/battery-operation.pdf

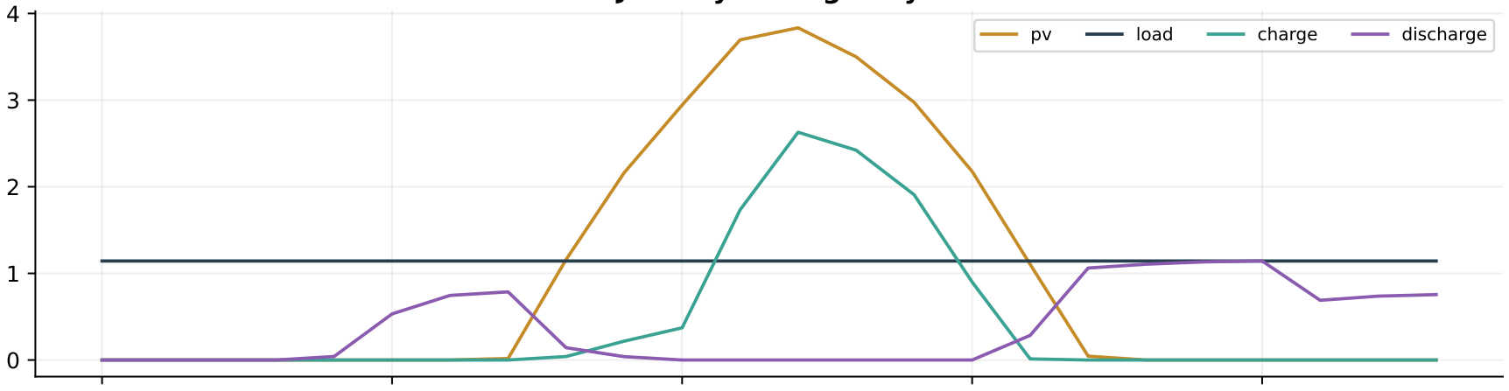
[picture p158: figure]
load; charge; discharge

### Average kW

## January average day

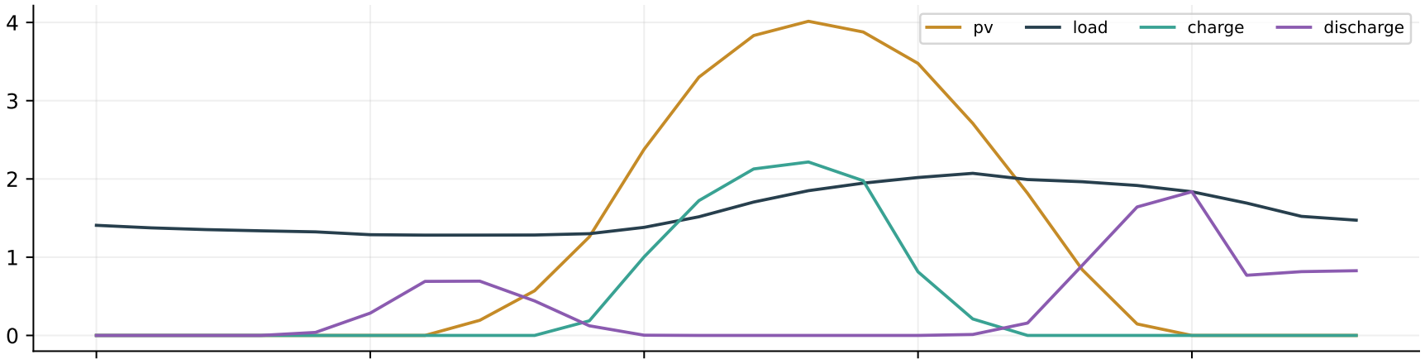
[picture p159: figure]
load; charge; discharge

0

5 | 10 | 15 | 20

### Local hour

### Average kW

## August average day
