ericbusboom/garage-renovation/studies/20260909.03-construction-sequence/existing-garage-corrected.pdf

Roof plan · four triangular faces | Three-dimensional shape · no ridge segment

8 ft 2½ in

4 ft 10 in

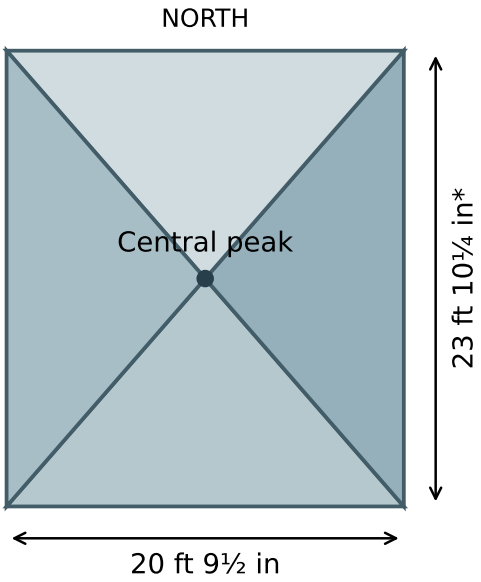
[picture p160: figure]
Central peak; NORTH

20 ft 9½ in

Peak 13 ft ½ in

## South elevation

8 ft 2½ in

4 ft 10 in

23 ft 10¼ in*

Peak 13 ft ½ in

## West elevation

# Existing garage · corrected pyramid roof

### Walls 8 ft 2½ in + roof rise 4 ft 10 in = peak 13 ft ½ in above slab

* Long footprint dimension provisional: adopted from the original plan label for this requested redraw. Roof starts at wall tops; eaves are not yet measured. Openings omitted to make the roof geometry clear.
