ericbusboom/garage-renovation/studies/20260915.03-solar/optimization/results/README.md

# Garage solar optimization

**Recommendation:** retain the 30° roof. Use **6–7 kW plus one roughly 13.5 kWh battery** if bill savings are the main objective. A typical-August target of 1,200 kWh requires **8.01 kW at 30°**, but the extra capacity has little financial value under SDG&E's Solar Billing Plan.

The mathematical August optimum is 13–14° south-facing: 7.80 kW reaches 1,200 kWh. It loses annual output and cannot fit on the current footprint at normal panel packing. At 30°, 8.01 kW needs 97.7% active coverage with 22%-efficient cells, or 93.5% with 23%-efficient cells.

Normal-year household use is estimated at **11,096 kWh/year**, based on a **1.14 kW** steady computer/base load plus temperature-related cooling.

Under central custom-roof costs, 6 kW + one battery is approximately break-even: **$3,465 first-year utility saving**, **$39,610 installed assumption**, and **$58/year** levelized net saving over 25 years. Removing the $7,500 custom-roof allowance from the solar investment raises modeled net savings to about **$590/year**.

Open `Garage-Solar-Optimization.pdf` for the full charts, monthly backfill, assumptions and sensitivity analysis.
