ericbusboom/garage-renovation/studies/20260911.01-structural-optimization/network-analysis/two-chord-design/networks/member-axial-results.csv

truss | stage | case | physical_member | maximum_compression_lb | maximum_tension_lb
T1 | complete | service40 | T1 upper lower chord | 665.8657351782792 | 2329.5268571242805
T1 | complete | service40 | T1 future floor beam | 0.0 | 681.8833246988623
T1 | complete | service40 | T1 vertical 1 | 0.0 | 1275.8092797043712
T1 | complete | service40 | T1 vertical 2 | 0.0 | 1106.621943666536
T1 | complete | service40 | T1 vertical 3 | 49.7087273835022 | 0.0
T1 | complete | service40 | T1 vertical 4 | 0.0 | 1148.6412895857145
T1 | complete | service40 | T1 vertical 5 | 0.0 | 725.8314201626888
T1 | complete | service40 | T1 diagonal 6 | 3291.295809728209 | 0.0
T1 | complete | service40 | T1 diagonal 7 | 0.0 | 1315.3334902522956
T1 | complete | service40 | T1 diagonal 8 | 0.0 | 1371.4701685469256
T1 | complete | service40 | T1 diagonal 9 | 3393.0731514310123 | 0.0
T1 | complete | service40 | T1 future hanger 1 | 0.0 | 340.95800310152146
T1 | complete | service40 | T1 future hanger 2 | 0.0 | 1125.922755924339
T1 | complete | service40 | T1 future hanger 3 | 0.0 | 1406.9286976736807
T1 | complete | service40 | T1 future hanger 4 | 0.0 | 1164.8534843308676
T1 | complete | service40 | T1 future hanger 5 | 0.0 | 208.21754964169145
T1 | complete | service40 | T1 top / segment 1 | 3775.7919828150652 | 176.29173672836907
T1 | complete | service_patches | T1 upper lower chord | 713.0639731831 | 2346.636079745963
T1 | complete | service_patches | T1 future floor beam | 0.0 | 727.4713399361907
T1 | complete | service_patches | T1 vertical 1 | 0.0 | 1293.3668154782602
T1 | complete | service_patches | T1 vertical 2 | 0.0 | 1107.4724775697096
T1 | complete | service_patches | T1 vertical 3 | 51.79649894520542 | 0.0
T1 | complete | service_patches | T1 vertical 4 | 0.0 | 1297.1148142611596
T1 | complete | service_patches | T1 vertical 5 | 0.0 | 834.0118442860157
T1 | complete | service_patches | T1 diagonal 6 | 3344.343406377771 | 0.0
T1 | complete | service_patches | T1 diagonal 7 | 0.0 | 1372.7138569439546
T1 | complete | service_patches | T1 diagonal 8 | 0.0 | 1288.6682104144925
T1 | complete | service_patches | T1 diagonal 9 | 3562.8139262873615 | 0.0
T1 | complete | service_patches | T1 future hanger 1 | 0.0 | 342.2551297446815
T1 | complete | service_patches | T1 future hanger 2 | 0.0 | 1128.9198928099652
T1 | complete | service_patches | T1 future hanger 3 | 0.0 | 1387.8084128906994
T1 | complete | service_patches | T1 future hanger 4 | 0.0 | 1320.7336593967132
T1 | complete | service_patches | T1 future hanger 5 | 0.0 | 292.4650620056057
T1 | complete | service_patches | T1 top / segment 1 | 3865.5840612355796 | 159.2421103924786
T1 | complete | typical30 | T1 upper lower chord | 516.5341065125746 | 1953.027327845794
T1 | complete | typical30 | T1 future floor beam | 0.0 | 571.3466485851599
T1 | complete | typical30 | T1 vertical 1 | 0.0 | 1062.028236310712
T1 | complete | typical30 | T1 vertical 2 | 0.0 | 909.6051447006436
T1 | complete | typical30 | T1 vertical 3 | 48.69433376945244 | 0.0
T1 | complete | typical30 | T1 vertical 4 | 0.0 | 951.6896282279198
T1 | complete | typical30 | T1 vertical 5 | 0.0 | 613.9151166925076
T1 | complete | typical30 | T1 diagonal 6 | 2765.5602522272297 | 0.0
T1 | complete | typical30 | T1 diagonal 7 | 0.0 | 1120.5830548590357
T1 | complete | typical30 | T1 diagonal 8 | 0.0 | 1121.2180842658317
T1 | complete | typical30 | T1 diagonal 9 | 2822.077266502135 | 0.0
T1 | complete | typical30 | T1 future hanger 1 | 0.0 | 276.73064680283534
T1 | complete | typical30 | T1 future hanger 2 | 0.0 | 917.2150313913891
T1 | complete | typical30 | T1 future hanger 3 | 0.0 | 1154.61895346857
T1 | complete | typical30 | T1 future hanger 4 | 0.0 | 956.7868604743887
T1 | complete | typical30 | T1 future hanger 5 | 0.0 | 198.13535220307418
T1 | complete | typical30 | T1 top / segment 1 | 3159.5473321421623 | 110.04013417304934
T1 | complete | storage125_sensitivity | T1 upper lower chord | 1550.7252033109808 | 5519.3648669166605
T1 | complete | storage125_sensitivity | T1 future floor beam | 0.0 | 1633.5573721845853
T1 | complete | storage125_sensitivity | T1 vertical 1 | 0.0 | 2846.2273086932
T1 | complete | storage125_sensitivity | T1 vertical 2 | 0.0 | 2716.9385856582826
T1 | complete | storage125_sensitivity | T1 vertical 3 | 57.7541495013745 | 0.0
T1 | complete | storage125_sensitivity | T1 vertical 4 | 0.0 | 2909.809842260913
T1 | complete | storage125_sensitivity | T1 vertical 5 | 0.0 | 1729.9849321894073
T1 | complete | storage125_sensitivity | T1 diagonal 6 | 7912.978141463399 | 0.0
T1 | complete | storage125_sensitivity | T1 diagonal 7 | 0.0 | 3280.1329412906434
T1 | complete | storage125_sensitivity | T1 diagonal 8 | 0.0 | 3180.01260305898
T1 | complete | storage125_sensitivity | T1 diagonal 9 | 8130.644990708595 | 0.0
T1 | complete | storage125_sensitivity | T1 future hanger 1 | 0.0 | 540.3527423939781
T1 | complete | storage125_sensitivity | T1 future hanger 2 | 0.0 | 2835.346066991463
T1 | complete | storage125_sensitivity | T1 future hanger 3 | 0.0 | 3547.6692589572317
T1 | complete | storage125_sensitivity | T1 future hanger 4 | 0.0 | 3021.6056820250496
T1 | complete | storage125_sensitivity | T1 future hanger 5 | 0.0 | 466.26712057739184
T1 | complete | storage125_sensitivity | T1 top / segment 1 | 9186.570940000274 | 207.84794811241548
T1 | complete | live_only | T1 upper lower chord | 416.40445626832377 | 1501.1002398192347
T1 | complete | live_only | T1 future floor beam | 0.0 | 447.84661075899254
T1 | complete | live_only | T1 vertical 1 | 0.0 | 739.0202487779231
T1 | complete | live_only | T1 vertical 2 | 0.0 | 757.7960669199016
T1 | complete | live_only | T1 vertical 3 | 3.7860810059921124 | 0.0
T1 | complete | live_only | T1 vertical 4 | 0.0 | 828.7852011468316
T1 | complete | live_only | T1 vertical 5 | 0.0 | 472.54282946798463
T1 | complete | live_only | T1 diagonal 6 | 2174.909411608952 | 0.0
T1 | complete | live_only | T1 diagonal 7 | 0.0 | 924.6115060313967
T1 | complete | live_only | T1 diagonal 8 | 0.0 | 851.0787932229593
T1 | complete | live_only | T1 diagonal 9 | 2229.4456202127813 | 0.0
T1 | complete | live_only | T1 future hanger 1 | 0.0 | 93.8328181615912
T1 | complete | live_only | T1 future hanger 2 | 0.0 | 804.4344994036511
T1 | complete | live_only | T1 future hanger 3 | 0.0 | 1007.4073230475041
T1 | complete | live_only | T1 future hanger 4 | 0.0 | 873.7657399338827
T1 | complete | live_only | T1 future hanger 5 | 0.0 | 121.4350922681309
T1 | complete | live_only | T1 top / segment 1 | 2546.2489196718498 | 22.01224839274998
T1 | complete | machine200 | T1 upper lower chord | 630.0680721008206 | 2360.9875049265215
T1 | complete | machine200 | T1 future floor beam | 0.0 | 695.3225298475063
T1 | complete | machine200 | T1 vertical 1 | 0.0 | 1262.2540368507994
T1 | complete | machine200 | T1 vertical 2 | 0.0 | 1096.9382981121514
T1 | complete | machine200 | T1 vertical 3 | 49.14653880589132 | 0.0
T1 | complete | machine200 | T1 vertical 4 | 0.0 | 1176.1833835749912
T1 | complete | machine200 | T1 vertical 5 | 0.0 | 742.461084075727
T1 | complete | machine200 | T1 diagonal 6 | 3357.447634898243 | 0.0
T1 | complete | machine200 | T1 diagonal 7 | 0.0 | 1405.1146573700448
T1 | complete | machine200 | T1 diagonal 8 | 0.0 | 1369.5040653017022
T1 | complete | machine200 | T1 diagonal 9 | 3443.4916458662956 | 0.0
T1 | complete | machine200 | T1 future hanger 1 | 0.0 | 301.05478338399
T1 | complete | machine200 | T1 future hanger 2 | 0.0 | 1116.351247565417
T1 | complete | machine200 | T1 future hanger 3 | 0.0 | 1458.288183954094
T1 | complete | machine200 | T1 future hanger 4 | 0.0 | 1193.4472458340397
T1 | complete | machine200 | T1 future hanger 5 | 0.0 | 227.8869877077195
T1 | complete | machine200 | T1 top / segment 1 | 3879.256771594921 | 113.32354705930244
T1 | complete | uplift20_sensitivity | T1 upper lower chord | 78.05685623975496 | 495.0968198669401
T1 | complete | uplift20_sensitivity | T1 future floor beam | 0.0 | 142.70199048338188
T1 | complete | uplift20_sensitivity | T1 vertical 1 | 0.0 | 275.63184913142715
T1 | complete | uplift20_sensitivity | T1 vertical 2 | 0.0 | 197.18707422141077
T1 | complete | uplift20_sensitivity | T1 vertical 3 | 27.444990372169368 | 0.0
T1 | complete | uplift20_sensitivity | T1 vertical 4 | 0.0 | 208.30507501845887
T1 | complete | uplift20_sensitivity | T1 vertical 5 | 0.0 | 161.92419995365472
T1 | complete | uplift20_sensitivity | T1 diagonal 6 | 698.6187280128017 | 0.0
T1 | complete | uplift20_sensitivity | T1 diagonal 7 | 0.0 | 292.67709724309844
T1 | complete | uplift20_sensitivity | T1 diagonal 8 | 0.0 | 252.26300671576328
T1 | complete | uplift20_sensitivity | T1 diagonal 9 | 676.3613595337134 | 0.0
T1 | complete | uplift20_sensitivity | T1 future hanger 1 | 0.0 | 83.04446895144189
T1 | complete | uplift20_sensitivity | T1 future hanger 2 | 0.0 | 180.73439418843836
T1 | complete | uplift20_sensitivity | T1 future hanger 3 | 0.0 | 238.98016334426626
T1 | complete | uplift20_sensitivity | T1 future hanger 4 | 0.0 | 191.2523440264895
T1 | complete | uplift20_sensitivity | T1 future hanger 5 | 0.0 | 84.51199537733112
T1 | complete | uplift20_sensitivity | T1 top / segment 1 | 770.2339679740272 | 46.695554318132864
T1 | complete | strength_screen | T1 upper lower chord | 1009.456484945694 | 3422.3899523207124
T1 | complete | strength_screen | T1 future floor beam | 0.0 | 1071.3369420290487
T1 | complete | strength_screen | T1 vertical 1 | 0.0 | 1834.3531056052202
T1 | complete | strength_screen | T1 vertical 2 | 0.0 | 1627.1281659026974
T1 | complete | strength_screen | T1 vertical 3 | 64.45782833647223 | 0.0
T1 | complete | strength_screen | T1 vertical 4 | 0.0 | 1954.6125138892412
T1 | complete | strength_screen | T1 vertical 5 | 0.0 | 1237.45709741337
T1 | complete | strength_screen | T1 diagonal 6 | 4916.989102121569 | 0.0
T1 | complete | strength_screen | T1 diagonal 7 | 0.0 | 2065.5350859798123
T1 | complete | strength_screen | T1 diagonal 8 | 0.0 | 1827.4749169099482
T1 | complete | strength_screen | T1 diagonal 9 | 5225.507104896977 | 0.0
T1 | complete | strength_screen | T1 future hanger 1 | 0.0 | 420.21972725118434
T1 | complete | strength_screen | T1 future hanger 2 | 0.0 | 1672.3571560816663
T1 | complete | strength_screen | T1 future hanger 3 | 0.0 | 2060.364371588532
T1 | complete | strength_screen | T1 future hanger 4 | 0.0 | 2004.0011241703191
T1 | complete | strength_screen | T1 future hanger 5 | 0.0 | 447.4247193208777
T1 | complete | strength_screen | T1 top / segment 1 | 5707.339577550056 | 146.43330158746141
T1 | complete | HB0.25 | T1 upper lower chord | 617.9958717240395 | 2329.7737950877904
T1 | complete | HB0.25 | T1 future floor beam | 0.0 | 702.0661137573521
T1 | complete | HB0.25 | T1 vertical 1 | 0.0 | 1259.20370346907
T1 | complete | HB0.25 | T1 vertical 2 | 0.0 | 1113.4795929260567
T1 | complete | HB0.25 | T1 vertical 3 | 50.84513889286808 | 0.0
T1 | complete | HB0.25 | T1 vertical 4 | 0.0 | 1170.7730805047483
T1 | complete | HB0.25 | T1 vertical 5 | 0.0 | 737.8895003090157
T1 | complete | HB0.25 | T1 diagonal 6 | 3333.2191060796617 | 0.0
T1 | complete | HB0.25 | T1 diagonal 7 | 0.0 | 1359.331480192925
T1 | complete | HB0.25 | T1 diagonal 8 | 0.0 | 1320.7768893845114
T1 | complete | HB0.25 | T1 diagonal 9 | 3384.876414059247 | 0.0
T1 | complete | HB0.25 | T1 future hanger 1 | 0.0 | 293.0038242337453
T1 | complete | HB0.25 | T1 future hanger 2 | 0.0 | 1133.531977837425
T1 | complete | HB0.25 | T1 future hanger 3 | 0.0 | 1401.8457490384008
T1 | complete | HB0.25 | T1 future hanger 4 | 0.0 | 1186.931791463535
T1 | complete | HB0.25 | T1 future hanger 5 | 0.0 | 224.9126297710568
T1 | complete | HB0.25 | T1 top / segment 1 | 3826.443881329148 | 77.5656972708265
T1 | complete | HB0.5 | T1 upper lower chord | 617.7073258774224 | 2328.4284516107277
T1 | complete | HB0.5 | T1 future floor beam | 0.0 | 707.4331418174792
T1 | complete | HB0.5 | T1 vertical 1 | 0.0 | 1262.9927526011827
T1 | complete | HB0.5 | T1 vertical 2 | 0.0 | 1113.371141908844
T1 | complete | HB0.5 | T1 vertical 3 | 51.29414982627211 | 0.0
T1 | complete | HB0.5 | T1 vertical 4 | 0.0 | 1180.6182498699181
T1 | complete | HB0.5 | T1 vertical 5 | 0.0 | 746.054491282433
T1 | complete | HB0.5 | T1 diagonal 6 | 3339.870248776208 | 0.0
T1 | complete | HB0.5 | T1 diagonal 7 | 0.0 | 1367.678920407191
T1 | complete | HB0.5 | T1 diagonal 8 | 0.0 | 1310.271072047755
T1 | complete | HB0.5 | T1 diagonal 9 | 3388.969210839178 | 0.0
T1 | complete | HB0.5 | T1 future hanger 1 | 0.0 | 294.28509152904104
T1 | complete | HB0.5 | T1 future hanger 2 | 0.0 | 1133.793193974754
T1 | complete | HB0.5 | T1 future hanger 3 | 0.0 | 1400.1247170390488
T1 | complete | HB0.5 | T1 future hanger 4 | 0.0 | 1196.445095227433
T1 | complete | HB0.5 | T1 future hanger 5 | 0.0 | 221.68116346879756
T1 | complete | HB0.5 | T1 top / segment 1 | 3838.6979539049576 | 60.47890787367309
T1 | complete | HB0.75 | T1 upper lower chord | 617.939082618512 | 2326.9777289659396
T1 | complete | HB0.75 | T1 future floor beam | 0.0 | 700.771807791239
T1 | complete | HB0.75 | T1 vertical 1 | 0.0 | 1258.6911796868649
T1 | complete | HB0.75 | T1 vertical 2 | 0.0 | 1106.0280951052582
T1 | complete | HB0.75 | T1 vertical 3 | 50.92223767036693 | 0.0
T1 | complete | HB0.75 | T1 vertical 4 | 0.0 | 1179.7153544521273
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
T1 | complete | HT0.75 | T1 future hanger 5 | 0.0 | 267.7405620843608
T1 | complete | HT0.75 | T1 top / segment 1 | 4633.355035906118 | 173.2187537449349
T1 | complete | storage125_strength_sensitivity | T1 upper lower chord | 2349.7144542057354 | 8498.756011262594
T1 | complete | storage125_strength_sensitivity | T1 future floor beam | 0.0 | 2521.074593943556
T1 | complete | storage125_strength_sensitivity | T1 vertical 1 | 0.0 | 4318.929895403027
T1 | complete | storage125_strength_sensitivity | T1 vertical 2 | 0.0 | 4202.2739390360875
T1 | complete | storage125_strength_sensitivity | T1 vertical 3 | 73.99006934826753 | 0.0
T1 | complete | storage125_strength_sensitivity | T1 vertical 4 | 0.0 | 4534.924559765764
T1 | complete | storage125_strength_sensitivity | T1 vertical 5 | 0.0 | 2671.0140383768685
T1 | complete | storage125_strength_sensitivity | T1 diagonal 6 | 12226.804678858045 | 0.0
T1 | complete | storage125_strength_sensitivity | T1 diagonal 7 | 0.0 | 5117.405621802423
T1 | complete | storage125_strength_sensitivity | T1 diagonal 8 | 0.0 | 4853.625944820616
T1 | complete | storage125_strength_sensitivity | T1 diagonal 9 | 12534.036809730544 | 0.0
T1 | complete | storage125_strength_sensitivity | T1 future hanger 1 | 0.0 | 737.1759071439992
T1 | complete | storage125_strength_sensitivity | T1 future hanger 2 | 0.0 | 4402.63903497426
T1 | complete | storage125_strength_sensitivity | T1 future hanger 3 | 0.0 | 5516.1417253564905
T1 | complete | storage125_strength_sensitivity | T1 future hanger 4 | 0.0 | 4725.396361365114
T1 | complete | storage125_strength_sensitivity | T1 future hanger 5 | 0.0 | 725.508013806664
T1 | complete | storage125_strength_sensitivity | T1 top / segment 1 | 14220.918581426253 | 224.20264500871468
T1 | complete | strength_roof | T1 upper lower chord | 781.0484330909468 | 2512.811191214724
T1 | complete | strength_roof | T1 future floor beam | 0.0 | 773.7086919523216
T1 | complete | strength_roof | T1 vertical 1 | 0.0 | 1412.335014796817
T1 | complete | strength_roof | T1 vertical 2 | 0.0 | 1180.2647656705774
T1 | complete | strength_roof | T1 vertical 3 | 61.00817752721154 | 0.0
T1 | complete | strength_roof | T1 vertical 4 | 0.0 | 1356.9881762051536
T1 | complete | strength_roof | T1 vertical 5 | 0.0 | 882.1818004325031
T1 | complete | strength_roof | T1 diagonal 6 | 3560.4239923307186 | 0.0
T1 | complete | strength_roof | T1 diagonal 7 | 0.0 | 1436.2972782105658
T1 | complete | strength_roof | T1 diagonal 8 | 0.0 | 1407.7394390116235
T1 | complete | strength_roof | T1 diagonal 9 | 3800.993238134743 | 0.0
T1 | complete | strength_roof | T1 future hanger 1 | 0.0 | 407.9878279613721
T1 | complete | strength_roof | T1 future hanger 2 | 0.0 | 1196.2571838388694
T1 | complete | strength_roof | T1 future hanger 3 | 0.0 | 1467.8958531475496
T1 | complete | strength_roof | T1 future hanger 4 | 0.0 | 1374.8012836325152
T1 | complete | strength_roof | T1 future hanger 5 | 0.0 | 301.7109234709175
T1 | complete | strength_roof | T1 top / segment 1 | 4103.365644043368 | 216.54610048101225
T1 | complete | strength_HB0.25 | T1 upper lower chord | 1005.2335320627368 | 3424.744203147826
T1 | complete | strength_HB0.25 | T1 future floor beam | 0.0 | 1101.3494428596414
T1 | complete | strength_HB0.25 | T1 vertical 1 | 0.0 | 1854.2257523085868
T1 | complete | strength_HB0.25 | T1 vertical 2 | 0.0 | 1650.2088568902975
T1 | complete | strength_HB0.25 | T1 vertical 3 | 66.3846843277698 | 0.0
T1 | complete | strength_HB0.25 | T1 vertical 4 | 0.0 | 1973.6319574942454
T1 | complete | strength_HB0.25 | T1 vertical 5 | 0.0 | 1246.7989811528148
T1 | complete | strength_HB0.25 | T1 diagonal 6 | 4955.279533910772 | 0.0
T1 | complete | strength_HB0.25 | T1 diagonal 7 | 0.0 | 2077.687962059081
T1 | complete | strength_HB0.25 | T1 diagonal 8 | 0.0 | 1806.3374904387304
T1 | complete | strength_HB0.25 | T1 diagonal 9 | 5234.207514927177 | 0.0
T1 | complete | strength_HB0.25 | T1 future hanger 1 | 0.0 | 408.72368194213766
T1 | complete | strength_HB0.25 | T1 future hanger 2 | 0.0 | 1696.6904711614015
T1 | complete | strength_HB0.25 | T1 future hanger 3 | 0.0 | 2052.9643153618904
T1 | complete | strength_HB0.25 | T1 future hanger 4 | 0.0 | 2022.7267182397236
T1 | complete | strength_HB0.25 | T1 future hanger 5 | 0.0 | 441.694326626971
T1 | complete | strength_HB0.25 | T1 top / segment 1 | 5755.8744807306175 | 88.53422094622015
T1 | complete | strength_HB0.5 | T1 upper lower chord | 1004.7718596836866 | 3422.5916531934467
T1 | complete | strength_HB0.5 | T1 future floor beam | 0.0 | 1109.936688181595
T1 | complete | strength_HB0.5 | T1 vertical 1 | 0.0 | 1860.288230697928
T1 | complete | strength_HB0.5 | T1 vertical 2 | 0.0 | 1650.035335628346
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
T1 | complete | strength_HT0.5 | T1 vertical 5 | 0.0 | 1482.7218800170679
T1 | complete | strength_HT0.5 | T1 diagonal 6 | 6583.793730896802 | 0.0
T1 | complete | strength_HT0.5 | T1 diagonal 7 | 0.0 | 3553.852359502851
T1 | complete | strength_HT0.5 | T1 diagonal 8 | 0.0 | 3432.8757349509197
T1 | complete | strength_HT0.5 | T1 diagonal 9 | 6913.8997850874475 | 0.0
T1 | complete | strength_HT0.5 | T1 future hanger 1 | 0.0 | 452.5184152317144
T1 | complete | strength_HT0.5 | T1 future hanger 2 | 0.0 | 1797.2685025582296
T1 | complete | strength_HT0.5 | T1 future hanger 3 | 0.0 | 3873.341947559598
T1 | complete | strength_HT0.5 | T1 future hanger 4 | 0.0 | 2078.1776994964844
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
