ericbusboom/garage-renovation/report/08-solar-electrical-and-energy/figures/battery-sizing.pdf

2500

# One battery captures most of the modeled bill benefit

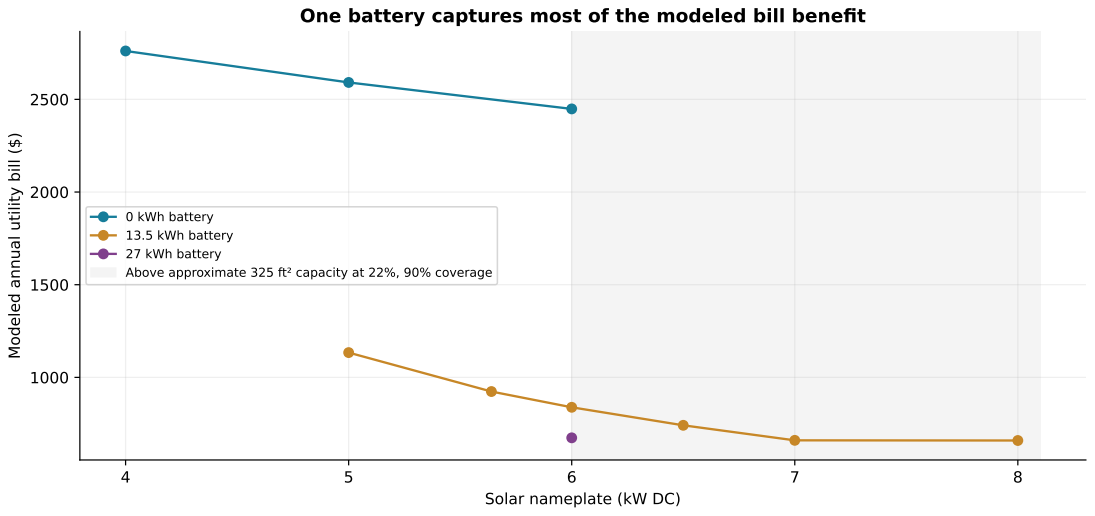
[picture p170: page 1]
0 kWh battery; 13.5 kWh battery; 27 kWh battery; Above approximate 325 ft² capacity; at 22%, 90% coverage

Modeled annual utility bill ($)

Solar nameplate (kW DC)
