ericbusboom/garage-renovation/report/08-solar-electrical-and-energy/figures/geometry-tradeoff.pdf

360

## Panel area versus roof footprint

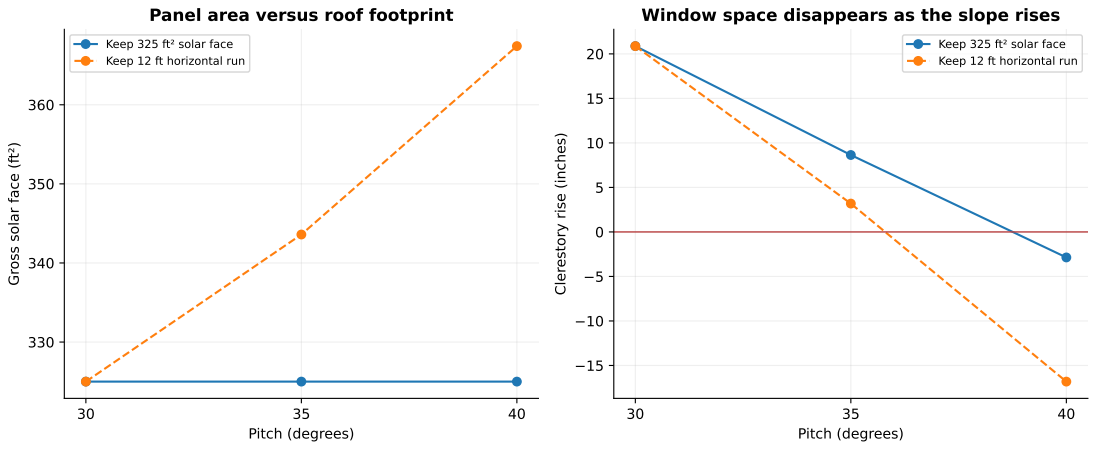
[picture p171: page 1]
Pitch (degrees)

Window space disappears as the slope rises

Keep 325 ft² solar face
Keep 12 ft horizontal run

Clerestory rise (inches)

Gross solar face (ft²)
