ericbusboom/garage-renovation/report/08-solar-electrical-and-energy/historical/Solar-Analysis-Charts.pdf

# Your base load dominates the year; cooling drives the summer increase

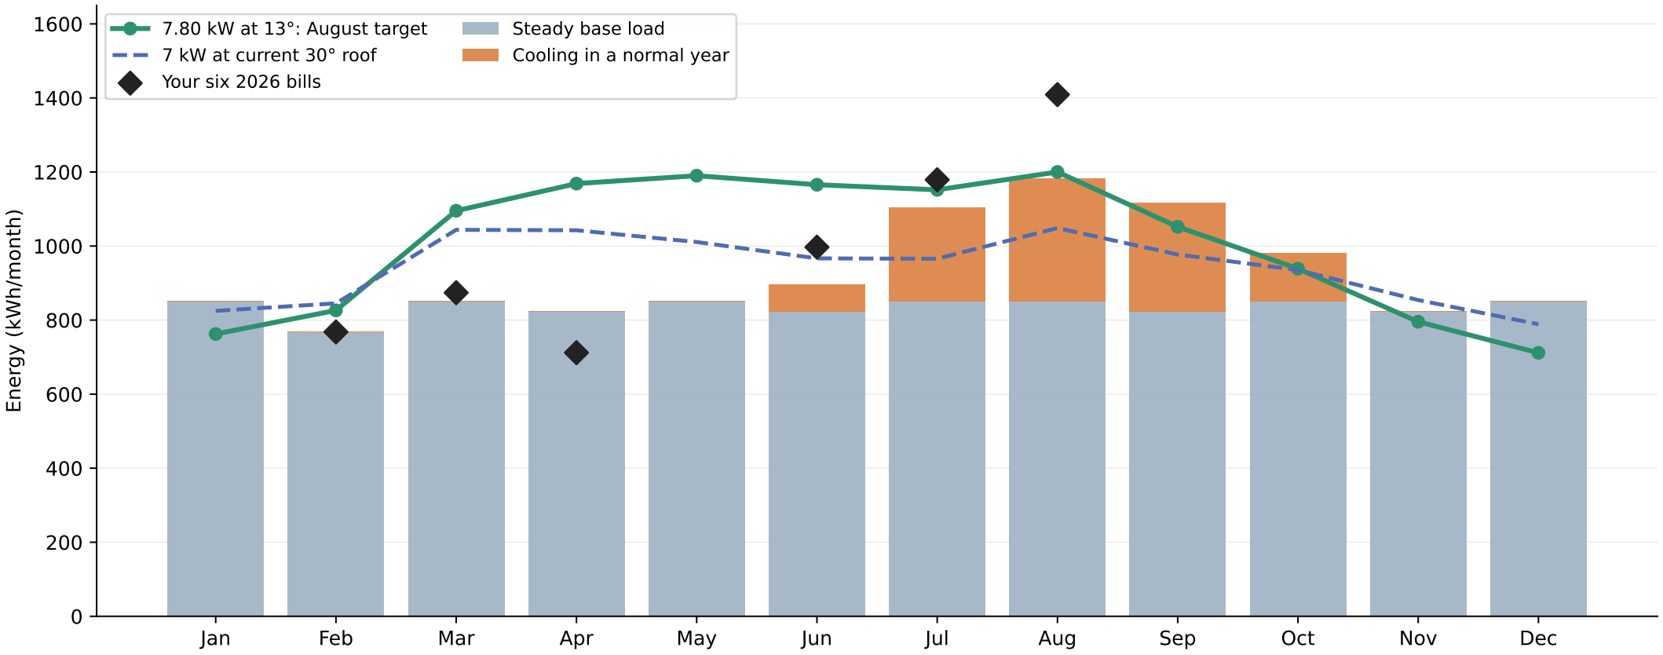
[picture p172: figure]
Jan; Feb; Mar; Apr; May; Jun; Jul; Aug; Sep; Oct; Nov; Dec; Energy (kWh/month); 7.80 kW at 13°: August target; 7 kW at current 30° roof; Your six 2026 bills; Steady base load; Cooling in a normal year

# Utility charges only — equipment cost is compared separately

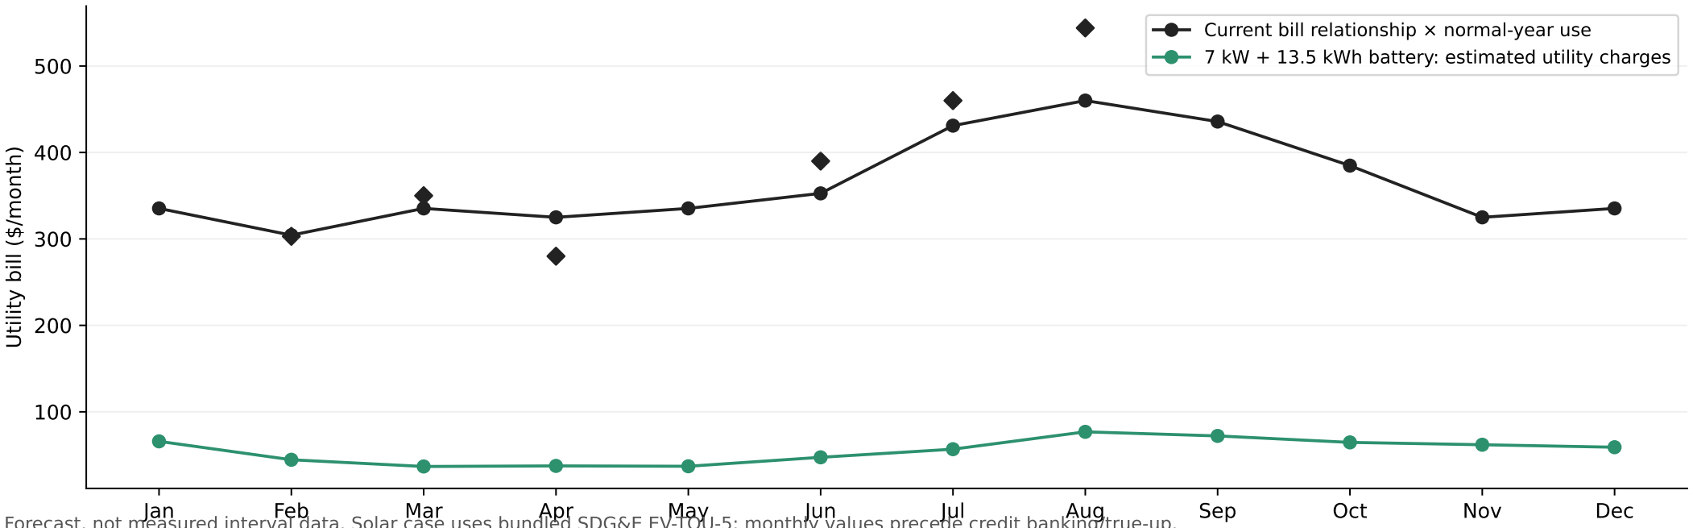
[picture p173: figure]
Jan; Feb; Mar; Apr; May; Jun; Jul; Aug; Sep; Oct; Nov; Dec; Utility bill ($/month)

Current bill relationship × normal-year use
7 kW + 13.5 kWh battery: estimated utility charges

Forecast, not measured interval data. Solar case uses bundled SDG&E EV-TOU-5; monthly values precede credit banking/true-up. Normal weather: 1991–2020 ERA5. Solar: PVGIS NSRDB 2005–2015. No gas charges or climate credits modeled.

# Fit: 27.43 + 1.53 × max(T − 63.6, 0)

# Coastal San Diego weather

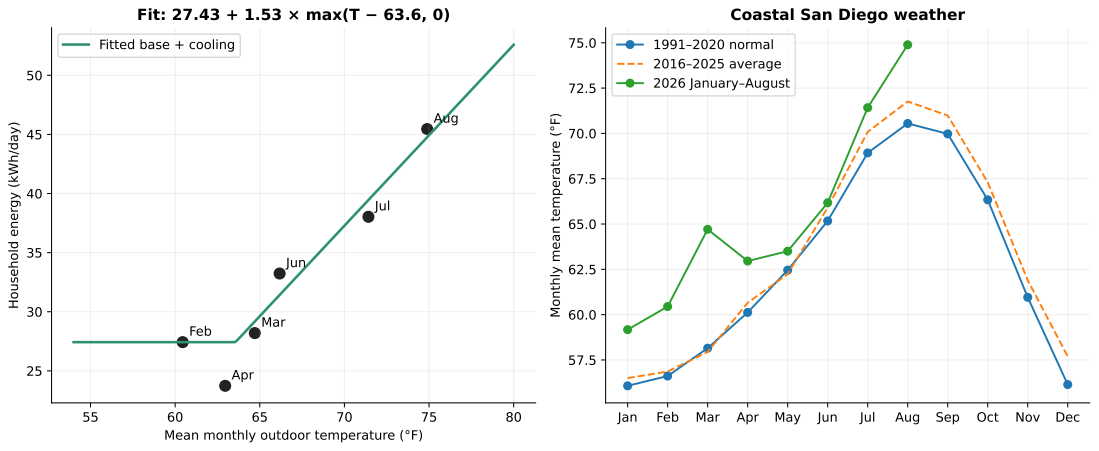
[picture p174: page 2]
Feb; Mar; Apr; Jun; Jul; Aug; Fitted base; + cooling; Jan; May; Sep; Oct; Nov; Dec; 1991–2020 normal; 2016–2025 average; 2026 January–August

Monthly mean temperature (°F)

Household energy (kWh/day)

Mean monthly outdoor temperature (°F)

# Summer production per panel

# 22% modules, 90% generating panel coverage

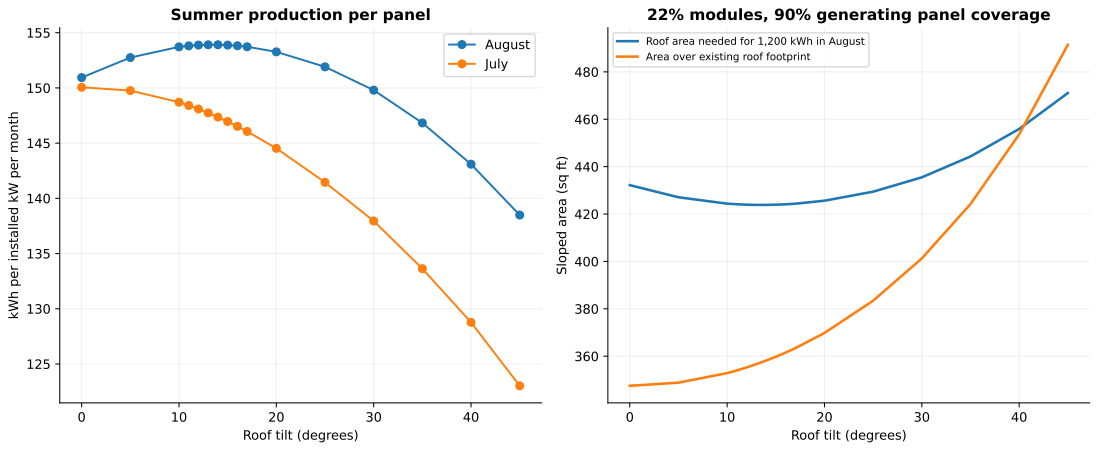
[picture p175: page 3]
August; July

Roof area needed for 1,200 kWh in August
Area over existing roof footprint

kWh per installed kW per month

Sloped area (sq ft)

Roof tilt (degrees)

Net saving after amortized equipment ($/month)

# Financial comparison — current 30° roof, custom solar finish

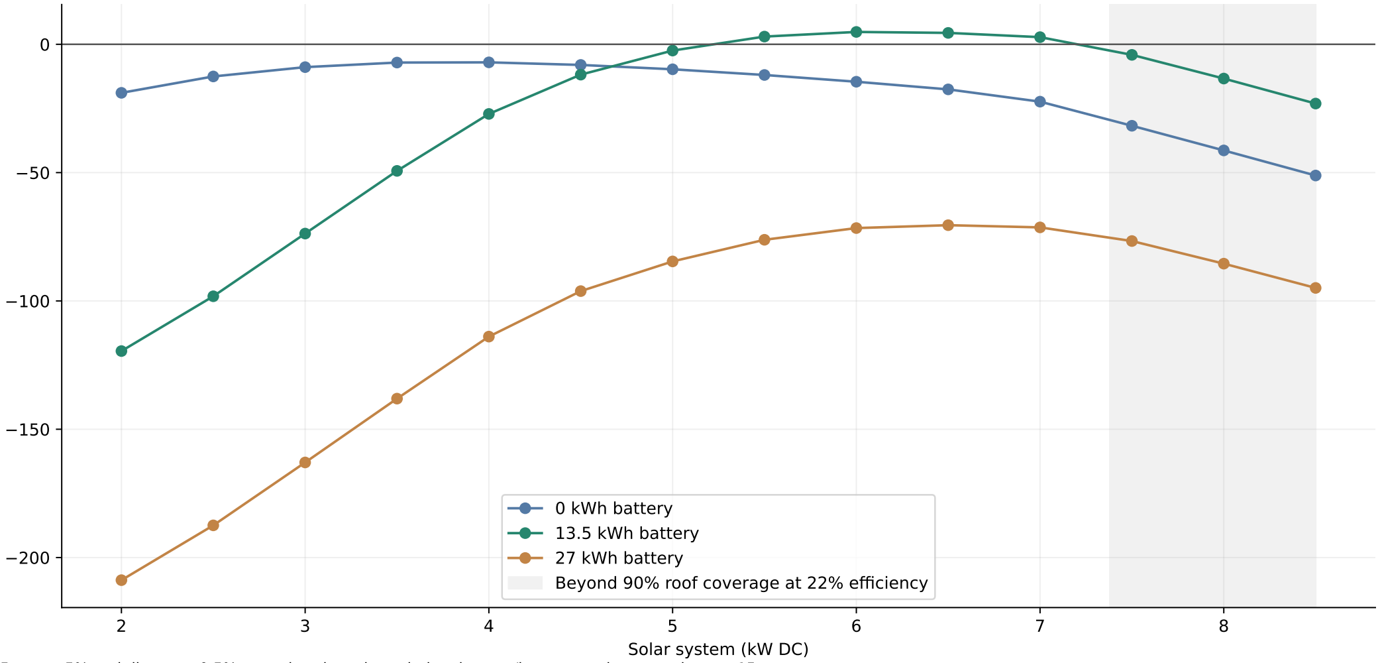
[picture p176: figure]
Solar system (kW DC); 0 kWh battery; 13.5 kWh battery; 27 kWh battery

Beyond 90% roof coverage at 22% efficiency

25 years, 5% real discount, 0.5% annual savings degradation; battery/inverter replacement in year 15.
Includes 7, 500custom − roofallowance + 2,500 electrical allowance; no rebate. Utility tariff and hourly household profile provisional.
