ericbusboom/garage-renovation/report/06-structural-engineering/frame-geometry-study/frame-geometry-study.pdf

## GARAGE / BEAM & SUPPORT COORDINATION DRAFT

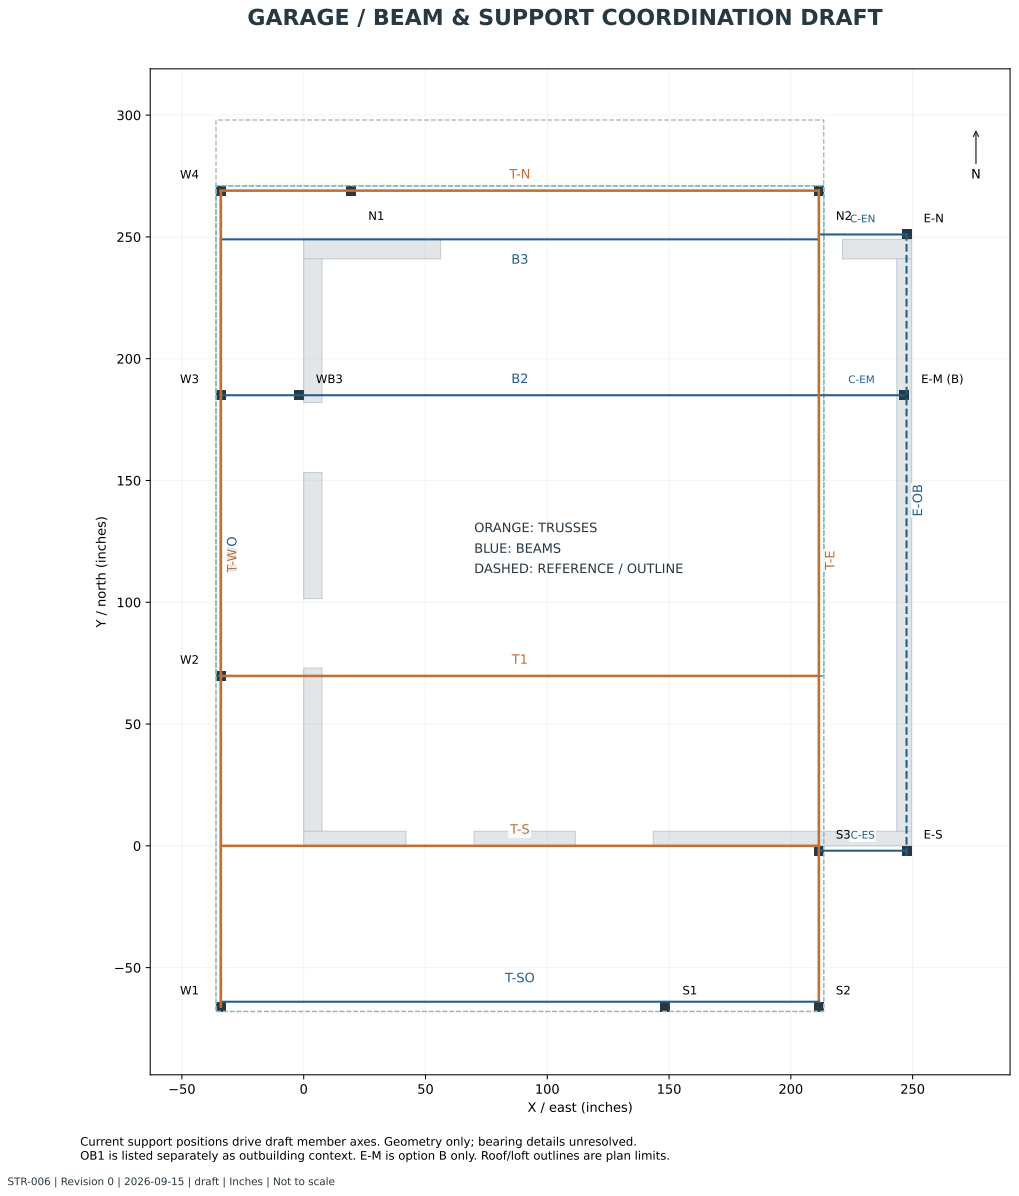
[picture p177: page 1]
X / east (inches); Y / north (inches)

ORANGE: TRUSSES BLUE: BEAMS DASHED: REFERENCE / OUTLINE

Current support positions drive draft member axes. Geometry only; bearing details unresolved.
OB1 is listed separately as outbuilding context. E-M is option B only. Roof/loft outlines are plan limits.

STR-006 | Revision 0 | 2026-09-15 | draft | Inches | Not to scale

Support | Center X | Center Y | Plan symbol | Status | Base / top Z
E-M | 246.5 | 185 | 4 × 4 | B only | 0 / 98.5 trial
E-N | 247.5 | 251 | 4 × 4 | A and B | 0 / 98.5 trial
E-S | 247.5 | -2 | 4 × 4 | A and B | 0 / 98.5 trial
N1 | 19.5 | 269 | 4 × 4 | proposed | 0 / 98.5
N2 | 211.5 | 269 | 4 × 4 | proposed | 0 / 98.5
S1 | 148.5 | -66 | 4 × 4 | proposed | 0 / 98.5
S2 | 211.5 | -66 | 4 × 4 | proposed | 0 / 98.5
S3 | 211.5 | -2 | 4 × 4 | proposed | 0 / 98.5
W1 | -34 | -66 | 4 × 4 | proposed | 0 / 98.5
W2 | -34 | 69.75 | 4 × 4 | proposed | 0 / 98.5
W3 | -34 | 185 | 4 × 4 | proposed | 0 / 98.5
W4 | -34 | 269 | 4 × 4 | proposed | 0 / 98.5
WB3 | -2 | 185 | 4 × 4 | proposed | 0 / 98.5

# SUPPORT POSITION SCHEDULE / INCHES

SW exterior garage corner is X=0, Y=0. Symbol dimensions do not select structural sections. All current support coordinates come from the floor-plan basis; E-M is an option-B support.

Member | Type | Start (X, Y) | End (X, Y) | Ref. length | Bottom Z
B-WO | beam | (-34, -66) | (-34, 269) | 335.00 | 98.5
B2 | beam | (-34, 185) | (211.5, 185) | 245.50 | 98.5
B3 | beam | (-34, 249) | (211.5, 249) | 245.50 | 98.5
C-EM | beam | (246.5, 185) | (211.5, 185) | 35.00 | 98.5
C-EN | beam | (247.5, 251) | (211.5, 251) | 36.00 | 98.5
C-ES | beam | (247.5, -2) | (211.5, -2) | 36.00 | 98.5
E-OB | beam | (247.5, -4) | (247.5, 253) | 257.00 | 98.5
O2 | subsegment | (-34, 69.75) | (0, 69.75) | 34.00 | 98.5
O3 | subsegment | (-34, 185) | (0, 185) | 34.00 | 98.5
OB1 | context beam | (-164.25, 174) | (-27, 174) | 137.25 | unknown
T-E | truss | (211.5, -64) | (211.5, 269) | 333.00 | 98.5
T-N | truss | (-34, 269) | (211.5, 269) | 245.50 | 98.5
T-S | truss | (-34, 0) | (211.5, 0) | 245.50 | 98.5
T-SO | beam | (-34, -64) | (211.5, -64) | 245.50 | 98.5
T-W | truss | (-34, -66) | (-34, 269) | 335.00 | 98.5
T1 | truss | (-34, 69.75) | (211.5, 69.75) | 245.50 | 98.5

# BEAM & TRUSS POSITION SCHEDULE / INCHES

Plan lines are reference axes, not solid member envelopes. Lengths are not fabrication cuts.
Draft positions and source assumptions are itemized in coordination-report.md. E-OB uses a provisional 3-inch display envelope. OB1 elevation is unknown.

# T-S / PARAMETRIC TRUSS STUDY

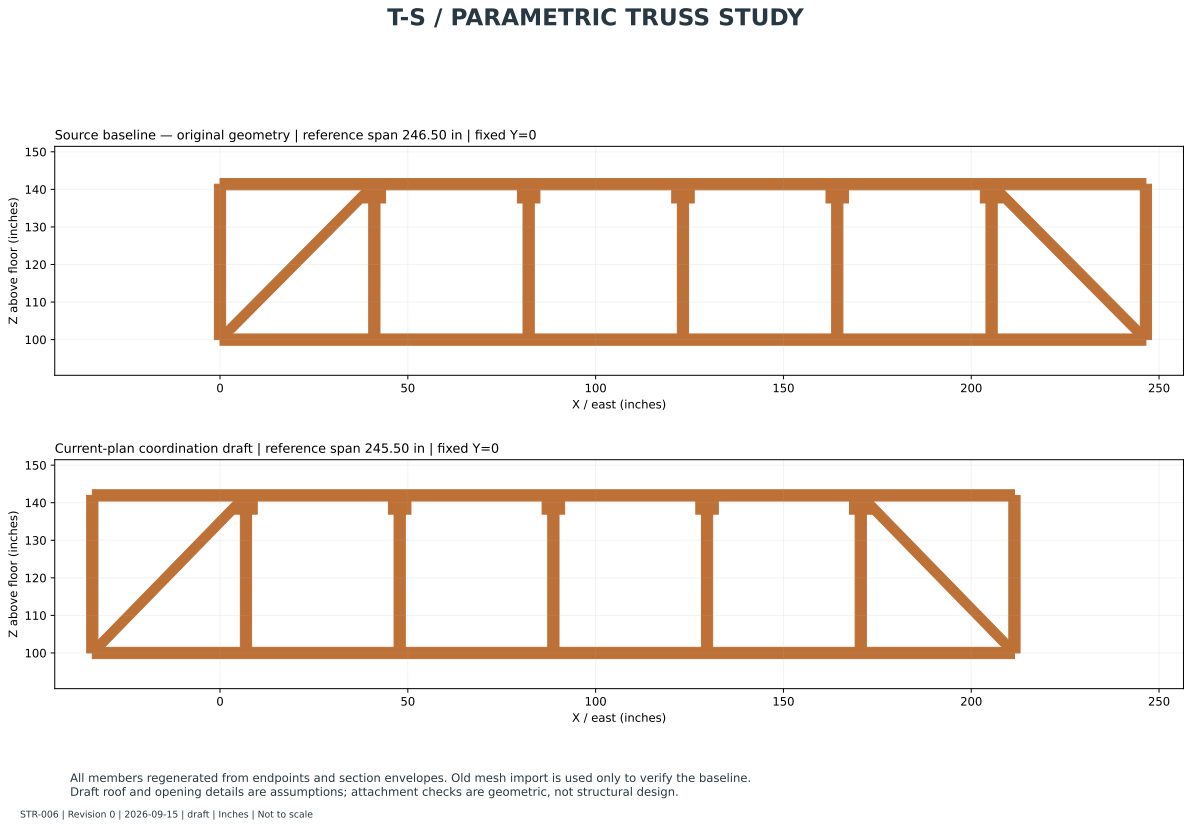
[picture p178: page 4]
X / east (inches); Z above; floor (inches)

Source baseline — original geometry | reference span 246.50 in | fixed Y=0

Current-plan coordination draft | reference span 245.50 in | fixed Y=0

All members regenerated from endpoints and section envelopes. Old mesh import is used only to verify the baseline.
Draft roof and opening details are assumptions; attachment checks are geometric, not structural design.

# T1 / PARAMETRIC TRUSS STUDY

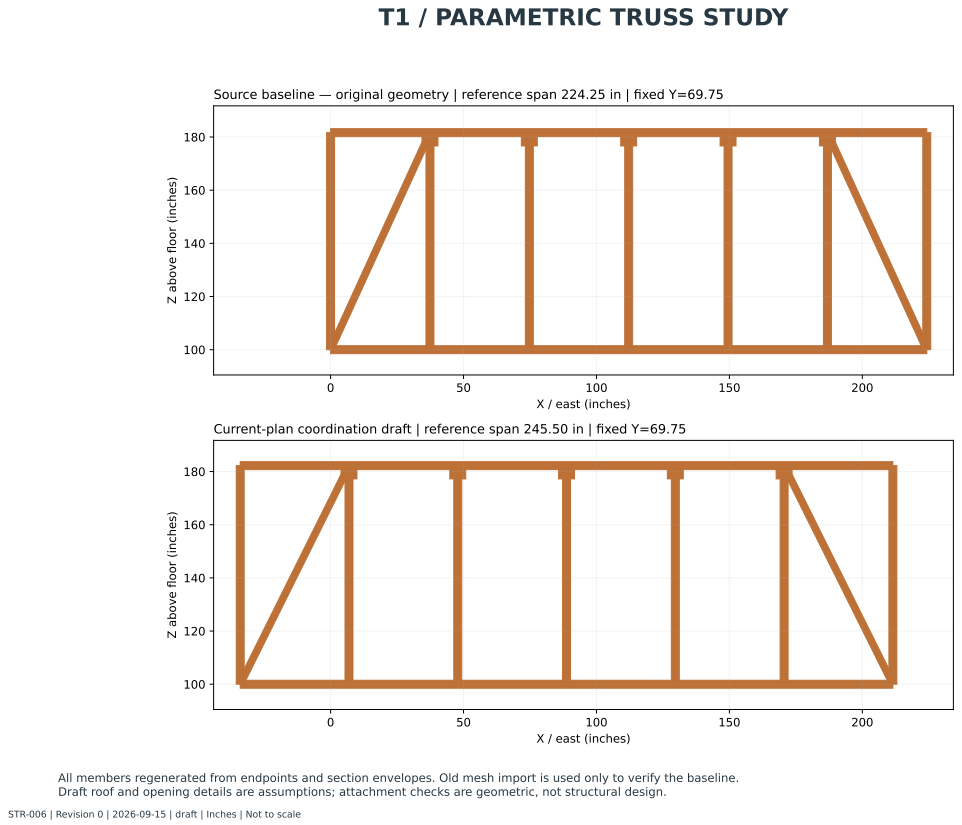
[picture p179: page 5]
X / east (inches); Z above; floor (inches)

Source baseline — original geometry | reference span 224.25 in | fixed Y=69.75

Current-plan coordination draft | reference span 245.50 in | fixed Y=69.75

# T-W / PARAMETRIC TRUSS STUDY

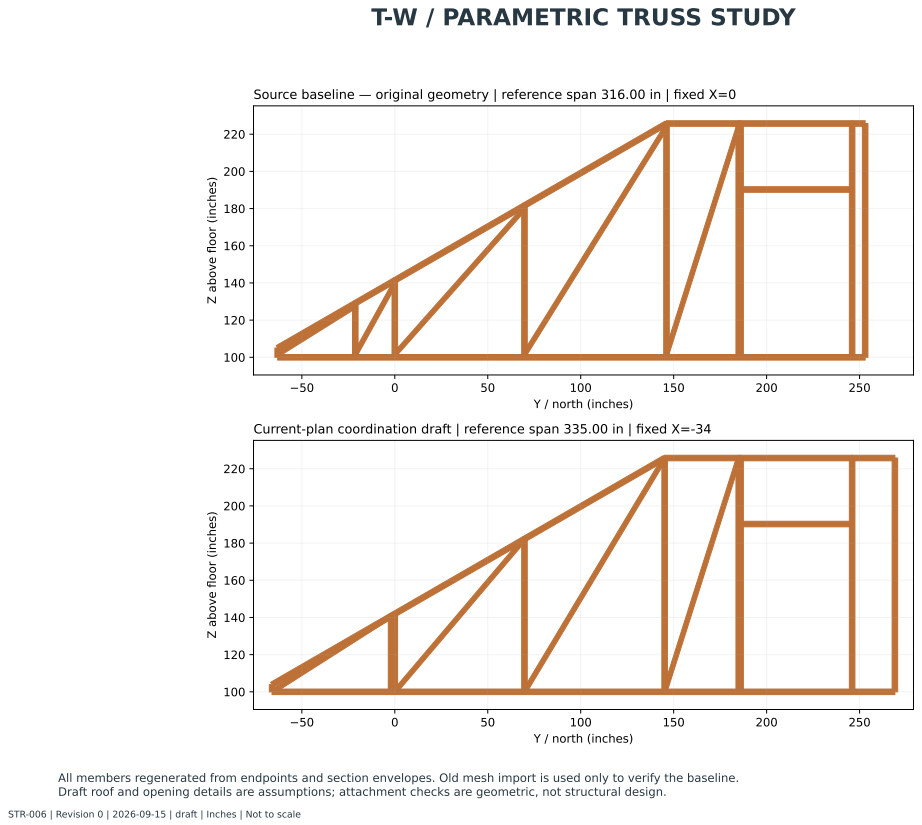
[picture p180: page 6]
Y / north (inches); Z above; floor (inches)

Source baseline — original geometry | reference span 316.00 in | fixed X=0

Current-plan coordination draft | reference span 335.00 in | fixed X=-34

# T-E / PARAMETRIC TRUSS STUDY

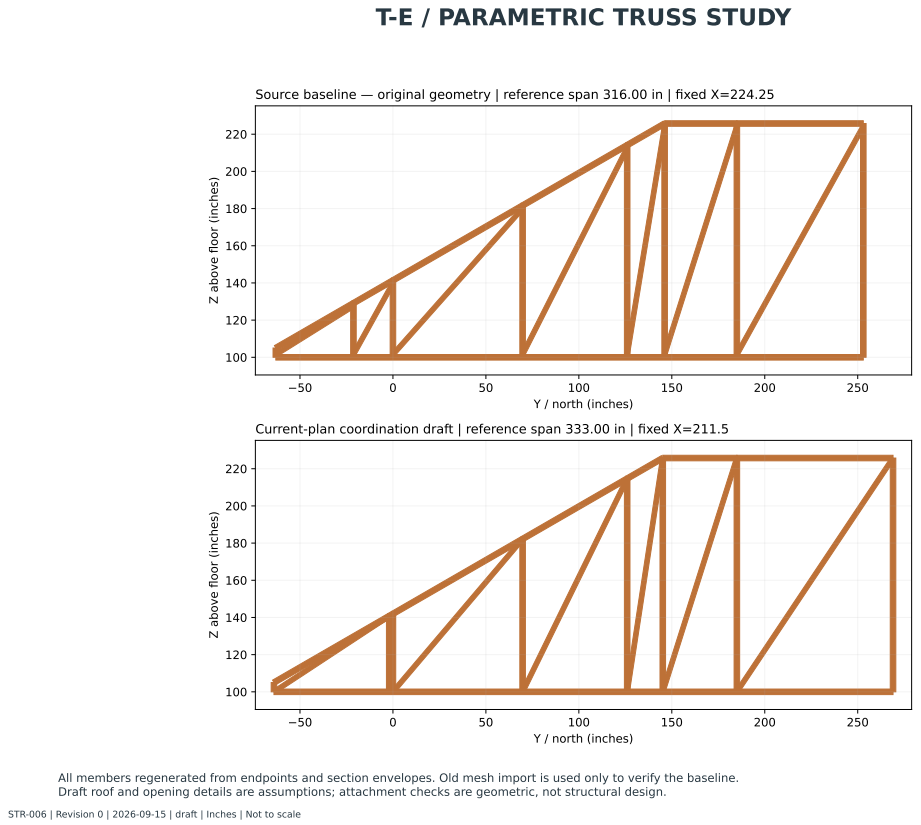
[picture p181: page 7]
Y / north (inches); Z above; floor (inches)

Source baseline — original geometry | reference span 316.00 in | fixed X=224.25

Current-plan coordination draft | reference span 333.00 in | fixed X=211.5

# T-N / PARAMETRIC TRUSS STUDY

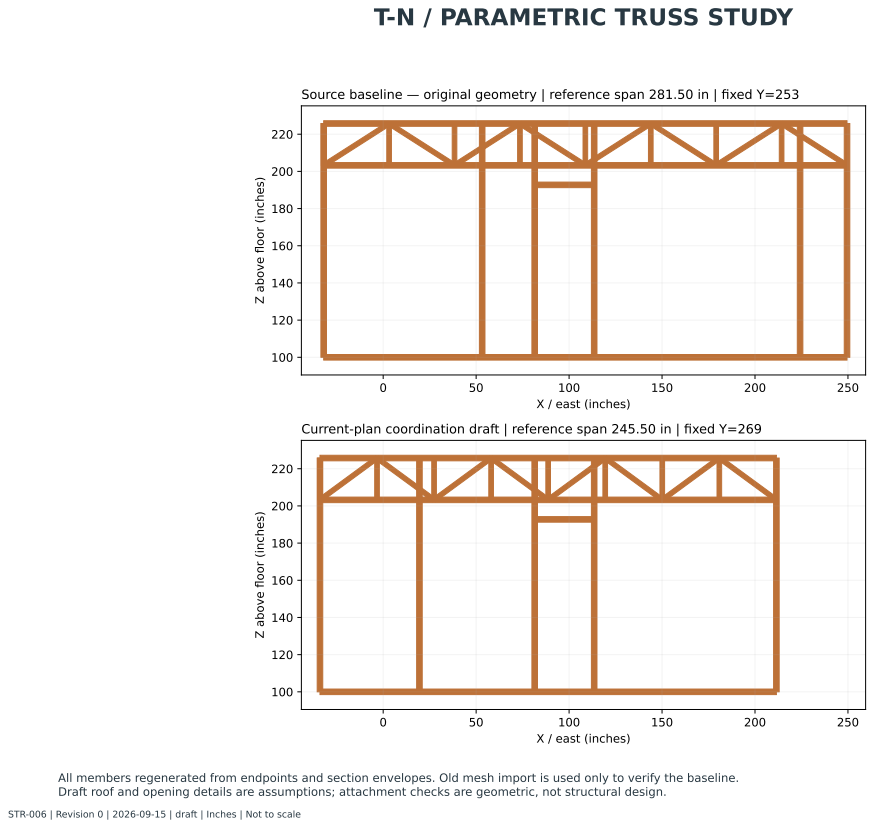
[picture p182: page 8]
X / east (inches); Z above; floor (inches)

Source baseline — original geometry | reference span 281.50 in | fixed Y=253

Current-plan coordination draft | reference span 245.50 in | fixed Y=269

# COORDINATION ITEMS / NOT YET RESOLVED

1. Draft roof retains 30 degrees and old heights, but starts at current T-SO Y=-64. Current roof design is not finalized.
2. User correction: T-W is on the far-west column row X=-34. Cross-members now extend to that row; O2/O3 are subsegments of T1/B2, not separate beams.
3. Longitudinal web tips are moved to chord axes in the draft; source-baseline geometry remains separate.
4. All 13 columns are modeled from floor datum Z=0 to frame bottom Z=98.5 using source plan-symbol sections. East-wall

heights are provisional; footing and connection details remain unresolved.

5. E-OB sits at Z98.5 with a provisional 3-inch display envelope matching truss chords; section sizing is unresolved.
OB1 elevation remains unknown.
6. T-W source uprights at Y185 and Y186 are only 1 inch apart with 3-inch envelopes: overlap retained for review.
7. T-N loft-door jamb axes X81.5/113.5 give 29 inches between 3-inch faces; source 32 inches is axis spacing.
8. T-W source door header gives 81.5 inches from loft floor to underside; source opening height needs coordination.
9. Ground-floor N1/N2 bay is 192 inches center spacing / 188 inches between 4-inch symbols, separate from the T-N loft

door.

10. T-S at Y0 is 2 inches north of S3 at Y=-2; south beam Y=-64 is 2 inches north of the south columns.
11. E-S connects to S3; E-M/E-N connect to T-E at Z98.5 as unsized references. E-M retains option B and its 1-inch offset from E-OB.
12. Truss 3-inch section envelopes have not been reconciled with the plan outside-face limit at X213.5.
13. Mesh validity and geometric connections do not establish structural stability, capacity, connection design or collision-free fabrication.
