ericbusboom/garage-renovation/report/08-solar-electrical-and-energy/figures/seasonal-production.pdf

# Same 6 kW array: tilt shifts energy toward winter

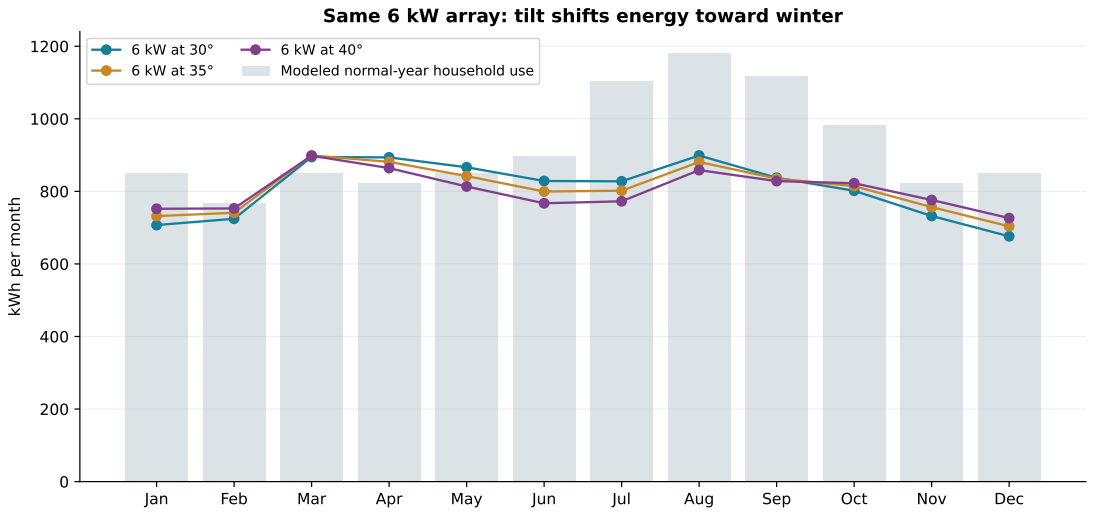
[picture p183: page 1]
Jan; Feb; Mar; Apr; May; Jun; Jul; Aug; Sep; Oct; Nov; Dec

Modeled normal-year household use

kWh per month
