ericbusboom/garage-renovation/studies/20260909.05-loading-door/north-loading-jib-full-footprint.pdf

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

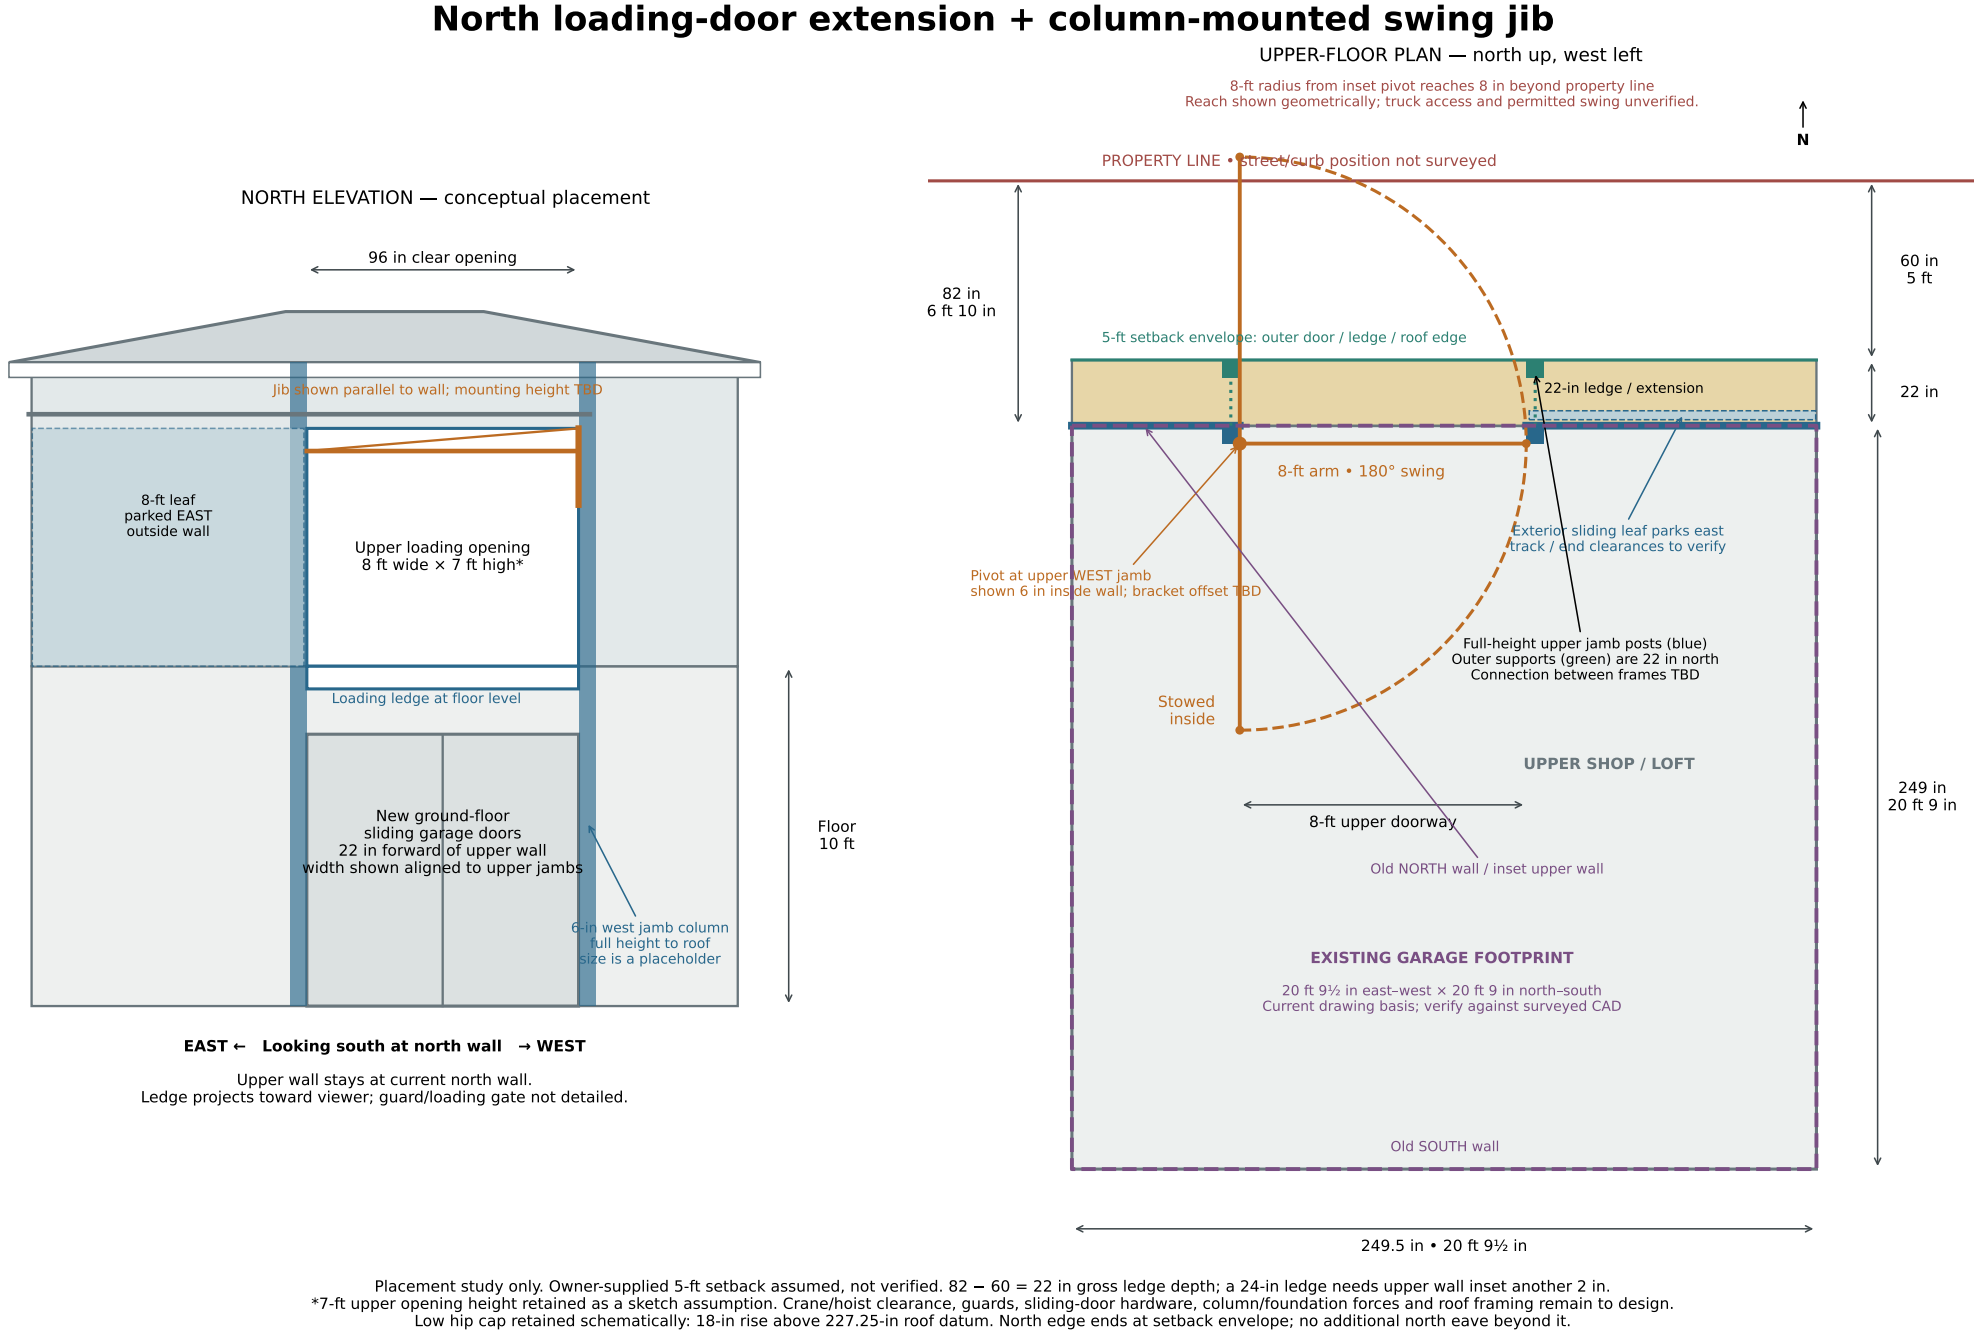
[picture p184: page 1]
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
