ericbusboom/garage-renovation/render/20260907.01-site-concepts/references/IMG_4209.jpg

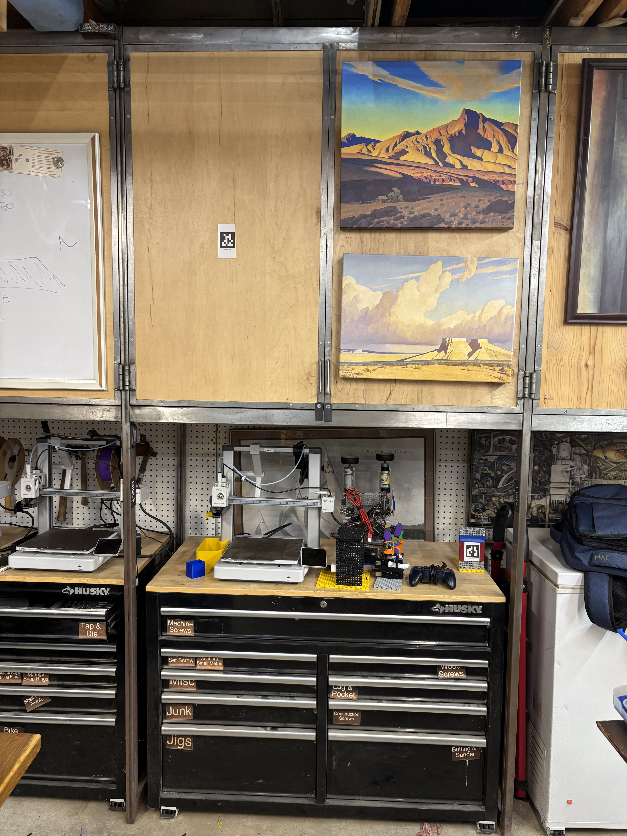
render/20260907.01-site-concepts/references/IMG_4209.jpg
