ericbusboom/garage-renovation/render/20260908.01-existing-site/references/new/IMG_4211.png

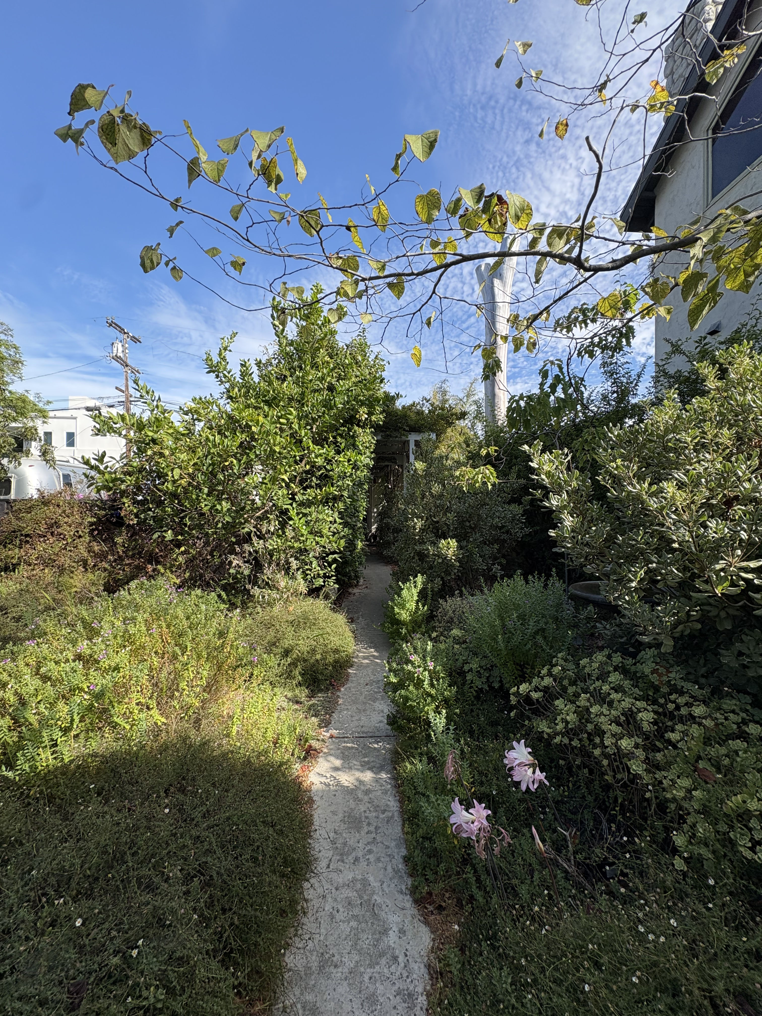
render/20260908.01-existing-site/references/new/IMG_4211.png
